vincentl/rust-photo-frame/crates/photoframe/src/config.rs

use std::collections::BTreeMap;
use std::fmt;
use std::path::{Path, PathBuf};
use std::sync::Arc;
use std::sync::atomic::{AtomicUsize, Ordering};
use std::time::{Duration, SystemTime};

use anyhow::{Context, Result, ensure};
use rand::Rng;
use rand::seq::IteratorRandom;
use serde::Deserialize;
use serde::de::{self, DeserializeOwned, Deserializer, MapAccess, SeqAccess, Unexpected, Visitor};
use serde_yaml::{Mapping, Value as YamlValue};

use crate::processing::fixed_image::FixedImageBackground;

pub use config_model::{
    AwakeScheduleConfig, GreetingScreenConfig, ScreenMessageConfig, ShowcaseConfig,
    SleepScreenConfig,
};

pub const DEFAULT_CONTROL_SOCKET_PATH: &str = "/run/photoframe/control.sock";

#[derive(Debug, Clone, Deserialize)]
#[serde(rename_all = "kebab-case", default, deny_unknown_fields)]
pub struct GlobalPhotoSettings {
    /// GPU render oversample factor relative to screen size (1.0 = native).
    pub oversample: f32,
    /// Time an image remains fully visible before starting a transition, in ms.
    pub dwell_ms: u64,
    /// Global maximum enlargement applied to the photo when fitting inside the mat.
    pub max_upscale_factor: f32,
}

impl Default for GlobalPhotoSettings {
    fn default() -> Self {
        Self {
            oversample: 1.0,
            dwell_ms: 2000,
            max_upscale_factor: 1.0,
        }
    }
}

#[derive(Debug, Clone, Deserialize)]
#[serde(rename_all = "kebab-case")]
pub struct MattingOptions {
    #[serde(default = "MattingOptions::default_minimum_percentage")]
    pub minimum_mat_percentage: f32,
    #[serde(default, flatten)]
    pub style: MattingMode,
    #[serde(default, skip_deserializing)]
    pub runtime: MattingRuntime,
}

/// Canonicalized matting configuration entries and their selection metadata.
///
/// Deserialization expands palette-based definitions (e.g. multiple
/// `fixed-color` entries) into the concrete `options` stored here. Each entry
/// in `selection` references these canonical slots by index so duplicates can
/// coexist without clobbering configuration fields.
#[derive(Debug, Clone)]
pub struct MattingConfig {
    selection: MattingSelection,
    options: Vec<MattingOptions>,
    fill_when_fits: Option<FillWhenFits>,
}

/// Opt-in behavior that renders photos whose aspect ratio is already close to
/// the display's edge-to-edge (full-bleed, cover-cropped) instead of matting
/// them. Evaluated per photo *before* mat selection.
#[derive(Debug, Clone, Copy, Deserialize)]
#[serde(rename_all = "kebab-case", deny_unknown_fields)]
pub struct FillWhenFits {
    /// A photo is eligible when filling the screen crops less than this
    /// percentage from the single overflowing axis.
    #[serde(default = "FillWhenFits::default_maximum_crop_percentage")]
    pub maximum_crop_percentage: f32,
    /// For an eligible photo, the biased-coin probability of actually skipping
    /// the mat. `1.0` always fills when eligible; `0.0` never does.
    #[serde(default = "FillWhenFits::default_skip_matting_probability")]
    pub skip_matting_probability: f32,
}

impl FillWhenFits {
    const fn default_maximum_crop_percentage() -> f32 {
        5.0
    }

    const fn default_skip_matting_probability() -> f32 {
        1.0
    }

    /// Returns true when the photo should be rendered full-bleed (no mat).
    ///
    /// Eligibility requires both that the cover-crop trims less than
    /// `maximum_crop_percentage` from the overflowing axis, and that the image
    /// is large enough to fill the screen within `max_upscale` (so a tiny but
    /// correctly-proportioned image is not blown up past the budget). When
    /// eligible, a biased coin decides the outcome.
    pub fn should_fill<R: Rng + ?Sized>(
        &self,
        img_w: u32,
        img_h: u32,
        screen_w: u32,
        screen_h: u32,
        max_upscale: f32,
        rng: &mut R,
    ) -> bool {
        let iw = img_w.max(1) as f32;
        let ih = img_h.max(1) as f32;
        let sw = screen_w.max(1) as f32;
        let sh = screen_h.max(1) as f32;

        let aspect_img = iw / ih;
        let aspect_screen = sw / sh;
        let (lo, hi) = if aspect_img <= aspect_screen {
            (aspect_img, aspect_screen)
        } else {
            (aspect_screen, aspect_img)
        };
        if hi <= 0.0 {
            return false;
        }
        let crop_fraction = 1.0 - lo / hi;
        let max_crop = (self.maximum_crop_percentage / 100.0).max(0.0);
        if crop_fraction > max_crop {
            return false;
        }

        let cover_scale = (sw / iw).max(sh / ih);
        if cover_scale > max_upscale.max(1.0) {
            return false;
        }

        let prob = self.skip_matting_probability;
        if prob >= 1.0 {
            return true;
        }
        if prob <= 0.0 {
            return false;
        }
        rng.random_bool(prob as f64)
    }

    /// Reject NaN / out-of-range values that serde cannot express as defaults.
    /// `should_fill` feeds `skip_matting_probability` straight into
    /// `rng.random_bool`, which panics for any value outside `[0.0, 1.0]`
    /// (NaN included), so this must run before any photo is rendered.
    pub fn validate(&self) -> Result<()> {
        ensure!(
            self.maximum_crop_percentage.is_finite()
                && (0.0..=100.0).contains(&self.maximum_crop_percentage),
            "matting.fill-when-fits.maximum-crop-percentage must be between 0 and 100"
        );
        ensure!(
            self.skip_matting_probability.is_finite()
                && (0.0..=1.0).contains(&self.skip_matting_probability),
            "matting.fill-when-fits.skip-matting-probability must be between 0.0 and 1.0 \
             (a 0-1 fraction, not a 0-100 percentage)"
        );
        Ok(())
    }
}

#[derive(Debug, Clone, Copy, PartialEq, Eq, Deserialize)]
#[serde(rename_all = "kebab-case")]
enum PipelineSelection {
    Fixed,
    Random,
    Sequential,
}

#[derive(Debug)]
struct PipelineEntry<K> {
    kind: K,
    fields: Vec<(String, YamlValue)>,
}

impl<'de, K> Deserialize<'de> for PipelineEntry<K>
where
    K: Deserialize<'de>,
{
    fn deserialize<D>(deserializer: D) -> Result<Self, D::Error>
    where
        D: Deserializer<'de>,
    {
        deserializer.deserialize_map(PipelineEntryVisitor::<K> {
            marker: std::marker::PhantomData,
        })
    }
}

struct PipelineEntryVisitor<K> {
    marker: std::marker::PhantomData<K>,
}

impl<'de, K> Visitor<'de> for PipelineEntryVisitor<K>
where
    K: Deserialize<'de>,
{
    type Value = PipelineEntry<K>;

    fn expecting(&self, formatter: &mut fmt::Formatter) -> fmt::Result {
        formatter.write_str("a pipeline entry map with a kind tag")
    }

    fn visit_map<A>(self, mut map: A) -> Result<Self::Value, A::Error>
    where
        A: MapAccess<'de>,
    {
        let mut kind: Option<K> = None;
        let mut fields = Vec::new();
        while let Some(key) = map.next_key::<String>()? {
            if key == "kind" {
                if kind.is_some() {
                    return Err(de::Error::duplicate_field("kind"));
                }
                kind = Some(map.next_value()?);
            } else {
                let value = map.next_value::<YamlValue>()?;
                fields.push((key, value));
            }
        }

        let kind = kind.ok_or_else(|| de::Error::missing_field("kind"))?;
        Ok(PipelineEntry { kind, fields })
    }
}

fn resolve_pipeline_selection<E>(
    requested: Option<PipelineSelection>,
    len: usize,
    context: &str,
) -> Result<PipelineSelection, E>
where
    E: de::Error,
{
    if len == 0 {
        return Err(de::Error::custom(format!(
            "{} configuration must include at least one active entry",
            context
        )));
    }

    match requested {
        Some(PipelineSelection::Fixed) => {
            if len != 1 {
                return Err(de::Error::custom(format!(
                    "{} selection 'fixed' requires exactly one active entry",
                    context
                )));
            }
            Ok(PipelineSelection::Fixed)
        }
        Some(selection) => Ok(selection),
        None => {
            if len == 1 {
                Ok(PipelineSelection::Fixed)
            } else {
                Ok(PipelineSelection::Random)
            }
        }
    }
}

#[derive(Debug, Clone)]
pub struct SequentialState {
    next_index: Arc<AtomicUsize>,
}

impl Default for SequentialState {
    fn default() -> Self {
        Self {
            next_index: Arc::new(AtomicUsize::new(0)),
        }
    }
}

impl SequentialState {
    fn next(&self, len: usize) -> usize {
        self.next_index.fetch_add(1, Ordering::Relaxed) % len
    }
}

#[derive(Debug, Clone, Copy, PartialEq, Eq)]
pub struct SelectionEntry<K: Copy> {
    pub index: usize,
    pub kind: K,
}

#[derive(Clone, Copy, Debug)]
pub struct SelectedOption<'a, K: Copy, O> {
    pub entry: SelectionEntry<K>,
    pub option: &'a O,
}

enum SelectionEntries<'a, K: Copy> {
    Single(Option<SelectionEntry<K>>),
    Slice(std::iter::Copied<std::slice::Iter<'a, SelectionEntry<K>>>),
}

impl<'a, K: Copy> SelectionEntries<'a, K> {
    fn single(entry: SelectionEntry<K>) -> Self {
        Self::Single(Some(entry))
    }

    fn from_slice(entries: &'a [SelectionEntry<K>]) -> Self {
        Self::Slice(entries.iter().copied())
    }
}

impl<'a, K: Copy> Iterator for SelectionEntries<'a, K> {
    type Item = SelectionEntry<K>;

    fn next(&mut self) -> Option<Self::Item> {
        match self {
            Self::Single(entry) => entry.take(),
            Self::Slice(iter) => iter.next(),
        }
    }
}

trait SelectedLookup<K: Copy, O> {
    fn lookup(&self, entry: SelectionEntry<K>) -> Option<&O>;
}

impl<K: Copy, O> SelectedLookup<K, O> for [O] {
    fn lookup(&self, entry: SelectionEntry<K>) -> Option<&O> {
        self.get(entry.index)
    }
}

impl<K: Copy + Ord, O> SelectedLookup<K, O> for BTreeMap<K, O> {
    fn lookup(&self, entry: SelectionEntry<K>) -> Option<&O> {
        self.get(&entry.kind)
    }
}

struct SelectedIter<'a, K: Copy, O, S>
where
    S: SelectedLookup<K, O> + ?Sized,
{
    entries: SelectionEntries<'a, K>,
    options: &'a S,
    marker: std::marker::PhantomData<&'a O>,
}

impl<'a, K: Copy, O, S> SelectedIter<'a, K, O, S>
where
    S: SelectedLookup<K, O> + ?Sized,
{
    fn new(entries: SelectionEntries<'a, K>, options: &'a S) -> Self {
        Self {
            entries,
            options,
            marker: std::marker::PhantomData,
        }
    }
}

impl<'a, K: Copy, O, S> Iterator for SelectedIter<'a, K, O, S>
where
    O: 'a,
    S: SelectedLookup<K, O> + ?Sized,
{
    type Item = SelectedOption<'a, K, O>;

    fn next(&mut self) -> Option<Self::Item> {
        for entry in self.entries.by_ref() {
            if let Some(option) = self.options.lookup(entry) {
                return Some(SelectedOption { entry, option });
            }
        }
        None
    }
}

#[derive(Debug, Clone)]
pub enum MattingSelection {
    Fixed(SelectionEntry<MattingKind>),
    Random(Arc<[SelectionEntry<MattingKind>]>),
    Sequential {
        entries: Arc<[SelectionEntry<MattingKind>]>,
        runtime: SequentialState,
    },
}

pub type SelectedMatting<'a> = SelectedOption<'a, MattingKind, MattingOptions>;

impl PartialEq for MattingSelection {
    fn eq(&self, other: &Self) -> bool {
        match (self, other) {
            (MattingSelection::Fixed(a), MattingSelection::Fixed(b)) => a == b,
            (MattingSelection::Random(a), MattingSelection::Random(b)) => a.as_ref() == b.as_ref(),
            (
                MattingSelection::Sequential { entries: a, .. },
                MattingSelection::Sequential { entries: b, .. },
            ) => a.as_ref() == b.as_ref(),
            _ => false,
        }
    }
}

impl Eq for MattingSelection {}

#[derive(Debug, Clone, Copy, PartialEq, Eq)]
pub enum StudioMatColor {
    Rgb([u8; 3]),
    PhotoAverage,
}

impl StudioMatColor {
    fn resolve(self, fallback: [f32; 3]) -> [f32; 3] {
        match self {
            StudioMatColor::Rgb(rgb) => [
                (rgb[0] as f32) / 255.0,
                (rgb[1] as f32) / 255.0,
                (rgb[2] as f32) / 255.0,
            ],
            StudioMatColor::PhotoAverage => fallback,
        }
    }
}

impl<'de> Deserialize<'de> for StudioMatColor {
    fn deserialize<D>(deserializer: D) -> Result<Self, D::Error>
    where
        D: Deserializer<'de>,
    {
        struct MatColorVisitor;

        impl<'de> Visitor<'de> for MatColorVisitor {
            type Value = StudioMatColor;

            fn expecting(&self, formatter: &mut fmt::Formatter) -> fmt::Result {
                formatter.write_str("an RGB triple or the string 'photo-average'")
            }

            fn visit_str<E>(self, value: &str) -> Result<Self::Value, E>
            where
                E: de::Error,
            {
                match value {
                    "photo-average" => Ok(StudioMatColor::PhotoAverage),
                    other => Err(de::Error::invalid_value(Unexpected::Str(other), &self)),
                }
            }

            fn visit_string<E>(self, value: String) -> Result<Self::Value, E>
            where
                E: de::Error,
            {
                self.visit_str(&value)
            }

            fn visit_seq<A>(self, mut seq: A) -> Result<Self::Value, A::Error>
            where
                A: SeqAccess<'de>,
            {
                let mut rgb = [0u8; 3];
                for (index, channel) in rgb.iter_mut().enumerate() {
                    *channel = seq
                        .next_element()?
                        .ok_or_else(|| de::Error::invalid_length(index, &self))?;
                }
                if seq.next_element::<de::IgnoredAny>()?.is_some() {
                    return Err(de::Error::invalid_length(4, &self));
                }
                Ok(StudioMatColor::Rgb(rgb))
            }
        }

        deserializer.deserialize_any(MatColorVisitor)
    }
}

#[derive(Debug, Clone, Default)]
pub struct MattingRuntime {
    fixed_color: Option<[u8; 3]>,
    studio_color: Option<StudioMatColor>,
    passe_partout_color: Option<StudioMatColor>,
    vignette_color: Option<StudioMatColor>,
    drop_shadow_color: Option<StudioMatColor>,
    fixed_image: Option<Arc<FixedImageBackground>>,
}

impl MattingRuntime {
    pub fn fixed_color(&self) -> Option<[u8; 3]> {
        self.fixed_color
    }

    pub fn studio_color(&self, fallback: [f32; 3]) -> Option<[f32; 3]> {
        self.studio_color.map(|color| color.resolve(fallback))
    }

    pub fn passe_partout_color(&self, fallback: [f32; 3]) -> Option<[f32; 3]> {
        self.passe_partout_color
            .map(|color| color.resolve(fallback))
    }

    pub fn vignette_color(&self, fallback: [f32; 3]) -> Option<[f32; 3]> {
        self.vignette_color.map(|color| color.resolve(fallback))
    }

    pub fn drop_shadow_color(&self, fallback: [f32; 3]) -> Option<[f32; 3]> {
        self.drop_shadow_color.map(|color| color.resolve(fallback))
    }

    pub fn fixed_image(&self) -> Option<Arc<FixedImageBackground>> {
        self.fixed_image.clone()
    }
}

impl MattingKind {
    const ALL: &'static [Self] = &[
        Self::FixedColor,
        Self::Blur,
        Self::Studio,
        Self::FixedImage,
        Self::Gradient,
        Self::Vignette,
        Self::CinematicBlur,
        Self::PassePartout,
        Self::DropShadow,
    ];
    const NAMES: &'static [&'static str] = &[
        "fixed-color",
        "blur",
        "studio",
        "fixed-image",
        "gradient",
        "vignette",
        "cinematic-blur",
        "passe-partout",
        "drop-shadow",
    ];

    fn as_str(&self) -> &'static str {
        match self {
            Self::FixedColor => "fixed-color",
            Self::Blur => "blur",
            Self::Studio => "studio",
            Self::FixedImage => "fixed-image",
            Self::Gradient => "gradient",
            Self::Vignette => "vignette",
            Self::CinematicBlur => "cinematic-blur",
            Self::PassePartout => "passe-partout",
            Self::DropShadow => "drop-shadow",
        }
    }
}

impl fmt::Display for MattingKind {
    fn fmt(&self, f: &mut fmt::Formatter<'_>) -> fmt::Result {
        f.write_str(self.as_str())
    }
}

impl<'de> Deserialize<'de> for MattingKind {
    fn deserialize<D>(deserializer: D) -> Result<Self, D::Error>
    where
        D: Deserializer<'de>,
    {
        let raw = String::deserialize(deserializer)?;
        for kind in Self::ALL {
            if raw == kind.as_str() {
                return Ok(*kind);
            }
        }
        Err(de::Error::unknown_variant(&raw, Self::NAMES))
    }
}

#[derive(Debug, Clone, Copy, PartialEq, Eq, PartialOrd, Ord)]
pub enum MattingKind {
    FixedColor,
    Blur,
    Studio,
    FixedImage,
    Gradient,
    Vignette,
    CinematicBlur,
    PassePartout,
    DropShadow,
}

#[derive(Debug, Clone, Deserialize)]
#[serde(tag = "type", rename_all = "kebab-case")]
pub enum MattingMode {
    FixedColor {
        #[serde(default = "MattingMode::default_fixed_color_palette")]
        colors: Vec<[u8; 3]>,
    },
    Blur {
        #[serde(default = "MattingMode::default_blur_sigma")]
        sigma: f32,
        #[serde(
            default = "MattingMode::default_blur_sample_scale",
            rename = "sample-scale"
        )]
        sample_scale: f32,
        #[serde(default)]
        backend: BlurBackend,
    },
    Studio {
        #[serde(default = "MattingMode::default_studio_colors")]
        colors: Vec<StudioMatColor>,
        #[serde(
            default = "MattingMode::default_studio_bevel_width_px",
            rename = "bevel-width-px"
        )]
        bevel_width_px: f32,
        #[serde(
            default = "MattingMode::default_studio_bevel_color",
            rename = "bevel-color"
        )]
        bevel_color: [u8; 3],
        #[serde(
            default = "MattingMode::default_studio_texture_strength",
            rename = "texture-strength"
        )]
        texture_strength: f32,
        #[serde(
            default = "MattingMode::default_studio_warp_period_px",
            rename = "warp-period-px"
        )]
        warp_period_px: f32,
        #[serde(
            default = "MattingMode::default_studio_weft_period_px",
            rename = "weft-period-px"
        )]
        weft_period_px: f32,
    },
    FixedImage {
        #[serde(
            default,
            rename = "path",
            deserialize_with = "deserialize_fixed_image_paths"
        )]
        paths: Vec<PathBuf>,
        #[serde(default)]
        fit: FixedImageFit,
    },
    Gradient {
        #[serde(
            default = "MattingMode::default_gradient_start",
            rename = "start-color"
        )]
        start_color: [u8; 3],
        #[serde(default = "MattingMode::default_gradient_end", rename = "end-color")]
        end_color: [u8; 3],
        #[serde(default)]
        direction: GradientDirection,
        #[serde(
            default = "MattingMode::default_gradient_angle",
            rename = "angle-degrees"
        )]
        angle_degrees: f32,
    },
    Vignette {
        #[serde(default = "MattingMode::default_vignette_colors")]
        colors: Vec<StudioMatColor>,
        #[serde(default = "MattingMode::default_vignette_strength")]
        strength: f32,
        #[serde(default = "MattingMode::default_vignette_radius")]
        radius: f32,
        #[serde(default = "MattingMode::default_vignette_softness")]
        softness: f32,
    },
    CinematicBlur {
        #[serde(default = "MattingMode::default_blur_sigma")]
        sigma: f32,
        #[serde(
            default = "MattingMode::default_blur_sample_scale",
            rename = "sample-scale"
        )]
        sample_scale: f32,
        #[serde(default)]
        backend: BlurBackend,
        #[serde(default = "MattingMode::default_cinematic_darken")]
        darken: f32,
        #[serde(
            default = "MattingMode::default_cinematic_vignette_strength",
            rename = "vignette-strength"
        )]
        vignette_strength: f32,
    },
    PassePartout {
        #[serde(default = "MattingMode::default_studio_colors")]
        colors: Vec<StudioMatColor>,
        #[serde(
            default = "MattingMode::default_studio_bevel_width_px",
            rename = "bevel-width-px"
        )]
        bevel_width_px: f32,
        #[serde(
            default = "MattingMode::default_studio_bevel_color",
            rename = "bevel-color"
        )]
        bevel_color: [u8; 3],
    },
    DropShadow {
        #[serde(default = "MattingMode::default_drop_shadow_colors")]
        colors: Vec<StudioMatColor>,
        #[serde(
            default = "MattingMode::default_drop_shadow_shadow_color",
            rename = "shadow-color"
        )]
        shadow_color: [u8; 3],
        #[serde(
            default = "MattingMode::default_drop_shadow_opacity",
            rename = "shadow-opacity"
        )]
        shadow_opacity: f32,
        #[serde(
            default = "MattingMode::default_drop_shadow_blur_px",
            rename = "shadow-blur-px"
        )]
        shadow_blur_px: f32,
        #[serde(
            default = "MattingMode::default_drop_shadow_offset_px",
            rename = "shadow-offset-px"
        )]
        shadow_offset_px: [i32; 2],
    },
}

#[derive(Debug, Clone, Copy, Deserialize)]
#[serde(rename_all = "kebab-case")]
pub enum BlurBackend {
    Cpu,
    Neon,
}

#[derive(Debug, Clone, Copy, PartialEq, Eq, Deserialize)]
#[serde(rename_all = "kebab-case")]
pub enum FixedImageFit {
    Cover,
    Contain,
    Stretch,
}

impl Default for BlurBackend {
    fn default() -> Self {
        Self::Neon
    }
}

impl Default for FixedImageFit {
    fn default() -> Self {
        Self::Cover
    }
}

#[derive(Debug, Clone, Copy, PartialEq, Eq, Deserialize)]
#[serde(rename_all = "kebab-case")]
pub enum GradientDirection {
    Vertical,
    Horizontal,
    Radial,
}

impl Default for GradientDirection {
    fn default() -> Self {
        Self::Vertical
    }
}

fn deserialize_fixed_image_paths<'de, D>(deserializer: D) -> Result<Vec<PathBuf>, D::Error>
where
    D: Deserializer<'de>,
{
    struct PathsVisitor;

    impl<'de> Visitor<'de> for PathsVisitor {
        type Value = Vec<PathBuf>;

        fn expecting(&self, formatter: &mut fmt::Formatter<'_>) -> fmt::Result {
            formatter.write_str("a path string or a list of paths")
        }

        fn visit_str<E>(self, value: &str) -> Result<Self::Value, E>
        where
            E: de::Error,
        {
            Ok(vec![PathBuf::from(value)])
        }

        fn visit_string<E>(self, value: String) -> Result<Self::Value, E>
        where
            E: de::Error,
        {
            self.visit_str(&value)
        }

        fn visit_seq<A>(self, mut seq: A) -> Result<Self::Value, A::Error>
        where
            A: de::SeqAccess<'de>,
        {
            let mut paths = Vec::new();
            while let Some(path) = seq.next_element::<PathBuf>()? {
                paths.push(path);
            }
            Ok(paths)
        }
    }

    deserializer.deserialize_any(PathsVisitor)
}

impl Default for MattingOptions {
    fn default() -> Self {
        Self {
            minimum_mat_percentage: Self::default_minimum_percentage(),
            style: MattingMode::default(),
            runtime: MattingRuntime::default(),
        }
    }
}

impl MattingOptions {
    const fn default_minimum_percentage() -> f32 {
        0.0
    }

    pub fn prepare_runtime(&mut self) -> Result<()> {
        ensure!(
            self.minimum_mat_percentage.is_finite()
                && (0.0..=100.0).contains(&self.minimum_mat_percentage),
            "matting.minimum-mat-percentage must be between 0 and 100 (got {})",
            self.minimum_mat_percentage
        );
        self.runtime = MattingRuntime::default();
        if let MattingMode::FixedColor { colors, .. } = &self.style {
            ensure!(
                !colors.is_empty(),
                "matting.fixed-color.colors must include at least one entry",
            );
            self.runtime.fixed_color = colors.first().copied();
        }
        if let MattingMode::Studio { colors, .. } = &self.style {
            ensure!(
                !colors.is_empty(),
                "matting.studio.colors must include at least one entry",
            );
            self.runtime.studio_color = colors.first().copied();
        }
        if let MattingMode::PassePartout { colors, .. } = &self.style {
            ensure!(
                !colors.is_empty(),
                "matting.passe-partout.colors must include at least one entry",
            );
            self.runtime.passe_partout_color = colors.first().copied();
        }
        if let MattingMode::Vignette { colors, .. } = &self.style {
            ensure!(
                !colors.is_empty(),
                "matting.vignette.colors must include at least one entry",
            );
            self.runtime.vignette_color = colors.first().copied();
        }
        if let MattingMode::DropShadow { colors, .. } = &self.style {
            ensure!(
                !colors.is_empty(),
                "matting.drop-shadow.colors must include at least one entry",
            );
            self.runtime.drop_shadow_color = colors.first().copied();
        }
        if let MattingMode::FixedImage { paths, .. } = &self.style {
            if paths.is_empty() {
                return Ok(());
            }

            for path in paths {
                match FixedImageBackground::new(path.clone()) {
                    Ok(background) => {
                        self.runtime.fixed_image = Some(Arc::new(background));
                        break;
                    }
                    Err(err) => {
                        tracing::warn!(
                            path = %path.display(),
                            error = %err,
                            "skipping fixed background image that failed to prepare"
                        );
                    }
                }
            }

            if self.runtime.fixed_image.is_none() {
                tracing::warn!(
                    "all configured fixed-image backgrounds failed to load; disabling fixed-image matting"
                );
            }
        }
        Ok(())
    }

    pub fn fixed_color(&self) -> Option<[u8; 3]> {
        match &self.style {
            MattingMode::FixedColor { colors, .. } => colors.first().copied(),
            _ => None,
        }
    }
}

impl MattingOptions {
    fn with_kind(kind: MattingKind, base: MattingOptionBuilder) -> Self {
        let style = match kind {
            MattingKind::FixedColor => MattingMode::FixedColor {
                colors: base
                    .fixed_colors
                    .unwrap_or_else(MattingMode::default_fixed_color_palette),
            },
            MattingKind::Blur => MattingMode::Blur {
                sigma: base.sigma.unwrap_or_else(MattingMode::default_blur_sigma),
                sample_scale: base
                    .sample_scale
                    .unwrap_or_else(MattingMode::default_blur_sample_scale),
                backend: base.blur_backend.unwrap_or_default(),
            },
            MattingKind::Studio => MattingMode::Studio {
                colors: base
                    .studio_colors
                    .unwrap_or_else(MattingMode::default_studio_colors),
                bevel_width_px: base
                    .bevel_width_px
                    .unwrap_or_else(MattingMode::default_studio_bevel_width_px),
                bevel_color: base
                    .bevel_color
                    .unwrap_or_else(MattingMode::default_studio_bevel_color),
                texture_strength: base
                    .texture_strength
                    .unwrap_or_else(MattingMode::default_studio_texture_strength),
                warp_period_px: base
                    .warp_period_px
                    .unwrap_or_else(MattingMode::default_studio_warp_period_px),
                weft_period_px: base
                    .weft_period_px
                    .unwrap_or_else(MattingMode::default_studio_weft_period_px),
            },
            MattingKind::FixedImage => MattingMode::FixedImage {
                paths: base
                    .fixed_image_paths
                    .expect("fixed-image matting must supply a path"),
                fit: base.fixed_image_fit.unwrap_or_default(),
            },
            MattingKind::Gradient => MattingMode::Gradient {
                start_color: base
                    .gradient_start
                    .unwrap_or_else(MattingMode::default_gradient_start),
                end_color: base
                    .gradient_end
                    .unwrap_or_else(MattingMode::default_gradient_end),
                direction: base.gradient_direction.unwrap_or_default(),
                angle_degrees: base
                    .gradient_angle
                    .unwrap_or_else(MattingMode::default_gradient_angle),
            },
            MattingKind::Vignette => MattingMode::Vignette {
                colors: base
                    .vignette_colors
                    .unwrap_or_else(MattingMode::default_vignette_colors),
                strength: base
                    .vignette_strength
                    .unwrap_or_else(MattingMode::default_vignette_strength),
                radius: base
                    .vignette_radius
                    .unwrap_or_else(MattingMode::default_vignette_radius),
                softness: base
                    .vignette_softness
                    .unwrap_or_else(MattingMode::default_vignette_softness),
            },
            MattingKind::CinematicBlur => MattingMode::CinematicBlur {
                sigma: base.sigma.unwrap_or_else(MattingMode::default_blur_sigma),
                sample_scale: base
                    .sample_scale
                    .unwrap_or_else(MattingMode::default_blur_sample_scale),
                backend: base.blur_backend.unwrap_or_default(),
                darken: base
                    .cinematic_darken
                    .unwrap_or_else(MattingMode::default_cinematic_darken),
                vignette_strength: base
                    .cinematic_vignette_strength
                    .unwrap_or_else(MattingMode::default_cinematic_vignette_strength),
            },
            MattingKind::PassePartout => MattingMode::PassePartout {
                colors: base
                    .passe_partout_colors
                    .unwrap_or_else(MattingMode::default_studio_colors),
                bevel_width_px: base
                    .bevel_width_px
                    .unwrap_or_else(MattingMode::default_studio_bevel_width_px),
                bevel_color: base
                    .bevel_color
                    .unwrap_or_else(MattingMode::default_studio_bevel_color),
            },
            MattingKind::DropShadow => MattingMode::DropShadow {
                colors: base
                    .drop_shadow_colors
                    .unwrap_or_else(MattingMode::default_drop_shadow_colors),
                shadow_color: base
                    .drop_shadow_shadow_color
                    .unwrap_or_else(MattingMode::default_drop_shadow_shadow_color),
                shadow_opacity: base
                    .drop_shadow_opacity
                    .unwrap_or_else(MattingMode::default_drop_shadow_opacity),
                shadow_blur_px: base
                    .drop_shadow_blur_px
                    .unwrap_or_else(MattingMode::default_drop_shadow_blur_px),
                shadow_offset_px: base
                    .drop_shadow_offset_px
                    .unwrap_or_else(MattingMode::default_drop_shadow_offset_px),
            },
        };
        Self {
            minimum_mat_percentage: base
                .minimum_mat_percentage
                .unwrap_or_else(Self::default_minimum_percentage),
            style,
            runtime: MattingRuntime::default(),
        }
    }

    /// Build a `MattingOptions` with showcase-appropriate defaults for `kind`.
    /// For `FixedImage`, `fixed_image_path` must be `Some` (callers skip it when None).
    pub(crate) fn default_for_showcase(
        kind: MattingKind,
        minimum_mat_percentage: f32,
        fixed_image_path: Option<PathBuf>,
    ) -> Option<Self> {
        let mut builder = MattingOptionBuilder {
            minimum_mat_percentage: Some(minimum_mat_percentage),
            ..Default::default()
        };
        if kind == MattingKind::FixedImage {
            builder.fixed_image_paths = Some(vec![fixed_image_path?]);
        }
        let mut opt = MattingOptions::with_kind(kind, builder);
        opt.minimum_mat_percentage = minimum_mat_percentage;
        Some(opt)
    }

    pub(crate) fn kind(&self) -> MattingKind {
        match &self.style {
            MattingMode::FixedColor { .. } => MattingKind::FixedColor,
            MattingMode::Blur { .. } => MattingKind::Blur,
            MattingMode::Studio { .. } => MattingKind::Studio,
            MattingMode::FixedImage { .. } => MattingKind::FixedImage,
            MattingMode::Gradient { .. } => MattingKind::Gradient,
            MattingMode::Vignette { .. } => MattingKind::Vignette,
            MattingMode::CinematicBlur { .. } => MattingKind::CinematicBlur,
            MattingMode::PassePartout { .. } => MattingKind::PassePartout,
            MattingMode::DropShadow { .. } => MattingKind::DropShadow,
        }
    }
}

#[derive(Default, Clone)]
struct MattingOptionBuilder {
    minimum_mat_percentage: Option<f32>,
    fixed_colors: Option<Vec<[u8; 3]>>,
    sigma: Option<f32>,
    sample_scale: Option<f32>,
    blur_backend: Option<BlurBackend>,
    bevel_width_px: Option<f32>,
    bevel_color: Option<[u8; 3]>,
    texture_strength: Option<f32>,
    warp_period_px: Option<f32>,
    weft_period_px: Option<f32>,
    studio_colors: Option<Vec<StudioMatColor>>,
    fixed_image_paths: Option<Vec<PathBuf>>,
    fixed_image_fit: Option<FixedImageFit>,
    gradient_start: Option<[u8; 3]>,
    gradient_end: Option<[u8; 3]>,
    gradient_direction: Option<GradientDirection>,
    gradient_angle: Option<f32>,
    vignette_colors: Option<Vec<StudioMatColor>>,
    vignette_strength: Option<f32>,
    vignette_radius: Option<f32>,
    vignette_softness: Option<f32>,
    cinematic_darken: Option<f32>,
    cinematic_vignette_strength: Option<f32>,
    passe_partout_colors: Option<Vec<StudioMatColor>>,
    drop_shadow_colors: Option<Vec<StudioMatColor>>,
    drop_shadow_shadow_color: Option<[u8; 3]>,
    drop_shadow_opacity: Option<f32>,
    drop_shadow_blur_px: Option<f32>,
    drop_shadow_offset_px: Option<[i32; 2]>,
}

fn inline_value_to<T, E>(value: YamlValue) -> Result<T, E>
where
    T: DeserializeOwned,
    E: de::Error,
{
    serde_yaml::from_value(value).map_err(|err| de::Error::custom(err.to_string()))
}

fn inline_value_to_fixed_image_paths<E>(value: YamlValue) -> Result<Vec<PathBuf>, E>
where
    E: de::Error,
{
    match value {
        YamlValue::String(path) => Ok(vec![PathBuf::from(path)]),
        YamlValue::Sequence(entries) => {
            let mut paths = Vec::with_capacity(entries.len());
            for entry in entries {
                paths.push(inline_value_to::<PathBuf, E>(entry)?);
            }
            Ok(paths)
        }
        other => Err(de::Error::custom(format!(
            "fixed-image.path must be a string or list of paths, got {:?}",
            other
        ))),
    }
}

fn apply_inline_field<E>(
    builder: &mut MattingOptionBuilder,
    kind: MattingKind,
    key: &str,
    value: YamlValue,
) -> Result<(), E>
where
    E: de::Error,
{
    match key {
        "minimum-mat-percentage" => {
            if builder.minimum_mat_percentage.is_some() {
                return Err(de::Error::duplicate_field("minimum-mat-percentage"));
            }
            builder.minimum_mat_percentage = Some(inline_value_to::<f32, E>(value)?);
        }
        other => match kind {
            MattingKind::FixedColor => match other {
                "colors" => {
                    if builder.fixed_colors.is_some() {
                        return Err(de::Error::duplicate_field("colors"));
                    }
                    builder.fixed_colors = Some(inline_value_to::<Vec<[u8; 3]>, E>(value)?);
                }
                "color" => {
                    if builder.fixed_colors.is_some() {
                        return Err(de::Error::duplicate_field("color"));
                    }
                    let color = inline_value_to::<[u8; 3], E>(value)?;
                    builder.fixed_colors = Some(vec![color]);
                }
                _ => {
                    return Err(de::Error::unknown_field(
                        other,
                        &["colors", "color", "minimum-mat-percentage"],
                    ));
                }
            },
            MattingKind::Blur => match other {
                "sigma" => {
                    if builder.sigma.is_some() {
                        return Err(de::Error::duplicate_field("sigma"));
                    }
                    builder.sigma = Some(inline_value_to::<f32, E>(value)?);
                }
                "sample-scale" => {
                    if builder.sample_scale.is_some() {
                        return Err(de::Error::duplicate_field("sample-scale"));
                    }
                    builder.sample_scale = Some(inline_value_to::<f32, E>(value)?);
                }
                "backend" => {
                    if builder.blur_backend.is_some() {
                        return Err(de::Error::duplicate_field("backend"));
                    }
                    builder.blur_backend = Some(inline_value_to::<BlurBackend, E>(value)?);
                }
                _ => {
                    return Err(de::Error::unknown_field(
                        other,
                        &["sigma", "sample-scale", "backend", "minimum-mat-percentage"],
                    ));
                }
            },
            MattingKind::Studio => match other {
                "colors" => {
                    if builder.studio_colors.is_some() {
                        return Err(de::Error::duplicate_field("colors"));
                    }
                    builder.studio_colors = Some(inline_value_to::<Vec<StudioMatColor>, E>(value)?);
                }
                "color" => {
                    if builder.studio_colors.is_some() {
                        return Err(de::Error::duplicate_field("color"));
                    }
                    builder.studio_colors =
                        Some(vec![inline_value_to::<StudioMatColor, E>(value)?]);
                }
                "bevel-width-px" => {
                    if builder.bevel_width_px.is_some() {
                        return Err(de::Error::duplicate_field("bevel-width-px"));
                    }
                    builder.bevel_width_px = Some(inline_value_to::<f32, E>(value)?);
                }
                "bevel-color" => {
                    if builder.bevel_color.is_some() {
                        return Err(de::Error::duplicate_field("bevel-color"));
                    }
                    builder.bevel_color = Some(inline_value_to::<[u8; 3], E>(value)?);
                }
                "texture-strength" => {
                    if builder.texture_strength.is_some() {
                        return Err(de::Error::duplicate_field("texture-strength"));
                    }
                    builder.texture_strength = Some(inline_value_to::<f32, E>(value)?);
                }
                "warp-period-px" => {
                    if builder.warp_period_px.is_some() {
                        return Err(de::Error::duplicate_field("warp-period-px"));
                    }
                    builder.warp_period_px = Some(inline_value_to::<f32, E>(value)?);
                }
                "weft-period-px" => {
                    if builder.weft_period_px.is_some() {
                        return Err(de::Error::duplicate_field("weft-period-px"));
                    }
                    builder.weft_period_px = Some(inline_value_to::<f32, E>(value)?);
                }
                _ => {
                    return Err(de::Error::unknown_field(
                        other,
                        &[
                            "colors",
                            "color",
                            "bevel-width-px",
                            "bevel-color",
                            "texture-strength",
                            "warp-period-px",
                            "weft-period-px",
                            "minimum-mat-percentage",
                        ],
                    ));
                }
            },
            MattingKind::FixedImage => match other {
                "path" => {
                    if builder.fixed_image_paths.is_some() {
                        return Err(de::Error::duplicate_field("path"));
                    }
                    builder.fixed_image_paths =
                        Some(inline_value_to_fixed_image_paths::<E>(value)?);
                }
                "fit" => {
                    if builder.fixed_image_fit.is_some() {
                        return Err(de::Error::duplicate_field("fit"));
                    }
                    builder.fixed_image_fit = Some(inline_value_to::<FixedImageFit, E>(value)?);
                }
                _ => {
                    return Err(de::Error::unknown_field(
                        other,
                        &["path", "fit", "minimum-mat-percentage"],
                    ));
                }
            },
            MattingKind::Gradient => match other {
                "start-color" => {
                    if builder.gradient_start.is_some() {
                        return Err(de::Error::duplicate_field("start-color"));
                    }
                    builder.gradient_start = Some(inline_value_to::<[u8; 3], E>(value)?);
                }
                "end-color" => {
                    if builder.gradient_end.is_some() {
                        return Err(de::Error::duplicate_field("end-color"));
                    }
                    builder.gradient_end = Some(inline_value_to::<[u8; 3], E>(value)?);
                }
                "direction" => {
                    if builder.gradient_direction.is_some() {
                        return Err(de::Error::duplicate_field("direction"));
                    }
                    builder.gradient_direction =
                        Some(inline_value_to::<GradientDirection, E>(value)?);
                }
                "angle-degrees" => {
                    if builder.gradient_angle.is_some() {
                        return Err(de::Error::duplicate_field("angle-degrees"));
                    }
                    builder.gradient_angle = Some(inline_value_to::<f32, E>(value)?);
                }
                _ => {
                    return Err(de::Error::unknown_field(
                        other,
                        &[
                            "start-color",
                            "end-color",
                            "direction",
                            "angle-degrees",
                            "minimum-mat-percentage",
                        ],
                    ));
                }
            },
            MattingKind::Vignette => match other {
                "color" => {
                    if builder.vignette_colors.is_some() {
                        return Err(de::Error::duplicate_field("color"));
                    }
                    builder.vignette_colors =
                        Some(vec![inline_value_to::<StudioMatColor, E>(value)?]);
                }
                "colors" => {
                    if builder.vignette_colors.is_some() {
                        return Err(de::Error::duplicate_field("colors"));
                    }
                    builder.vignette_colors =
                        Some(inline_value_to::<Vec<StudioMatColor>, E>(value)?);
                }
                "strength" => {
                    if builder.vignette_strength.is_some() {
                        return Err(de::Error::duplicate_field("strength"));
                    }
                    builder.vignette_strength = Some(inline_value_to::<f32, E>(value)?);
                }
                "radius" => {
                    if builder.vignette_radius.is_some() {
                        return Err(de::Error::duplicate_field("radius"));
                    }
                    builder.vignette_radius = Some(inline_value_to::<f32, E>(value)?);
                }
                "softness" => {
                    if builder.vignette_softness.is_some() {
                        return Err(de::Error::duplicate_field("softness"));
                    }
                    builder.vignette_softness = Some(inline_value_to::<f32, E>(value)?);
                }
                _ => {
                    return Err(de::Error::unknown_field(
                        other,
                        &[
                            "color",
                            "colors",
                            "strength",
                            "radius",
                            "softness",
                            "minimum-mat-percentage",
                        ],
                    ));
                }
            },
            MattingKind::CinematicBlur => match other {
                "sigma" => {
                    if builder.sigma.is_some() {
                        return Err(de::Error::duplicate_field("sigma"));
                    }
                    builder.sigma = Some(inline_value_to::<f32, E>(value)?);
                }
                "sample-scale" => {
                    if builder.sample_scale.is_some() {
                        return Err(de::Error::duplicate_field("sample-scale"));
                    }
                    builder.sample_scale = Some(inline_value_to::<f32, E>(value)?);
                }
                "backend" => {
                    if builder.blur_backend.is_some() {
                        return Err(de::Error::duplicate_field("backend"));
                    }
                    builder.blur_backend = Some(inline_value_to::<BlurBackend, E>(value)?);
                }
                "darken" => {
                    if builder.cinematic_darken.is_some() {
                        return Err(de::Error::duplicate_field("darken"));
                    }
                    builder.cinematic_darken = Some(inline_value_to::<f32, E>(value)?);
                }
                "vignette-strength" => {
                    if builder.cinematic_vignette_strength.is_some() {
                        return Err(de::Error::duplicate_field("vignette-strength"));
                    }
                    builder.cinematic_vignette_strength = Some(inline_value_to::<f32, E>(value)?);
                }
                _ => {
                    return Err(de::Error::unknown_field(
                        other,
                        &[
                            "sigma",
                            "sample-scale",
                            "backend",
                            "darken",
                            "vignette-strength",
                            "minimum-mat-percentage",
                        ],
                    ));
                }
            },
            MattingKind::PassePartout => match other {
                "colors" => {
                    if builder.passe_partout_colors.is_some() {
                        return Err(de::Error::duplicate_field("colors"));
                    }
                    builder.passe_partout_colors =
                        Some(inline_value_to::<Vec<StudioMatColor>, E>(value)?);
                }
                "color" => {
                    if builder.passe_partout_colors.is_some() {
                        return Err(de::Error::duplicate_field("color"));
                    }
                    builder.passe_partout_colors =
                        Some(vec![inline_value_to::<StudioMatColor, E>(value)?]);
                }
                "bevel-width-px" => {
                    if builder.bevel_width_px.is_some() {
                        return Err(de::Error::duplicate_field("bevel-width-px"));
                    }
                    builder.bevel_width_px = Some(inline_value_to::<f32, E>(value)?);
                }
                "bevel-color" => {
                    if builder.bevel_color.is_some() {
                        return Err(de::Error::duplicate_field("bevel-color"));
                    }
                    builder.bevel_color = Some(inline_value_to::<[u8; 3], E>(value)?);
                }
                _ => {
                    return Err(de::Error::unknown_field(
                        other,
                        &[
                            "colors",
                            "color",
                            "bevel-width-px",
                            "bevel-color",
                            "minimum-mat-percentage",
                        ],
                    ));
                }
            },
            MattingKind::DropShadow => match other {
                "color" => {
                    if builder.drop_shadow_colors.is_some() {
                        return Err(de::Error::duplicate_field("color"));
                    }
                    builder.drop_shadow_colors =
                        Some(vec![inline_value_to::<StudioMatColor, E>(value)?]);
                }
                "colors" => {
                    if builder.drop_shadow_colors.is_some() {
                        return Err(de::Error::duplicate_field("colors"));
                    }
                    builder.drop_shadow_colors =
                        Some(inline_value_to::<Vec<StudioMatColor>, E>(value)?);
                }
                "shadow-color" => {
                    if builder.drop_shadow_shadow_color.is_some() {
                        return Err(de::Error::duplicate_field("shadow-color"));
                    }
                    builder.drop_shadow_shadow_color = Some(inline_value_to::<[u8; 3], E>(value)?);
                }
                "shadow-opacity" => {
                    if builder.drop_shadow_opacity.is_some() {
                        return Err(de::Error::duplicate_field("shadow-opacity"));
                    }
                    builder.drop_shadow_opacity = Some(inline_value_to::<f32, E>(value)?);
                }
                "shadow-blur-px" => {
                    if builder.drop_shadow_blur_px.is_some() {
                        return Err(de::Error::duplicate_field("shadow-blur-px"));
                    }
                    builder.drop_shadow_blur_px = Some(inline_value_to::<f32, E>(value)?);
                }
                "shadow-offset-px" => {
                    if builder.drop_shadow_offset_px.is_some() {
                        return Err(de::Error::duplicate_field("shadow-offset-px"));
                    }
                    builder.drop_shadow_offset_px = Some(inline_value_to::<[i32; 2], E>(value)?);
                }
                _ => {
                    return Err(de::Error::unknown_field(
                        other,
                        &[
                            "color",
                            "colors",
                            "shadow-color",
                            "shadow-opacity",
                            "shadow-blur-px",
                            "shadow-offset-px",
                            "minimum-mat-percentage",
                        ],
                    ));
                }
            },
        },
    }
    Ok(())
}

impl MattingOptionBuilder {
    fn into_canonical_options(self, kind: MattingKind) -> Vec<MattingOptions> {
        match kind {
            MattingKind::FixedColor => {
                if let Some(colors) = &self.fixed_colors
                    && colors.len() > 1
                {
                    let mut options = Vec::with_capacity(colors.len());
                    for color in colors.iter().copied() {
                        let mut builder = self.clone();
                        builder.fixed_colors = Some(vec![color]);
                        options.push(MattingOptions::with_kind(kind, builder));
                    }
                    return options;
                }
            }
            MattingKind::Studio => {
                if let Some(colors) = &self.studio_colors
                    && colors.len() > 1
                {
                    let mut options = Vec::with_capacity(colors.len());
                    for color in colors.iter().copied() {
                        let mut builder = self.clone();
                        builder.studio_colors = Some(vec![color]);
                        options.push(MattingOptions::with_kind(kind, builder));
                    }
                    return options;
                }
            }
            MattingKind::FixedImage => {
                if let Some(paths) = &self.fixed_image_paths
                    && paths.len() > 1
                {
                    let mut options = Vec::with_capacity(paths.len());
                    for path in paths.iter().cloned() {
                        let mut builder = self.clone();
                        builder.fixed_image_paths = Some(vec![path]);
                        options.push(MattingOptions::with_kind(kind, builder));
                    }
                    return options;
                }
            }
            MattingKind::Blur => {}
            MattingKind::PassePartout => {
                if let Some(colors) = &self.passe_partout_colors
                    && colors.len() > 1
                {
                    let mut options = Vec::with_capacity(colors.len());
                    for color in colors.iter().copied() {
                        let mut builder = self.clone();
                        builder.passe_partout_colors = Some(vec![color]);
                        options.push(MattingOptions::with_kind(kind, builder));
                    }
                    return options;
                }
            }
            MattingKind::Vignette => {
                if let Some(colors) = &self.vignette_colors
                    && colors.len() > 1
                {
                    let mut options = Vec::with_capacity(colors.len());
                    for color in colors.iter().copied() {
                        let mut builder = self.clone();
                        builder.vignette_colors = Some(vec![color]);
                        options.push(MattingOptions::with_kind(kind, builder));
                    }
                    return options;
                }
            }
            MattingKind::DropShadow => {
                if let Some(colors) = &self.drop_shadow_colors
                    && colors.len() > 1
                {
                    let mut options = Vec::with_capacity(colors.len());
                    for color in colors.iter().copied() {
                        let mut builder = self.clone();
                        builder.drop_shadow_colors = Some(vec![color]);
                        options.push(MattingOptions::with_kind(kind, builder));
                    }
                    return options;
                }
            }
            MattingKind::Gradient | MattingKind::CinematicBlur => {}
        }

        vec![MattingOptions::with_kind(kind, self)]
    }
}

impl Default for MattingConfig {
    fn default() -> Self {
        let options = vec![MattingOptions::default()];
        Self {
            selection: MattingSelection::Fixed(SelectionEntry {
                index: 0,
                kind: MattingKind::FixedColor,
            }),
            options,
            fill_when_fits: None,
        }
    }
}

impl<'de> Deserialize<'de> for MattingConfig {
    fn deserialize<D>(deserializer: D) -> Result<Self, D::Error>
    where
        D: Deserializer<'de>,
    {
        deserializer.deserialize_map(MattingConfigVisitor)
    }
}

struct MattingConfigVisitor;

impl<'de> Visitor<'de> for MattingConfigVisitor {
    type Value = MattingConfig;

    fn expecting(&self, formatter: &mut fmt::Formatter) -> fmt::Result {
        formatter.write_str("a matting configuration map")
    }

    fn visit_map<A>(self, mut map: A) -> Result<Self::Value, A::Error>
    where
        A: MapAccess<'de>,
    {
        let mut selection: Option<PipelineSelection> = None;
        let mut active: Option<Vec<PipelineEntry<MattingKind>>> = None;
        let mut fill_when_fits: Option<FillWhenFits> = None;
        while let Some(key) = map.next_key::<String>()? {
            match key.as_str() {
                "selection" => {
                    if selection.is_some() {
                        return Err(de::Error::duplicate_field("selection"));
                    }
                    selection = Some(map.next_value()?);
                }
                "active" => {
                    if active.is_some() {
                        return Err(de::Error::duplicate_field("active"));
                    }
                    active = Some(map.next_value()?);
                }
                "fill-when-fits" => {
                    if fill_when_fits.is_some() {
                        return Err(de::Error::duplicate_field("fill-when-fits"));
                    }
                    fill_when_fits = Some(map.next_value()?);
                }
                _ => {
                    return Err(de::Error::unknown_field(
                        key.as_str(),
                        &["selection", "active", "fill-when-fits"],
                    ));
                }
            }
        }

        let active_entries = active.ok_or_else(|| de::Error::missing_field("active"))?;
        let mut options = Vec::new();
        let mut entries = Vec::new();
        for entry in active_entries.into_iter() {
            let kind = entry.kind;
            let mut builder = MattingOptionBuilder::default();
            for (field, value) in entry.fields {
                apply_inline_field::<A::Error>(&mut builder, kind, &field, value)?;
            }
            if matches!(kind, MattingKind::FixedImage) && builder.fixed_image_paths.is_none() {
                return Err(de::Error::custom(
                    "matting.active entry for fixed-image must include a path",
                ));
            }
            let canonical = builder.into_canonical_options(kind);
            for option in canonical {
                let index = options.len();
                let kind = option.kind();
                options.push(option);
                entries.push(SelectionEntry { index, kind });
            }
        }

        let resolved_selection =
            resolve_pipeline_selection::<A::Error>(selection, options.len(), "matting")?;

        let entries: Arc<[SelectionEntry<MattingKind>]> = entries.into();

        let selection = match resolved_selection {
            PipelineSelection::Fixed => MattingSelection::Fixed(entries[0]),
            PipelineSelection::Random => MattingSelection::Random(entries.clone()),
            PipelineSelection::Sequential => MattingSelection::Sequential {
                entries: entries.clone(),
                runtime: SequentialState::default(),
            },
        };

        Ok(MattingConfig {
            selection,
            options,
            fill_when_fits,
        })
    }
}

impl MattingConfig {
    /// Exposed for integration tests to introspect the parsed selection strategy.
    pub fn selection(&self) -> &MattingSelection {
        &self.selection
    }

    /// Exposed for integration tests to inspect the configured matting options.
    pub fn options(&self) -> &[MattingOptions] {
        &self.options
    }

    /// Opt-in full-bleed behavior for photos already close to the screen aspect.
    pub fn fill_when_fits(&self) -> Option<&FillWhenFits> {
        self.fill_when_fits.as_ref()
    }

    fn selection_entries(&self) -> SelectionEntries<'_, MattingKind> {
        match self.selection() {
            MattingSelection::Fixed(entry) => SelectionEntries::single(*entry),
            MattingSelection::Random(entries) => SelectionEntries::from_slice(entries.as_ref()),
            MattingSelection::Sequential { entries, .. } => {
                SelectionEntries::from_slice(entries.as_ref())
            }
        }
    }

    pub fn iter_selected(&self) -> impl Iterator<Item = SelectedMatting<'_>> {
        SelectedIter::new(self.selection_entries(), self.options.as_slice())
    }

    pub fn primary_selected(&self) -> Option<SelectedMatting<'_>> {
        self.iter_selected().next()
    }

    #[allow(dead_code)]
    pub fn selected_by_index(&self, index: usize) -> Option<SelectedMatting<'_>> {
        self.iter_selected()
            .find(|selected| selected.entry.index == index)
    }

    pub fn select_active<R: Rng + ?Sized>(&self, rng: &mut R) -> SelectedMatting<'_> {
        let entry = match self.selection() {
            MattingSelection::Fixed(entry) => *entry,
            MattingSelection::Random(entries) => *entries
                .iter()
                .choose(rng)
                .expect("validated random matting should have options"),
            MattingSelection::Sequential { entries, runtime } => {
                let index = runtime.next(entries.len());
                entries[index]
            }
        };

        let option = self
            .options
            .get(entry.index)
            .expect("validated matting selection should resolve to an option");
        SelectedOption { entry, option }
    }

    pub fn primary_option(&self) -> Option<&MattingOptions> {
        self.primary_selected().map(|selected| selected.option)
    }

    pub fn prepare_runtime(&mut self) -> Result<()> {
        ensure!(
            !self.options().is_empty(),
            "matting configuration must include at least one active entry"
        );
        for option in self.options.iter_mut() {
            option
                .prepare_runtime()
                .context("failed to prepare matting resources")?;
        }
        Ok(())
    }

    #[allow(dead_code)]
    pub fn choose_option<R: Rng + ?Sized>(&self, rng: &mut R) -> MattingOptions {
        self.select_active(rng).option.clone()
    }

    /// Build a sequential `MattingConfig` from a list of options.
    /// Used by showcase mode to replace the author-supplied matting list.
    pub(crate) fn sequential_from(options: Vec<MattingOptions>) -> Self {
        let entries: Arc<[SelectionEntry<MattingKind>]> = options
            .iter()
            .enumerate()
            .map(|(index, opt)| SelectionEntry {
                index,
                kind: opt.kind(),
            })
            .collect::<Vec<_>>()
            .into();
        Self {
            selection: MattingSelection::Sequential {
                entries,
                runtime: SequentialState::default(),
            },
            options,
            fill_when_fits: None,
        }
    }
}

impl Default for MattingMode {
    fn default() -> Self {
        Self::FixedColor {
            colors: Self::default_fixed_color_palette(),
        }
    }
}

impl MattingMode {
    const fn default_color() -> [u8; 3] {
        [0, 0, 0]
    }

    fn default_fixed_color_palette() -> Vec<[u8; 3]> {
        vec![Self::default_color()]
    }

    fn default_studio_colors() -> Vec<StudioMatColor> {
        vec![StudioMatColor::PhotoAverage]
    }

    const fn default_blur_sigma() -> f32 {
        32.0
    }

    pub const fn default_blur_sample_scale() -> f32 {
        0.125
    }

    const fn default_studio_bevel_width_px() -> f32 {
        3.0
    }

    const fn default_studio_bevel_color() -> [u8; 3] {
        [255, 255, 255]
    }

    const fn default_studio_texture_strength() -> f32 {
        1.0
    }

    const fn default_studio_warp_period_px() -> f32 {
        5.6
    }

    const fn default_studio_weft_period_px() -> f32 {
        5.2
    }

    const fn default_gradient_start() -> [u8; 3] {
        [20, 20, 28]
    }

    const fn default_gradient_end() -> [u8; 3] {
        [70, 70, 90]
    }

    const fn default_gradient_angle() -> f32 {
        0.0
    }

    fn default_vignette_colors() -> Vec<StudioMatColor> {
        vec![StudioMatColor::Rgb([241, 233, 210])]
    }

    const fn default_vignette_strength() -> f32 {
        0.6
    }

    const fn default_vignette_radius() -> f32 {
        0.75
    }

    const fn default_vignette_softness() -> f32 {
        0.5
    }

    const fn default_cinematic_darken() -> f32 {
        0.35
    }

    const fn default_cinematic_vignette_strength() -> f32 {
        0.5
    }

    fn default_drop_shadow_colors() -> Vec<StudioMatColor> {
        vec![StudioMatColor::Rgb([235, 235, 235])]
    }

    const fn default_drop_shadow_shadow_color() -> [u8; 3] {
        [0, 0, 0]
    }

    const fn default_drop_shadow_opacity() -> f32 {
        0.4
    }

    const fn default_drop_shadow_blur_px() -> f32 {
        24.0
    }

    const fn default_drop_shadow_offset_px() -> [i32; 2] {
        [0, 12]
    }
}

#[derive(Debug, Clone, Copy, PartialEq, Eq, PartialOrd, Ord)]
pub enum PhotoEffectKind {
    PrintSimulation,
}

impl PhotoEffectKind {
    const ALL: &'static [Self] = &[Self::PrintSimulation];
    const NAMES: &'static [&'static str] = &["print-simulation"];

    fn as_str(&self) -> &'static str {
        match self {
            Self::PrintSimulation => "print-simulation",
        }
    }
}

impl fmt::Display for PhotoEffectKind {
    fn fmt(&self, f: &mut fmt::Formatter<'_>) -> fmt::Result {
        f.write_str(self.as_str())
    }
}

impl<'de> Deserialize<'de> for PhotoEffectKind {
    fn deserialize<D>(deserializer: D) -> Result<Self, D::Error>
    where
        D: Deserializer<'de>,
    {
        let raw = String::deserialize(deserializer)?;
        for kind in Self::ALL {
            if raw == kind.as_str() {
                return Ok(*kind);
            }
        }
        Err(de::Error::unknown_variant(&raw, Self::NAMES))
    }
}

#[derive(Debug, Clone, Deserialize)]
#[serde(rename_all = "kebab-case")]
pub struct PrintSimulationOptions {
    #[serde(
        default = "PrintSimulationOptions::default_light_angle_degrees",
        rename = "light-angle-degrees"
    )]
    pub light_angle_degrees: f32,
    #[serde(
        default = "PrintSimulationOptions::default_relief_strength",
        rename = "relief-strength"
    )]
    pub relief_strength: f32,
    #[serde(
        default = "PrintSimulationOptions::default_ink_spread",
        rename = "ink-spread"
    )]
    pub ink_spread: f32,
    #[serde(
        default = "PrintSimulationOptions::default_sheen_strength",
        rename = "sheen-strength"
    )]
    pub sheen_strength: f32,
    #[serde(
        default = "PrintSimulationOptions::default_paper_color",
        rename = "paper-color"
    )]
    pub paper_color: [u8; 3],
    #[serde(default)]
    pub debug: bool,
}

impl PrintSimulationOptions {
    const fn default_light_angle_degrees() -> f32 {
        135.0
    }

    const fn default_relief_strength() -> f32 {
        0.35
    }

    const fn default_ink_spread() -> f32 {
        0.18
    }

    const fn default_sheen_strength() -> f32 {
        0.22
    }

    const fn default_paper_color() -> [u8; 3] {
        [245, 244, 240]
    }

    pub fn validate(&self) -> Result<()> {
        ensure!(
            self.relief_strength.is_finite() && self.relief_strength >= 0.0,
            "photo-effect.print-simulation.relief-strength must be non-negative"
        );
        ensure!(
            self.ink_spread.is_finite() && self.ink_spread >= 0.0,
            "photo-effect.print-simulation.ink-spread must be non-negative"
        );
        ensure!(
            self.sheen_strength.is_finite() && self.sheen_strength >= 0.0,
            "photo-effect.print-simulation.sheen-strength must be non-negative"
        );
        ensure!(
            self.light_angle_degrees.is_finite(),
            "photo-effect.print-simulation.light-angle-degrees must be a finite value"
        );
        Ok(())
    }
}

impl Default for PrintSimulationOptions {
    fn default() -> Self {
        Self {
            light_angle_degrees: Self::default_light_angle_degrees(),
            relief_strength: Self::default_relief_strength(),
            ink_spread: Self::default_ink_spread(),
            sheen_strength: Self::default_sheen_strength(),
            paper_color: Self::default_paper_color(),
            debug: false,
        }
    }
}

#[derive(Debug, Clone)]
pub enum PhotoEffectOptions {
    PrintSimulation(PrintSimulationOptions),
}

impl PhotoEffectOptions {
    pub fn kind(&self) -> PhotoEffectKind {
        match self {
            Self::PrintSimulation(_) => PhotoEffectKind::PrintSimulation,
        }
    }

    pub fn validate(&self) -> Result<()> {
        match self {
            PhotoEffectOptions::PrintSimulation(options) => options
                .validate()
                .context("invalid print-simulation options"),
        }
    }
}

#[derive(Debug, Clone)]
pub enum PhotoEffectSelection {
    Disabled,
    Fixed(SelectionEntry<PhotoEffectKind>),
    Random(Arc<[SelectionEntry<PhotoEffectKind>]>),
    Sequential {
        entries: Arc<[SelectionEntry<PhotoEffectKind>]>,
        runtime: SequentialState,
    },
}

impl PartialEq for PhotoEffectSelection {
    fn eq(&self, other: &Self) -> bool {
        match (self, other) {
            (PhotoEffectSelection::Disabled, PhotoEffectSelection::Disabled) => true,
            (PhotoEffectSelection::Fixed(a), PhotoEffectSelection::Fixed(b)) => a == b,
            (PhotoEffectSelection::Random(a), PhotoEffectSelection::Random(b)) => {
                a.as_ref() == b.as_ref()
            }
            (
                PhotoEffectSelection::Sequential { entries: a, .. },
                PhotoEffectSelection::Sequential { entries: b, .. },
            ) => a.as_ref() == b.as_ref(),
            _ => false,
        }
    }
}

impl Eq for PhotoEffectSelection {}

#[derive(Debug, Clone)]
pub struct PhotoEffectConfig {
    selection: PhotoEffectSelection,
    options: Vec<PhotoEffectOptions>,
}

impl Default for PhotoEffectConfig {
    fn default() -> Self {
        Self {
            selection: PhotoEffectSelection::Disabled,
            options: Vec::new(),
        }
    }
}

impl PhotoEffectConfig {
    pub fn is_enabled(&self) -> bool {
        !matches!(self.selection, PhotoEffectSelection::Disabled)
    }

    pub fn choose_option<R: Rng + ?Sized>(&self, rng: &mut R) -> Option<PhotoEffectOptions> {
        match &self.selection {
            PhotoEffectSelection::Disabled => None,
            PhotoEffectSelection::Fixed(entry) => self.option_for_entry(*entry).cloned(),
            PhotoEffectSelection::Random(entries) => entries
                .iter()
                .copied()
                .choose(rng)
                .and_then(|entry| self.option_for_entry(entry).cloned()),
            PhotoEffectSelection::Sequential { entries, runtime } => {
                if entries.is_empty() {
                    None
                } else {
                    let index = runtime.next(entries.len());
                    let entry = entries[index];
                    self.option_for_entry(entry).cloned()
                }
            }
        }
    }

    pub fn prepare_runtime(&mut self) -> Result<()> {
        match &self.selection {
            PhotoEffectSelection::Disabled => return Ok(()),
            PhotoEffectSelection::Fixed(entry) => {
                ensure!(
                    self.option_for_entry(*entry).is_some(),
                    "photo-effect.active entry {} must define options for {}",
                    entry.index,
                    entry.kind,
                );
            }
            PhotoEffectSelection::Random(entries)
            | PhotoEffectSelection::Sequential { entries, .. } => {
                ensure!(
                    !entries.is_empty(),
                    "photo-effect configuration must include at least one active entry",
                );
                for entry in entries.iter() {
                    ensure!(
                        self.option_for_entry(*entry).is_some(),
                        "photo-effect.active entry {} must define options for {}",
                        entry.index,
                        entry.kind,
                    );
                }
            }
        }

        for option in &self.options {
            option.validate()?;
        }

        Ok(())
    }

    fn option_for_entry(
        &self,
        entry: SelectionEntry<PhotoEffectKind>,
    ) -> Option<&PhotoEffectOptions> {
        self.options
            .get(entry.index)
            .filter(|option| option.kind() == entry.kind)
    }
}

impl<'de> Deserialize<'de> for PhotoEffectConfig {
    fn deserialize<D>(deserializer: D) -> Result<Self, D::Error>
    where
        D: Deserializer<'de>,
    {
        deserializer.deserialize_map(PhotoEffectConfigVisitor)
    }
}

struct PhotoEffectConfigVisitor;

impl<'de> Visitor<'de> for PhotoEffectConfigVisitor {
    type Value = PhotoEffectConfig;

    fn expecting(&self, formatter: &mut fmt::Formatter) -> fmt::Result {
        formatter.write_str("a photo effect configuration map")
    }

    fn visit_map<A>(self, mut map: A) -> Result<Self::Value, A::Error>
    where
        A: MapAccess<'de>,
    {
        let mut selection: Option<PipelineSelection> = None;
        let mut active: Option<Vec<PipelineEntry<PhotoEffectKind>>> = None;

        while let Some(key) = map.next_key::<String>()? {
            match key.as_str() {
                "selection" => {
                    if selection.is_some() {
                        return Err(de::Error::duplicate_field("selection"));
                    }
                    selection = Some(map.next_value()?);
                }
                "active" => {
                    if active.is_some() {
                        return Err(de::Error::duplicate_field("active"));
                    }
                    active = Some(map.next_value()?);
                }
                other => {
                    return Err(de::Error::unknown_field(other, &["selection", "active"]));
                }
            }
        }

        let active_entries = active.unwrap_or_default();
        if active_entries.is_empty() {
            return Ok(PhotoEffectConfig {
                selection: PhotoEffectSelection::Disabled,
                options: Vec::new(),
            });
        }

        let mut options = Vec::new();
        let mut entries = Vec::with_capacity(active_entries.len());
        for entry in active_entries.into_iter() {
            let kind = entry.kind;
            let option = build_photo_effect_option::<A::Error>(kind, entry.fields)?;
            let canonical_index = options.len();
            options.push(option);
            entries.push(SelectionEntry {
                index: canonical_index,
                kind,
            });
        }

        let resolved_selection =
            resolve_pipeline_selection::<A::Error>(selection, options.len(), "photo-effect")?;

        let entries: Arc<[SelectionEntry<PhotoEffectKind>]> = entries.into();

        let selection = match resolved_selection {
            PipelineSelection::Fixed => PhotoEffectSelection::Fixed(entries[0]),
            PipelineSelection::Random => PhotoEffectSelection::Random(entries.clone()),
            PipelineSelection::Sequential => PhotoEffectSelection::Sequential {
                entries: entries.clone(),
                runtime: SequentialState::default(),
            },
        };

        Ok(PhotoEffectConfig { selection, options })
    }
}

fn build_photo_effect_option<E>(
    kind: PhotoEffectKind,
    fields: Vec<(String, YamlValue)>,
) -> Result<PhotoEffectOptions, E>
where
    E: de::Error,
{
    let mut mapping = Mapping::new();
    for (field, value) in fields {
        let key = YamlValue::String(field.clone());
        if mapping.insert(key, value).is_some() {
            return Err(de::Error::custom(format!(
                "duplicate photo-effect field {}",
                field
            )));
        }
    }

    let value = YamlValue::Mapping(mapping);
    match kind {
        PhotoEffectKind::PrintSimulation => {
            let options = inline_value_to::<PrintSimulationOptions, E>(value)?;
            Ok(PhotoEffectOptions::PrintSimulation(options))
        }
    }
}

#[derive(Debug, Clone)]
pub enum TransitionSelection {
    Fixed(SelectionEntry<TransitionKind>),
    Random(Arc<[SelectionEntry<TransitionKind>]>),
    Sequential {
        entries: Arc<[SelectionEntry<TransitionKind>]>,
        runtime: SequentialState,
    },
}

pub type SelectedTransition<'a> = SelectedOption<'a, TransitionKind, TransitionOptions>;

impl PartialEq for TransitionSelection {
    fn eq(&self, other: &Self) -> bool {
        match (self, other) {
            (TransitionSelection::Fixed(a), TransitionSelection::Fixed(b)) => a == b,
            (TransitionSelection::Random(a), TransitionSelection::Random(b)) => {
                a.as_ref() == b.as_ref()
            }
            (
                TransitionSelection::Sequential { entries: a, .. },
                TransitionSelection::Sequential { entries: b, .. },
            ) => a.as_ref() == b.as_ref(),
            _ => false,
        }
    }
}

impl Eq for TransitionSelection {}

#[derive(Debug, Clone, Copy, PartialEq, Eq, PartialOrd, Ord)]
pub enum TransitionKind {
    Fade,
    Wipe,
    Push,
    EInk,
    Dissolve,
    RadialWipe,
    VenetianBlinds,
    CrossfadeZoom,
    Iris,
}

impl TransitionKind {
    const ALL: &'static [Self] = &[
        Self::Fade,
        Self::Wipe,
        Self::Push,
        Self::EInk,
        Self::Dissolve,
        Self::RadialWipe,
        Self::VenetianBlinds,
        Self::CrossfadeZoom,
        Self::Iris,
    ];
    const NAMES: &'static [&'static str] = &[
        "fade",
        "wipe",
        "push",
        "e-ink",
        "dissolve",
        "radial-wipe",
        "venetian-blinds",
        "crossfade-zoom",
        "iris",
    ];

    fn as_str(&self) -> &'static str {
        match self {
            Self::Fade => "fade",
            Self::Wipe => "wipe",
            Self::Push => "push",
            Self::EInk => "e-ink",
            Self::Dissolve => "dissolve",
            Self::RadialWipe => "radial-wipe",
            Self::VenetianBlinds => "venetian-blinds",
            Self::CrossfadeZoom => "crossfade-zoom",
            Self::Iris => "iris",
        }
    }

    pub const fn as_index(&self) -> u32 {
        match self {
            Self::Fade => 1,
            Self::Wipe => 2,
            Self::Push => 3,
            Self::EInk => 4,
            Self::Dissolve => 5,
            // 7 was the old SVG-path iris (removed); leaving the gap is fine —
            // indices only need to match the shader `case` integers, which need
            // not be contiguous.
            Self::RadialWipe => 8,
            Self::VenetianBlinds => 9,
            Self::CrossfadeZoom => 10,
            Self::Iris => 11,
        }
    }
}

impl fmt::Display for TransitionKind {
    fn fmt(&self, f: &mut fmt::Formatter<'_>) -> fmt::Result {
        f.write_str(self.as_str())
    }
}

impl<'de> Deserialize<'de> for TransitionKind {
    fn deserialize<D>(deserializer: D) -> Result<Self, D::Error>
    where
        D: Deserializer<'de>,
    {
        let raw = String::deserialize(deserializer)?;
        for kind in Self::ALL {
            if raw == kind.as_str() {
                return Ok(*kind);
            }
        }
        Err(de::Error::unknown_variant(&raw, Self::NAMES))
    }
}

#[derive(Debug, Clone)]
pub struct TransitionConfig {
    selection: TransitionSelection,
    options: Vec<TransitionOptions>,
}

impl Default for TransitionConfig {
    fn default() -> Self {
        let options = vec![TransitionOptions::default_for(TransitionKind::Fade)];
        Self {
            selection: TransitionSelection::Fixed(SelectionEntry {
                index: 0,
                kind: TransitionKind::Fade,
            }),
            options,
        }
    }
}

impl TransitionConfig {
    pub fn selection(&self) -> &TransitionSelection {
        &self.selection
    }

    #[allow(dead_code)]
    pub fn options(&self) -> &[TransitionOptions] {
        &self.options
    }

    fn selection_entries(&self) -> SelectionEntries<'_, TransitionKind> {
        match self.selection() {
            TransitionSelection::Fixed(entry) => SelectionEntries::single(*entry),
            TransitionSelection::Random(entries) => SelectionEntries::from_slice(entries.as_ref()),
            TransitionSelection::Sequential { entries, .. } => {
                SelectionEntries::from_slice(entries.as_ref())
            }
        }
    }

    pub fn iter_selected(&self) -> impl Iterator<Item = SelectedTransition<'_>> {
        SelectedIter::new(self.selection_entries(), self.options.as_slice())
    }

    pub fn primary_selected(&self) -> Option<SelectedTransition<'_>> {
        self.iter_selected().next()
    }

    #[allow(dead_code)]
    pub fn selected_by_index(&self, index: usize) -> Option<SelectedTransition<'_>> {
        self.iter_selected()
            .find(|selected| selected.entry.index == index)
    }

    pub fn select_active<R: Rng + ?Sized>(&self, rng: &mut R) -> SelectedTransition<'_> {
        let entry = match self.selection() {
            TransitionSelection::Fixed(entry) => *entry,
            TransitionSelection::Random(entries) => *entries
                .iter()
                .choose(rng)
                .expect("validated random transition should have options"),
            TransitionSelection::Sequential { entries, runtime } => {
                let index = runtime.next(entries.len());
                entries[index]
            }
        };

        let option = self
            .options
            .get(entry.index)
            .expect("validated transition selection should resolve to an option");
        SelectedOption { entry, option }
    }

    #[allow(dead_code)]
    pub fn primary_option(&self) -> Option<&TransitionOptions> {
        self.primary_selected().map(|selected| selected.option)
    }

    #[allow(dead_code)]
    pub fn choose_option<R: Rng + ?Sized>(&self, rng: &mut R) -> TransitionOptions {
        self.select_active(rng).option.clone()
    }

    /// Build a sequential `TransitionConfig` from a list of options.
    /// Used by showcase mode to replace the author-supplied transition list.
    pub(crate) fn sequential_from(options: Vec<TransitionOptions>) -> Self {
        let entries: Arc<[SelectionEntry<TransitionKind>]> = options
            .iter()
            .enumerate()
            .map(|(index, opt)| SelectionEntry {
                index,
                kind: opt.kind(),
            })
            .collect::<Vec<_>>()
            .into();
        Self {
            selection: TransitionSelection::Sequential {
                entries,
                runtime: SequentialState::default(),
            },
            options,
        }
    }

    pub fn validate(&mut self) -> Result<()> {
        ensure!(
            !self.options.is_empty(),
            "transition configuration must include at least one active entry"
        );
        for option in self.options.iter_mut() {
            option.normalize()?;
        }
        let validate_entry = |entry: SelectionEntry<TransitionKind>| -> Result<()> {
            let option = self.options.get(entry.index).with_context(|| {
                format!(
                    "transition.active entry {} references index {} which is out of bounds",
                    entry.kind, entry.index
                )
            })?;
            ensure!(
                option.kind == entry.kind,
                "transition.active entry {} at index {} must resolve to a matching option",
                entry.kind,
                entry.index
            );
            Ok(())
        };
        match &self.selection {
            TransitionSelection::Fixed(entry) => validate_entry(*entry)?,
            TransitionSelection::Random(entries)
            | TransitionSelection::Sequential { entries, .. } => {
                for entry in entries.iter() {
                    validate_entry(*entry)?;
                }
            }
        }
        Ok(())
    }
}

#[derive(Debug, Clone)]
pub struct TransitionOptions {
    kind: TransitionKind,
    duration_ms: u64,
    mode: TransitionMode,
}

impl TransitionOptions {
    fn default_for(kind: TransitionKind) -> Self {
        let (duration_ms, mode) = match kind {
            TransitionKind::Fade => (400, TransitionMode::Fade(FadeTransition::default())),
            TransitionKind::Wipe => (400, TransitionMode::Wipe(WipeTransition::default())),
            TransitionKind::Push => (400, TransitionMode::Push(PushTransition::default())),
            TransitionKind::EInk => (1600, TransitionMode::EInk(EInkTransition::default())),
            TransitionKind::Dissolve => {
                (600, TransitionMode::Dissolve(DissolveTransition::default()))
            }
            TransitionKind::RadialWipe => (
                500,
                TransitionMode::RadialWipe(RadialWipeTransition::default()),
            ),
            TransitionKind::VenetianBlinds => (
                600,
                TransitionMode::VenetianBlinds(VenetianBlindsTransition::default()),
            ),
            TransitionKind::CrossfadeZoom => (
                700,
                TransitionMode::CrossfadeZoom(CrossfadeZoomTransition::default()),
            ),
            TransitionKind::Iris => (2600, TransitionMode::Iris(IrisTransition::default())),
        };
        Self {
            kind,
            duration_ms,
            mode,
        }
    }

    pub fn kind(&self) -> TransitionKind {
        self.kind
    }

    pub fn duration(&self) -> Duration {
        Duration::from_millis(self.duration_ms.max(1))
    }

    pub fn mode(&self) -> &TransitionMode {
        &self.mode
    }

    fn normalize(&mut self) -> Result<()> {
        ensure!(
            self.duration_ms > 0,
            format!("transition option {} must set duration-ms > 0", self.kind)
        );
        match &mut self.mode {
            TransitionMode::Fade(_) => {}
            TransitionMode::Wipe(wipe) => {
                if !wipe.softness.is_finite() {
                    return Err(anyhow::anyhow!(
                        "transition option {} has non-finite wipe.softness",
                        self.kind
                    ));
                }
                wipe.softness = wipe.softness.clamp(0.0, 0.5);
                wipe.angles.normalize(self.kind)?;
            }
            TransitionMode::Push(push) => {
                push.angles.normalize(self.kind)?;
            }
            TransitionMode::EInk(eink) => {
                if !eink.reveal_portion.is_finite() {
                    return Err(anyhow::anyhow!(
                        "transition option {} has non-finite e-ink.reveal-portion",
                        self.kind
                    ));
                }
                eink.reveal_portion = eink.reveal_portion.clamp(0.05, 0.95);
                if eink.stripe_count == 0 {
                    eink.stripe_count = 1;
                }
                eink.flash_count = eink.flash_count.min(6);
            }
            TransitionMode::Dissolve(d) => {
                d.softness = d.softness.clamp(0.0, 0.5);
                if !d.scale.is_finite() || d.scale <= 0.0 {
                    d.scale = 64.0;
                }
            }
            TransitionMode::RadialWipe(rw) => {
                rw.softness = rw.softness.clamp(0.0, 0.5);
                if !rw.center[0].is_finite() || !rw.center[1].is_finite() {
                    rw.center = [0.5, 0.5];
                }
            }
            TransitionMode::VenetianBlinds(vb) => {
                if vb.stripe_count == 0 {
                    vb.stripe_count = 1;
                }
                vb.softness = vb.softness.clamp(0.0, 0.5);
            }
            TransitionMode::CrossfadeZoom(cz) => {
                if !cz.zoom.is_finite() {
                    cz.zoom = 0.06;
                }
                cz.zoom = cz.zoom.clamp(0.0, 0.5);
            }
            TransitionMode::Iris(iris) => {
                iris.sanitize();
            }
        }
        Ok(())
    }

    fn with_kind(kind: TransitionKind, builder: TransitionOptionBuilder) -> Result<Self> {
        let duration_ms = builder
            .duration_ms
            .unwrap_or_else(|| TransitionOptions::default_for(kind).duration_ms);
        let mode = match kind {
            TransitionKind::Fade => TransitionMode::Fade(FadeTransition {
                through_black: builder.fade_through_black.unwrap_or(false),
            }),
            TransitionKind::Wipe => {
                if let Some(angles) = builder
                    .wipe_angle_list_deg
                    .as_ref()
                    .filter(|angles| angles.len() > 1)
                {
                    return Err(anyhow::anyhow!(
                        "transition option {} expected canonicalized angle entries, got {} entries",
                        kind,
                        angles.len()
                    ));
                }
                let base = builder
                    .wipe_angle_list_deg
                    .as_ref()
                    .and_then(|angles| angles.first().copied())
                    .unwrap_or(0.0);
                let jitter = builder.wipe_angle_jitter_deg.unwrap_or(0.0);
                TransitionMode::Wipe(WipeTransition {
                    angles: AnglePicker::new(base, jitter),
                    softness: builder.wipe_softness.unwrap_or(0.05),
                })
            }
            TransitionKind::Push => {
                if let Some(angles) = builder
                    .push_angle_list_deg
                    .as_ref()
                    .filter(|angles| angles.len() > 1)
                {
                    return Err(anyhow::anyhow!(
                        "transition option {} expected canonicalized angle entries, got {} entries",
                        kind,
                        angles.len()
                    ));
                }
                let base = builder
                    .push_angle_list_deg
                    .as_ref()
                    .and_then(|angles| angles.first().copied())
                    .unwrap_or(0.0);
                let jitter = builder.push_angle_jitter_deg.unwrap_or(0.0);
                TransitionMode::Push(PushTransition {
                    angles: AnglePicker::new(base, jitter),
                })
            }
            TransitionKind::EInk => {
                let defaults = EInkTransition::default();
                TransitionMode::EInk(EInkTransition {
                    flash_count: builder.eink_flash_count.unwrap_or(defaults.flash_count),
                    reveal_portion: builder
                        .eink_reveal_portion
                        .unwrap_or(defaults.reveal_portion),
                    stripe_count: builder.eink_stripe_count.unwrap_or(defaults.stripe_count),
                    flash_color: builder.eink_flash_color.unwrap_or(defaults.flash_color),
                })
            }
            TransitionKind::Dissolve => {
                let defaults = DissolveTransition::default();
                let mut d = DissolveTransition {
                    softness: builder.dissolve_softness.unwrap_or(defaults.softness),
                    scale: builder.dissolve_scale.unwrap_or(defaults.scale),
                };
                d.softness = d.softness.clamp(0.0, 0.5);
                if !d.scale.is_finite() || d.scale <= 0.0 {
                    d.scale = 64.0;
                }
                TransitionMode::Dissolve(d)
            }
            TransitionKind::RadialWipe => {
                let defaults = RadialWipeTransition::default();
                let mut rw = RadialWipeTransition {
                    softness: builder.radial_wipe_softness.unwrap_or(defaults.softness),
                    shape: builder
                        .radial_wipe_shapes
                        .as_ref()
                        .and_then(|s| s.first().copied())
                        .unwrap_or(defaults.shape),
                    center: builder.radial_wipe_center.unwrap_or(defaults.center),
                };
                rw.softness = rw.softness.clamp(0.0, 0.5);
                if !rw.center[0].is_finite() || !rw.center[1].is_finite() {
                    rw.center = [0.5, 0.5];
                }
                TransitionMode::RadialWipe(rw)
            }
            TransitionKind::VenetianBlinds => {
                let defaults = VenetianBlindsTransition::default();
                let mut vb = VenetianBlindsTransition {
                    stripe_count: builder
                        .venetian_stripe_count
                        .unwrap_or(defaults.stripe_count)
                        .max(1),
                    softness: builder.venetian_softness.unwrap_or(defaults.softness),
                    vertical: builder
                        .venetian_orientations
                        .as_ref()
                        .and_then(|o| o.first().copied())
                        .unwrap_or(defaults.vertical),
                };
                vb.softness = vb.softness.clamp(0.0, 0.5);
                TransitionMode::VenetianBlinds(vb)
            }
            TransitionKind::CrossfadeZoom => {
                let defaults = CrossfadeZoomTransition::default();
                let mut cz = CrossfadeZoomTransition {
                    zoom: builder.crossfade_zoom.unwrap_or(defaults.zoom),
                    current_zooms_in: builder
                        .crossfade_current_zooms_in
                        .unwrap_or(defaults.current_zooms_in),
                    next_zooms_in: builder
                        .crossfade_next_zooms_in
                        .unwrap_or(defaults.next_zooms_in),
                };
                if !cz.zoom.is_finite() {
                    cz.zoom = 0.06;
                }
                cz.zoom = cz.zoom.clamp(0.0, 0.5);
                TransitionMode::CrossfadeZoom(cz)
            }
            TransitionKind::Iris => {
                let defaults = IrisTransition::default();
                let mut iris = IrisTransition {
                    blades: builder.iris_blades.unwrap_or(defaults.blades),
                    color: builder.iris_color.unwrap_or(defaults.color),
                    petal_sheen: builder.iris_petal_sheen.unwrap_or(defaults.petal_sheen),
                    overlap_shadow: builder
                        .iris_overlap_shadow
                        .unwrap_or(defaults.overlap_shadow),
                    min_aperture: builder.iris_min_aperture.unwrap_or(defaults.min_aperture),
                    swirl: builder.iris_swirl.unwrap_or(defaults.swirl),
                };
                iris.sanitize();
                TransitionMode::Iris(iris)
            }
        };
        let mut option = Self {
            kind,
            duration_ms,
            mode,
        };

        match &mut option.mode {
            TransitionMode::Fade(_) => {}
            TransitionMode::Wipe(cfg) => {
                cfg.angles.normalize(kind)?;
            }
            TransitionMode::Push(cfg) => {
                cfg.angles.normalize(kind)?;
            }
            TransitionMode::EInk(eink) => {
                if !eink.reveal_portion.is_finite() {
                    return Err(anyhow::anyhow!(
                        "transition option {} has non-finite e-ink.reveal-portion",
                        kind
                    ));
                }
                eink.reveal_portion = eink.reveal_portion.clamp(0.05, 0.95);
                if eink.stripe_count == 0 {
                    eink.stripe_count = 1;
                }
                eink.flash_count = eink.flash_count.min(6);
            }
            TransitionMode::Dissolve(_)
            | TransitionMode::RadialWipe(_)
            | TransitionMode::VenetianBlinds(_)
            | TransitionMode::CrossfadeZoom(_)
            | TransitionMode::Iris(_) => {}
        }

        Ok(option)
    }
}

#[derive(Debug, Clone)]
pub enum TransitionMode {
    Fade(FadeTransition),
    Wipe(WipeTransition),
    Push(PushTransition),
    EInk(EInkTransition),
    Dissolve(DissolveTransition),
    RadialWipe(RadialWipeTransition),
    VenetianBlinds(VenetianBlindsTransition),
    CrossfadeZoom(CrossfadeZoomTransition),
    Iris(IrisTransition),
}

#[derive(Debug, Clone, Copy)]
pub struct AnglePicker {
    pub base_deg: f32,
    pub jitter_deg: f32,
}

impl Default for AnglePicker {
    fn default() -> Self {
        Self {
            base_deg: 0.0_f32,
            jitter_deg: 0.0,
        }
    }
}

impl AnglePicker {
    fn new(base_deg: f32, jitter_deg: f32) -> Self {
        Self {
            base_deg,
            jitter_deg,
        }
    }

    fn normalize(&mut self, kind: TransitionKind) -> Result<()> {
        ensure!(
            self.base_deg.is_finite(),
            format!("transition option {} has non-finite values in angles", kind)
        );
        ensure!(
            self.jitter_deg.is_finite(),
            format!("transition option {} has non-finite angle-jitter", kind)
        );
        ensure!(
            self.jitter_deg >= 0.0,
            format!("transition option {} requires angle-jitter >= 0", kind)
        );
        Ok(())
    }
}

#[derive(Debug, Clone, Copy, Default)]
pub struct FadeTransition {
    pub through_black: bool,
}

#[derive(Debug, Clone)]
pub struct WipeTransition {
    pub angles: AnglePicker,
    pub softness: f32,
}

impl Default for WipeTransition {
    fn default() -> Self {
        Self {
            angles: AnglePicker::default(),
            softness: 0.05,
        }
    }
}

#[derive(Debug, Clone, Default)]
pub struct PushTransition {
    pub angles: AnglePicker,
}

#[derive(Debug, Clone, Copy)]
pub struct EInkTransition {
    pub flash_count: u32,
    pub reveal_portion: f32,
    pub stripe_count: u32,
    pub flash_color: [u8; 3],
}

impl Default for EInkTransition {
    fn default() -> Self {
        Self {
            flash_count: 0,
            reveal_portion: 0.55,
            stripe_count: 24,
            flash_color: [255, 255, 255],
        }
    }
}

#[derive(Debug, Clone, Copy)]
pub struct DissolveTransition {
    pub softness: f32,
    pub scale: f32,
}

impl Default for DissolveTransition {
    fn default() -> Self {
        Self {
            softness: 0.1,
            scale: 64.0,
        }
    }
}

#[derive(Debug, Clone, Copy, PartialEq, Eq, Deserialize)]
#[serde(rename_all = "kebab-case")]
pub enum RadialShape {
    Circle,
    Diamond,
}

impl Default for RadialShape {
    fn default() -> Self {
        Self::Circle
    }
}

#[derive(Debug, Clone, Copy)]
pub struct RadialWipeTransition {
    pub softness: f32,
    pub shape: RadialShape,
    pub center: [f32; 2],
}

impl Default for RadialWipeTransition {
    fn default() -> Self {
        Self {
            softness: 0.1,
            shape: RadialShape::Circle,
            center: [0.5, 0.5],
        }
    }
}

#[derive(Debug, Clone, Copy)]
pub struct VenetianBlindsTransition {
    pub stripe_count: u32,
    pub softness: f32,
    pub vertical: bool,
}

impl Default for VenetianBlindsTransition {
    fn default() -> Self {
        Self {
            stripe_count: 16,
            softness: 0.1,
            vertical: false,
        }
    }
}

#[derive(Debug, Clone, Copy)]
pub struct CrossfadeZoomTransition {
    pub zoom: f32,
    pub current_zooms_in: bool,
    pub next_zooms_in: bool,
}

impl Default for CrossfadeZoomTransition {
    fn default() -> Self {
        Self {
            zoom: 0.06,
            current_zooms_in: true,
            next_zooms_in: true,
        }
    }
}

/// Mechanical camera-iris transition: N annular petals (rounded ends, pivoting
/// at one end cap like a paper iris diaphragm) close over the current photo and
/// reopen on the next. Petal geometry (radii, width, swing) is derived from the
/// screen size and blade count; only look-related knobs are exposed.
#[derive(Debug, Clone, Copy)]
pub struct IrisTransition {
    pub blades: u32,
    pub color: [u8; 3],
    pub petal_sheen: f32,
    pub overlap_shadow: f32,
    pub min_aperture: f32,
    pub swirl: f32,
}

impl Default for IrisTransition {
    fn default() -> Self {
        Self {
            blades: 9,
            color: [42, 42, 49],
            petal_sheen: 0.45,
            overlap_shadow: 0.6,
            min_aperture: 0.05,
            swirl: -0.45,
        }
    }
}

impl IrisTransition {
    fn sanitize(&mut self) {
        let defaults = Self::default();
        // The auto-derived blade width (spacing + 75°) is validated for 5..=14
        // petals; outside that range full closure is not guaranteed.
        self.blades = self.blades.clamp(5, 14);
        if !self.petal_sheen.is_finite() {
            self.petal_sheen = defaults.petal_sheen;
        }
        self.petal_sheen = self.petal_sheen.clamp(0.0, 1.0);
        if !self.overlap_shadow.is_finite() {
            self.overlap_shadow = defaults.overlap_shadow;
        }
        self.overlap_shadow = self.overlap_shadow.clamp(0.0, 1.0);
        if !self.min_aperture.is_finite() {
            self.min_aperture = defaults.min_aperture;
        }
        self.min_aperture = self.min_aperture.clamp(0.0, 0.4);
        if !self.swirl.is_finite() {
            self.swirl = defaults.swirl;
        }
        self.swirl = self.swirl.clamp(-1.0, 1.0);
    }
}

impl<'de> Deserialize<'de> for TransitionConfig {
    fn deserialize<D>(deserializer: D) -> Result<Self, D::Error>
    where
        D: Deserializer<'de>,
    {
        deserializer.deserialize_map(TransitionConfigVisitor)
    }
}

struct TransitionConfigVisitor;

impl<'de> Visitor<'de> for TransitionConfigVisitor {
    type Value = TransitionConfig;

    fn expecting(&self, formatter: &mut fmt::Formatter) -> fmt::Result {
        formatter.write_str("a transition configuration map")
    }

    fn visit_map<A>(self, mut map: A) -> Result<Self::Value, A::Error>
    where
        A: MapAccess<'de>,
    {
        let mut selection: Option<PipelineSelection> = None;
        let mut active: Option<Vec<PipelineEntry<TransitionKind>>> = None;
        while let Some(key) = map.next_key::<String>()? {
            match key.as_str() {
                "selection" => {
                    if selection.is_some() {
                        return Err(de::Error::duplicate_field("selection"));
                    }
                    selection = Some(map.next_value()?);
                }
                "active" => {
                    if active.is_some() {
                        return Err(de::Error::duplicate_field("active"));
                    }
                    active = Some(map.next_value()?);
                }
                _ => {
                    return Err(de::Error::unknown_field(
                        key.as_str(),
                        &["selection", "active"],
                    ));
                }
            }
        }

        let active_entries = active.ok_or_else(|| de::Error::missing_field("active"))?;

        let mut options = Vec::new();
        let mut entries = Vec::new();
        for entry in active_entries.into_iter() {
            let kind = entry.kind;
            let mut builder = TransitionOptionBuilder::default();
            for (field, value) in entry.fields {
                apply_transition_inline_field::<A::Error>(&mut builder, kind, &field, value)?;
            }
            let canonical = builder
                .into_canonical_options(kind)
                .map_err(|err| de::Error::custom(err.to_string()))?;
            for option in canonical {
                let index = options.len();
                options.push(option);
                entries.push(SelectionEntry { index, kind });
            }
        }

        let resolved_selection =
            resolve_pipeline_selection::<A::Error>(selection, options.len(), "transition")?;

        let entries: Arc<[SelectionEntry<TransitionKind>]> = entries.into();

        let selection = match resolved_selection {
            PipelineSelection::Fixed => TransitionSelection::Fixed(entries[0]),
            PipelineSelection::Random => TransitionSelection::Random(entries.clone()),
            PipelineSelection::Sequential => TransitionSelection::Sequential {
                entries: entries.clone(),
                runtime: SequentialState::default(),
            },
        };

        Ok(TransitionConfig { selection, options })
    }
}

#[derive(Clone, Default)]
struct TransitionOptionBuilder {
    duration_ms: Option<u64>,
    fade_through_black: Option<bool>,
    wipe_angle_list_deg: Option<Vec<f32>>,
    wipe_angle_jitter_deg: Option<f32>,
    wipe_softness: Option<f32>,
    push_angle_list_deg: Option<Vec<f32>>,
    push_angle_jitter_deg: Option<f32>,
    eink_flash_count: Option<u32>,
    eink_reveal_portion: Option<f32>,
    eink_stripe_count: Option<u32>,
    eink_flash_color: Option<[u8; 3]>,
    dissolve_softness: Option<f32>,
    dissolve_scale: Option<f32>,
    radial_wipe_softness: Option<f32>,
    // One canonical slot per shape; `shape` (singular) or `shapes` (list).
    radial_wipe_shapes: Option<Vec<RadialShape>>,
    radial_wipe_center: Option<[f32; 2]>,
    venetian_stripe_count: Option<u32>,
    venetian_softness: Option<f32>,
    // One canonical slot per orientation (true = vertical); `orientation` or `orientations`.
    venetian_orientations: Option<Vec<bool>>,
    crossfade_zoom: Option<f32>,
    crossfade_current_zooms_in: Option<bool>,
    crossfade_next_zooms_in: Option<bool>,
    iris_blades: Option<u32>,
    iris_color: Option<[u8; 3]>,
    iris_petal_sheen: Option<f32>,
    iris_overlap_shadow: Option<f32>,
    iris_min_aperture: Option<f32>,
    iris_swirl: Option<f32>,
}

impl TransitionOptionBuilder {
    fn into_canonical_options(self, kind: TransitionKind) -> Result<Vec<TransitionOptions>> {
        match kind {
            TransitionKind::Wipe => {
                let angles = self.wipe_angle_list_deg.clone();
                let jitter = self.wipe_angle_jitter_deg;
                self.into_canonical_with_angles(kind, angles, jitter, |builder, base| {
                    builder.wipe_angle_list_deg = Some(vec![base])
                })
            }
            TransitionKind::Push => {
                let angles = self.push_angle_list_deg.clone();
                let jitter = self.push_angle_jitter_deg;
                self.into_canonical_with_angles(kind, angles, jitter, |builder, base| {
                    builder.push_angle_list_deg = Some(vec![base])
                })
            }
            TransitionKind::RadialWipe => {
                if let Some(shapes) = self.radial_wipe_shapes.clone()
                    && shapes.len() > 1
                {
                    let mut options = Vec::with_capacity(shapes.len());
                    for shape in shapes {
                        let mut builder = self.clone();
                        builder.radial_wipe_shapes = Some(vec![shape]);
                        options.push(TransitionOptions::with_kind(kind, builder)?);
                    }
                    return Ok(options);
                }
                Ok(vec![TransitionOptions::with_kind(kind, self)?])
            }
            TransitionKind::VenetianBlinds => {
                if let Some(orientations) = self.venetian_orientations.clone()
                    && orientations.len() > 1
                {
                    let mut options = Vec::with_capacity(orientations.len());
                    for vertical in orientations {
                        let mut builder = self.clone();
                        builder.venetian_orientations = Some(vec![vertical]);
                        options.push(TransitionOptions::with_kind(kind, builder)?);
                    }
                    return Ok(options);
                }
                Ok(vec![TransitionOptions::with_kind(kind, self)?])
            }
            _ => {
                let option = TransitionOptions::with_kind(kind, self)?;
                Ok(vec![option])
            }
        }
    }

    fn into_canonical_with_angles(
        self,
        kind: TransitionKind,
        angles: Option<Vec<f32>>,
        jitter: Option<f32>,
        mut apply_base: impl FnMut(&mut TransitionOptionBuilder, f32),
    ) -> Result<Vec<TransitionOptions>> {
        let jitter_value = jitter.unwrap_or(0.0);
        ensure!(
            jitter_value.is_finite(),
            format!("transition option {} has non-finite angle-jitter", kind)
        );
        ensure!(
            jitter_value >= 0.0,
            format!("transition option {} requires angle-jitter >= 0", kind)
        );
        let base_angles = angles.unwrap_or_else(|| vec![0.0]);
        ensure!(
            !base_angles.is_empty(),
            format!(
                "transition option {} requires angles to include at least one entry",
                kind
            )
        );
        let mut options = Vec::with_capacity(base_angles.len());
        let builder_template = self;
        for base in base_angles {
            ensure!(
                base.is_finite(),
                format!("transition option {} has non-finite values in angles", kind)
            );
            let mut builder = builder_template.clone();
            apply_base(&mut builder, base);
            let option = TransitionOptions::with_kind(kind, builder)?;
            options.push(option);
        }
        Ok(options)
    }
}

fn parse_orientation<E: de::Error>(value: String) -> Result<bool, E> {
    match value.as_str() {
        "vertical" => Ok(true),
        "horizontal" => Ok(false),
        other => Err(de::Error::unknown_variant(
            other,
            &["horizontal", "vertical"],
        )),
    }
}

fn apply_transition_inline_field<E: de::Error>(
    builder: &mut TransitionOptionBuilder,
    kind: TransitionKind,
    field: &str,
    value: YamlValue,
) -> Result<(), E> {
    match field {
        "duration-ms" => {
            builder.duration_ms = Some(inline_value_to::<u64, E>(value)?);
        }
        "through-black" if matches!(kind, TransitionKind::Fade) => {
            builder.fade_through_black = Some(inline_value_to::<bool, E>(value)?);
        }
        "angles" if matches!(kind, TransitionKind::Wipe | TransitionKind::Push) => {
            let angles = inline_value_to::<Vec<f32>, E>(value)?;
            match kind {
                TransitionKind::Wipe => builder.wipe_angle_list_deg = Some(angles),
                TransitionKind::Push => builder.push_angle_list_deg = Some(angles),
                _ => {}
            }
        }
        "angle-jitter" if matches!(kind, TransitionKind::Wipe | TransitionKind::Push) => {
            let jitter = inline_value_to::<f32, E>(value)?;
            match kind {
                TransitionKind::Wipe => builder.wipe_angle_jitter_deg = Some(jitter),
                TransitionKind::Push => builder.push_angle_jitter_deg = Some(jitter),
                _ => {}
            }
        }
        "softness"
            if matches!(
                kind,
                TransitionKind::Wipe
                    | TransitionKind::Dissolve
                    | TransitionKind::RadialWipe
                    | TransitionKind::VenetianBlinds
            ) =>
        {
            match kind {
                TransitionKind::Wipe => {
                    builder.wipe_softness = Some(inline_value_to::<f32, E>(value)?)
                }
                TransitionKind::Dissolve => {
                    builder.dissolve_softness = Some(inline_value_to::<f32, E>(value)?)
                }
                TransitionKind::RadialWipe => {
                    builder.radial_wipe_softness = Some(inline_value_to::<f32, E>(value)?)
                }
                TransitionKind::VenetianBlinds => {
                    builder.venetian_softness = Some(inline_value_to::<f32, E>(value)?)
                }
                _ => {}
            }
        }
        "flash-count" if matches!(kind, TransitionKind::EInk) => {
            builder.eink_flash_count = Some(inline_value_to::<u32, E>(value)?);
        }
        "reveal-portion" if matches!(kind, TransitionKind::EInk) => {
            builder.eink_reveal_portion = Some(inline_value_to::<f32, E>(value)?);
        }
        "stripe-count" if matches!(kind, TransitionKind::EInk | TransitionKind::VenetianBlinds) => {
            match kind {
                TransitionKind::EInk => {
                    builder.eink_stripe_count = Some(inline_value_to::<u32, E>(value)?)
                }
                TransitionKind::VenetianBlinds => {
                    builder.venetian_stripe_count = Some(inline_value_to::<u32, E>(value)?)
                }
                _ => {}
            }
        }
        "flash-color" if matches!(kind, TransitionKind::EInk) => {
            builder.eink_flash_color = Some(inline_value_to::<[u8; 3], E>(value)?);
        }
        "scale" if matches!(kind, TransitionKind::Dissolve) => {
            builder.dissolve_scale = Some(inline_value_to::<f32, E>(value)?);
        }
        "center" if matches!(kind, TransitionKind::RadialWipe) => {
            builder.radial_wipe_center = Some(inline_value_to::<[f32; 2], E>(value)?);
        }
        "shapes" if matches!(kind, TransitionKind::RadialWipe) => {
            builder.radial_wipe_shapes = Some(inline_value_to::<Vec<RadialShape>, E>(value)?);
        }
        "orientations" if matches!(kind, TransitionKind::VenetianBlinds) => {
            let raw = inline_value_to::<Vec<String>, E>(value)?;
            let mut out = Vec::with_capacity(raw.len());
            for s in raw {
                out.push(parse_orientation::<E>(s)?);
            }
            builder.venetian_orientations = Some(out);
        }
        "zoom" if matches!(kind, TransitionKind::CrossfadeZoom) => {
            builder.crossfade_zoom = Some(inline_value_to::<f32, E>(value)?);
        }
        "current-zooms-in" if matches!(kind, TransitionKind::CrossfadeZoom) => {
            builder.crossfade_current_zooms_in = Some(inline_value_to::<bool, E>(value)?);
        }
        "next-zooms-in" if matches!(kind, TransitionKind::CrossfadeZoom) => {
            builder.crossfade_next_zooms_in = Some(inline_value_to::<bool, E>(value)?);
        }
        "blades" if matches!(kind, TransitionKind::Iris) => {
            builder.iris_blades = Some(inline_value_to::<u32, E>(value)?);
        }
        "color" if matches!(kind, TransitionKind::Iris) => {
            builder.iris_color = Some(inline_value_to::<[u8; 3], E>(value)?);
        }
        "petal-sheen" if matches!(kind, TransitionKind::Iris) => {
            builder.iris_petal_sheen = Some(inline_value_to::<f32, E>(value)?);
        }
        "overlap-shadow" if matches!(kind, TransitionKind::Iris) => {
            builder.iris_overlap_shadow = Some(inline_value_to::<f32, E>(value)?);
        }
        "min-aperture" if matches!(kind, TransitionKind::Iris) => {
            builder.iris_min_aperture = Some(inline_value_to::<f32, E>(value)?);
        }
        "swirl" if matches!(kind, TransitionKind::Iris) => {
            builder.iris_swirl = Some(inline_value_to::<f32, E>(value)?);
        }
        _ => {
            return Err(de::Error::unknown_field(
                field,
                &[
                    "duration-ms",
                    "through-black",
                    "angles",
                    "angle-selection",
                    "angle-jitter",
                    "softness",
                    "flash-count",
                    "reveal-portion",
                    "stripe-count",
                    "flash-color",
                    "scale",
                    "center",
                    "shapes",
                    "orientations",
                    "zoom",
                    "current-zooms-in",
                    "next-zooms-in",
                    "blades",
                    "color",
                    "petal-sheen",
                    "overlap-shadow",
                    "min-aperture",
                    "swirl",
                ],
            ));
        }
    }
    Ok(())
}
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
