vincentl/rust-photo-frame/crates/photoframe/src/tasks/viewer.rs

mod image_ops;
pub mod scenes;

use self::image_ops::*;
use self::scenes::{GreetingScene, Scene, SceneContext, SleepScene};

use crate::config::{
    MattingConfig, MattingMode, MattingOptions, SelectedTransition, TransitionConfig,
    TransitionKind, TransitionMode,
};
use crate::events::{
    Displayed, PhotoLoaded, PreparedImageCpu, ViewerCommand, ViewerState as ControlViewerState,
};
use crate::processing::blur::apply_blur;
use crate::processing::color::average_color;
use crate::processing::layout::center_offset;
use crate::tasks::greeting_screen::GreetingScreen;
use crossbeam_channel::{Receiver as CbReceiver, Sender as CbSender, TrySendError, bounded};
use futures::executor::block_on;
use image::{Rgba, RgbaImage, imageops};
use rand::Rng;
use std::borrow::Cow;
use std::collections::VecDeque;
use std::sync::Arc;
use std::time::{Duration, Instant};
use tokio::sync::mpsc::{Receiver, Sender};
use tokio::time::{MissedTickBehavior, interval};
use tokio_util::sync::CancellationToken;
use tracing::{Level, debug, info, warn};

/// Iris petal angular width beyond the petal spacing (75°). Validated
/// numerically to keep the aperture boundary on the petals' inner arcs (no
/// end-cap "teeth") for 5..=14 blades at any minimum aperture.
const IRIS_EXTRA_WIDTH_RAD: f32 = 1.308_997;

/// Linear downscale factor of the iris petal layer relative to the surface.
/// 4 → 1/16 of the petal-shading cost; at 4K the layer is 960x540, and the
/// petal edge feather widens to ~4 native pixels, which reads as natural
/// blade softness. Override with PHOTOFRAME_IRIS_LAYER_SCALE for tuning.
const IRIS_LAYER_SCALE: u32 = 4;

/// Linear downscale factor for the intermediate that transition frames
/// render into (resting photos always render at native resolution). 2 →
/// roughly a quarter of the per-pixel transition cost; motion hides the
/// brief softness, and the first dwell frame restores full sharpness.
/// Override with PHOTOFRAME_TRANSITION_SCALE for tuning; 1 bypasses the
/// intermediate entirely and renders transitions at native resolution.
const TRANSITION_HALF_SCALE: u32 = 2;

fn scale_from_env(var: &str, default: u32, max: u32) -> u32 {
    match std::env::var(var) {
        Ok(raw) => match raw.parse::<u32>() {
            Ok(value) if (1..=max).contains(&value) => {
                info!(var, value, "viewer_scale_override");
                value
            }
            _ => {
                warn!(var, raw, "invalid scale override; using default");
                default
            }
        },
        Err(_) => default,
    }
}

/// Effective transition-intermediate scale (env-overridable, read once).
fn transition_scale() -> u32 {
    static SCALE: std::sync::OnceLock<u32> = std::sync::OnceLock::new();
    *SCALE.get_or_init(|| scale_from_env("PHOTOFRAME_TRANSITION_SCALE", TRANSITION_HALF_SCALE, 4))
}

/// Effective iris petal-layer scale (env-overridable, read once).
fn iris_layer_scale() -> u32 {
    static SCALE: std::sync::OnceLock<u32> = std::sync::OnceLock::new();
    *SCALE.get_or_init(|| scale_from_env("PHOTOFRAME_IRIS_LAYER_SCALE", IRIS_LAYER_SCALE, 8))
}

/// Past this (eased) progress the transition renders at native resolution
/// again, so the incoming photo settles into full sharpness instead of
/// popping when the first dwell frame lands.
const TRANSITION_FULL_RES_TAIL: f32 = 0.99;

pub(super) enum ActiveTransition {
    Fade {
        through_black: bool,
    },
    Wipe {
        normal: [f32; 2],
        softness: f32,
    },
    Push {
        direction: [f32; 2],
    },
    EInk {
        flash_count: u32,
        reveal_portion: f32,
        stripe_count: u32,
        flash_color: [f32; 3],
        noise_seed: [f32; 2],
    },
    Dissolve {
        softness: f32,
        scale: f32,
    },
    RadialWipe {
        softness: f32,
        shape_is_diamond: bool,
        center: [f32; 2],
    },
    VenetianBlinds {
        stripe_count: u32,
        softness: f32,
        vertical: bool,
    },
    CrossfadeZoom {
        zoom: f32,
        current_zooms_in: bool,
        next_zooms_in: bool,
    },
    Iris {
        blades: u32,
        color: [f32; 3],
        petal_sheen: f32,
        overlap_shadow: f32,
        min_aperture: f32,
        swirl: f32,
    },
}

pub(super) struct TexturePlane {
    pub(super) bind: wgpu::BindGroup,
    pub(super) w: u32,
    pub(super) h: u32,
}

pub(super) struct ImgTex {
    pub(super) plane: TexturePlane,
    pub(super) path: std::path::PathBuf,
    /// Mat kind that was baked for this image; `None` means full-bleed (no mat).
    pub(super) mat_kind: Option<crate::config::MattingKind>,
}

pub(super) struct TransitionState {
    started_at: std::time::Instant,
    duration: std::time::Duration,
    kind: TransitionKind,
    variant: ActiveTransition,
}

impl TransitionState {
    pub(super) fn new(
        selected: SelectedTransition<'_>,
        started_at: std::time::Instant,
        rng: &mut impl Rng,
    ) -> Self {
        let option = selected.option;
        let duration = option.duration();
        let kind = option.kind();
        let mode = option.mode().clone();
        let variant = match mode {
            TransitionMode::Fade(cfg) => ActiveTransition::Fade {
                through_black: cfg.through_black,
            },
            TransitionMode::Wipe(cfg) => {
                let angle = jittered_angle(&cfg.angles, rng);
                let normal = angle_to_unit_vec(angle);
                ActiveTransition::Wipe {
                    normal,
                    softness: cfg.softness,
                }
            }
            TransitionMode::Push(cfg) => {
                let angle = jittered_angle(&cfg.angles, rng);
                let direction = angle_to_unit_vec(angle);
                ActiveTransition::Push { direction }
            }
            TransitionMode::EInk(cfg) => ActiveTransition::EInk {
                flash_count: cfg.flash_count,
                reveal_portion: cfg.reveal_portion.clamp(0.05, 0.95),
                stripe_count: cfg.stripe_count.max(1),
                flash_color: cfg
                    .flash_color
                    .map(|channel| srgb_to_linear((channel as f32 / 255.0).clamp(0.0, 1.0))),
                noise_seed: [rng.random_range(0.0..=1.0), rng.random_range(0.0..=1.0)],
            },
            TransitionMode::Dissolve(cfg) => ActiveTransition::Dissolve {
                softness: cfg.softness,
                scale: cfg.scale,
            },
            TransitionMode::RadialWipe(cfg) => ActiveTransition::RadialWipe {
                softness: cfg.softness,
                shape_is_diamond: cfg.shape == crate::config::RadialShape::Diamond,
                center: cfg.center,
            },
            TransitionMode::VenetianBlinds(cfg) => ActiveTransition::VenetianBlinds {
                stripe_count: cfg.stripe_count.max(1),
                softness: cfg.softness,
                vertical: cfg.vertical,
            },
            TransitionMode::CrossfadeZoom(cfg) => ActiveTransition::CrossfadeZoom {
                zoom: cfg.zoom,
                current_zooms_in: cfg.current_zooms_in,
                next_zooms_in: cfg.next_zooms_in,
            },
            TransitionMode::Iris(cfg) => ActiveTransition::Iris {
                blades: cfg.blades,
                // Config colors are sRGB; the shader works in linear light
                // (its output is re-encoded by the sRGB render target).
                // Without this conversion the petals display ~2.5x lighter
                // than the configured color.
                color: cfg
                    .color
                    .map(|channel| srgb_to_linear((channel as f32 / 255.0).clamp(0.0, 1.0))),
                petal_sheen: cfg.petal_sheen,
                overlap_shadow: cfg.overlap_shadow,
                min_aperture: cfg.min_aperture,
                swirl: cfg.swirl,
            },
        };

        Self {
            started_at,
            duration,
            kind,
            variant,
        }
    }

    pub(super) fn is_complete(&self) -> bool {
        self.progress() >= 1.0
    }

    pub(super) fn progress(&self) -> f32 {
        let elapsed = self.started_at.elapsed().as_secs_f32();
        let duration = self.duration.as_secs_f32().max(f32::EPSILON);
        (elapsed / duration).clamp(0.0, 1.0)
    }

    pub(super) fn kind(&self) -> TransitionKind {
        self.kind
    }

    pub(super) fn variant(&self) -> &ActiveTransition {
        &self.variant
    }
}

/// Frame cadence accumulator for one transition playback, logged when the
/// transition ends so on-device performance is visible in the journal. Only
/// emitted when `metrics` is enabled in the config.
pub(super) struct TransitionFrameMetric {
    kind: TransitionKind,
    started: Instant,
    last_frame: Instant,
    frames: u32,
    worst_frame_ms: f32,
    best_frame_ms: f32,
}

impl TransitionFrameMetric {
    fn begin(kind: TransitionKind, now: Instant) -> Self {
        Self {
            kind,
            started: now,
            last_frame: now,
            frames: 1,
            worst_frame_ms: 0.0,
            best_frame_ms: f32::INFINITY,
        }
    }

    fn log(&self, enabled: bool) {
        if !enabled || self.frames < 2 {
            return;
        }
        let span = self
            .last_frame
            .duration_since(self.started)
            .as_secs_f32()
            .max(f32::EPSILON);
        let intervals = (self.frames - 1) as f32;
        info!(
            transition = %self.kind,
            frames = self.frames,
            avg_fps = format_args!("{:.1}", intervals / span),
            avg_frame_ms = format_args!("{:.1}", 1000.0 * span / intervals),
            best_frame_ms = format_args!("{:.1}", self.best_frame_ms),
            worst_frame_ms = format_args!("{:.1}", self.worst_frame_ms),
            "transition_frame_metric"
        );
    }
}

/// Convert one sRGB channel (0..1) to linear light, the space the transition
/// shader computes in. Constant colors fed to the shader must be linear or
/// the sRGB render target's encode pass displays them too bright.
fn srgb_to_linear(c: f32) -> f32 {
    if c <= 0.04045 {
        c / 12.92
    } else {
        ((c + 0.055) / 1.055).powf(2.4)
    }
}

fn jittered_angle(picker: &crate::config::AnglePicker, rng: &mut impl Rng) -> f32 {
    let base = picker.base_deg;
    let jitter = picker.jitter_deg;
    if jitter.abs() > f32::EPSILON {
        base + rng.random_range(-jitter..=jitter)
    } else {
        base
    }
}

#[derive(Clone)]
struct MatParams {
    screen_w: u32,
    screen_h: u32,
    oversample: f32,
    max_dim: u32,
    max_upscale_factor: f32,
    matting: MattingOptions,
    /// When true, render the photo full-bleed (cover-crop, no mat); `matting`
    /// is ignored. Chosen by the `fill-when-fits` pre-check at selection time.
    fill_screen: bool,
}

struct MatTask {
    image: PreparedImageCpu,
    params: MatParams,
    priority: bool,
    mat_kind: Option<crate::config::MattingKind>,
}

struct ImagePlane {
    width: u32,
    height: u32,
    pixels: Vec<u8>,
}

struct MatResult {
    path: std::path::PathBuf,
    canvas: ImagePlane,
    priority: bool,
    mat_kind: Option<crate::config::MattingKind>,
}

struct QueuedImage {
    image: PreparedImageCpu,
    priority: bool,
}

struct MattingPipeline {
    task_tx: CbSender<MatTask>,
    result_rx: CbReceiver<MatResult>,
}

impl MattingPipeline {
    fn new(worker_count: usize, capacity: usize) -> Self {
        let worker_count = worker_count.max(1);
        let capacity = capacity.max(worker_count).max(2);
        let (task_tx, task_rx) = bounded::<MatTask>(capacity);
        let (result_tx, result_rx) = bounded::<MatResult>(capacity);
        let task_rx = Arc::new(task_rx);
        let result_tx = Arc::new(result_tx);
        for _ in 0..worker_count {
            let task_rx = Arc::clone(&task_rx);
            let result_tx = Arc::clone(&result_tx);
            std::thread::spawn(move || {
                while let Ok(task) = task_rx.recv() {
                    if let Some(result) = process_mat_task(task)
                        && result_tx.send(result).is_err()
                    {
                        break;
                    }
                }
            });
        }
        Self { task_tx, result_rx }
    }

    // MatTask is large by design (contains image buffers); returning it on error
    // lets the caller reclaim the task without re-allocation.
    #[allow(clippy::result_large_err)]
    fn try_submit(&self, task: MatTask) -> Result<(), MatTask> {
        match self.task_tx.try_send(task) {
            Ok(()) => Ok(()),
            Err(TrySendError::Full(task)) | Err(TrySendError::Disconnected(task)) => Err(task),
        }
    }

    fn try_recv(&self) -> Option<MatResult> {
        self.result_rx.try_recv().ok()
    }
}

#[derive(Clone, Copy)]
struct SurfaceState {
    width: u32,
    height: u32,
    max_texture_dimension: u32,
}

impl SurfaceState {
    fn from_config(config: &wgpu::SurfaceConfiguration, limits: &wgpu::Limits) -> Self {
        Self {
            width: config.width,
            height: config.height,
            max_texture_dimension: limits.max_texture_dimension_2d,
        }
    }

    #[cfg(test)]
    fn new(width: u32, height: u32, max_texture_dimension: u32) -> Self {
        Self {
            width,
            height,
            max_texture_dimension,
        }
    }
}

#[derive(Clone, Copy, Debug)]
enum SurfaceReport {
    InitialConfig,
    ConfigureEvent,
}

#[derive(Clone, Copy, Default)]
struct SurfaceReadyGate {
    ready: bool,
    awaiting: bool,
    last_size: Option<(u32, u32)>,
    same_count: u8,
    stable_since: Option<Instant>,
}

// Enforces minimum stability before declaring the surface ready.
const SURFACE_READY_DWELL: Duration = Duration::from_millis(120);

impl SurfaceReadyGate {
    fn reset(&mut self) {
        self.ready = false;
        self.awaiting = false;
        self.last_size = None;
        self.same_count = 0;
        self.stable_since = None;
    }

    fn arm_for_initial_report(&mut self) {
        self.awaiting = true;
        self.ready = false;
        self.last_size = None;
        self.same_count = 0;
        self.stable_since = None;
    }

    fn update(&mut self, width: u32, height: u32, report: SurfaceReport) -> Option<bool> {
        // Ignore bootstrap config; wait for compositor configure events
        if matches!(report, SurfaceReport::InitialConfig) {
            return self.set_ready(false);
        }

        if width == 0 || height == 0 {
            self.last_size = Some((0, 0));
            self.same_count = 0;
            self.stable_since = None;
            return self.set_ready(false);
        }

        match self.last_size {
            Some((w, h)) if w == width && h == height => {
                self.same_count = self.same_count.saturating_add(1);
            }
            _ => {
                self.last_size = Some((width, height));
                self.same_count = 1;
                self.stable_since = Some(Instant::now());
            }
        }

        // Require two consecutive identical, non-zero reports and a small dwell time
        let dwell_met = self
            .stable_since
            .map(|t| Instant::now().saturating_duration_since(t) >= SURFACE_READY_DWELL)
            .unwrap_or(false);
        let now_ready = self.awaiting && self.same_count >= 2 && dwell_met;
        if now_ready {
            self.awaiting = false;
        }
        self.set_ready(now_ready || self.ready)
    }

    fn is_ready(&self) -> bool {
        self.ready
    }

    fn set_ready(&mut self, ready: bool) -> Option<bool> {
        if self.ready != ready {
            self.ready = ready;
            Some(ready)
        } else {
            None
        }
    }
}

struct MattingBridge<'a> {
    preload_count: usize,
    mat_inflight: &'a mut usize,
    deferred_images: &'a mut VecDeque<QueuedImage>,
    ready_results: &'a mut VecDeque<MatResult>,
    from_loader: &'a mut Receiver<PhotoLoaded>,
    surface: Option<SurfaceState>,
    matting: &'a MattingConfig,
    oversample: f32,
    max_upscale_factor: f32,
    mat_pipeline: &'a MattingPipeline,
}

fn surface_state_for_queue(
    surface_configured: bool,
    surface: Option<SurfaceState>,
) -> Option<SurfaceState> {
    if surface_configured { surface } else { None }
}

impl<'a> MattingBridge<'a> {
    fn queue_for_wake(&mut self, wake: &mut scenes::WakeScene) {
        // Don't kick off new decode/matting work while a transition is
        // animating. The work itself runs on worker threads, but its JPEG
        // decode and NEON blur bursts compete for the same unified memory
        // bandwidth the GPU is using, which shows up as dropped frames.
        // A transition consumes the staged photo and immediately drops the
        // preload depth below target, so without this gate the refill always
        // lands exactly during the animation. Dwell time (seconds) dwarfs
        // prep time; deferring the kickoff costs nothing.
        if wake.transition_state().is_some() {
            return;
        }
        while wake.pending().len() + *self.mat_inflight < self.preload_count {
            let next_img = if let Some(img) = self.deferred_images.pop_front() {
                Some(img)
            } else {
                match self.from_loader.try_recv() {
                    Ok(PhotoLoaded { prepared, priority }) => Some(QueuedImage {
                        image: prepared,
                        priority,
                    }),
                    Err(_) => None,
                }
            };
            let Some(queued) = next_img else {
                break;
            };
            let path = queued.image.path.clone();
            if queued.priority {
                self.deferred_images
                    .retain(|pending| pending.image.path != path);
                self.ready_results.retain(|pending| pending.path != path);
                wake.pending_mut().retain(|pending| pending.path != path);
                if wake.next().is_some_and(|stage| stage.path == path) {
                    wake.set_next(None);
                }
            }
            let Some(surface) = self.surface else {
                self.deferred_images.push_front(queued);
                break;
            };
            if surface.width <= 1 || surface.height <= 1 {
                debug!(
                    screen_w = surface.width,
                    screen_h = surface.height,
                    path = %path.display(),
                    "deferring_matting_until_surface_configured"
                );
                self.deferred_images.push_front(queued);
                break;
            }
            let mut rng = rand::rng();
            let fill_screen = self
                .matting
                .fill_when_fits()
                .map(|fill| {
                    fill.should_fill(
                        queued.image.width,
                        queued.image.height,
                        surface.width.max(1),
                        surface.height.max(1),
                        self.max_upscale_factor,
                        &mut rng,
                    )
                })
                .unwrap_or(false);
            // When filling the screen, the selected mat is ignored. Use a
            // non-mutating placeholder so the sequential selector is not
            // advanced for a photo that renders without a mat.
            let matting = if fill_screen {
                self.matting
                    .primary_option()
                    .cloned()
                    .expect("validated matting configuration has at least one option")
            } else {
                self.matting.select_active(&mut rng).option.clone()
            };
            let params = MatParams {
                screen_w: surface.width.max(1),
                screen_h: surface.height.max(1),
                oversample: self.oversample,
                max_dim: surface.max_texture_dimension,
                max_upscale_factor: self.max_upscale_factor,
                matting,
                fill_screen,
            };
            let mat_kind = if fill_screen {
                None
            } else {
                Some(params.matting.kind())
            };
            let QueuedImage {
                image: img,
                priority,
            } = queued;
            let task = MatTask {
                image: img,
                params,
                priority,
                mat_kind,
            };
            match self.mat_pipeline.try_submit(task) {
                Ok(()) => {
                    *self.mat_inflight += 1;
                }
                Err(MatTask {
                    image, priority, ..
                }) => {
                    self.deferred_images
                        .push_front(QueuedImage { image, priority });
                    break;
                }
            }
        }
    }
}

//
// Viewer state machine overview
// -----------------------------
//  - `ViewerModeKind::Greeting` shows the greeting overlay once after resume and
//    stays idle until the first photo is ready.
//  - `ViewerModeKind::Wake` drives the continuous photo slideshow, requesting
//    redraws while transitions or new frames are pending.
//  - `ViewerModeKind::Sleep` renders a single "Going to Sleep" banner and then
//    idles until the power state changes again.
//
// Redraw policy
//  - Greeting/Sleep request exactly one redraw on entry and after resizes.
//  - Wake continuously requests redraws via `about_to_wait` while work is
//    pending. Each state transition recreates the greeting resources to keep
//    scale/format in sync.

const CONTROL_TICK_INTERVAL: Duration = Duration::from_millis(4);
fn process_mat_task(task: MatTask) -> Option<MatResult> {
    let MatTask {
        image,
        params,
        priority,
        mat_kind,
    } = task;
    let PreparedImageCpu {
        path,
        width,
        height,
        pixels,
    } = image;
    if width == 0 || height == 0 {
        return None;
    }
    let src = RgbaImage::from_raw(width, height, pixels)?;
    let MatParams {
        screen_w,
        screen_h,
        oversample,
        max_dim,
        max_upscale_factor,
        matting,
        fill_screen,
    } = params;
    if screen_w == 0 || screen_h == 0 {
        return None;
    }

    let (canvas_w, canvas_h) = compute_canvas_size(screen_w, screen_h, oversample, max_dim);

    // `fill-when-fits`: render the photo full-bleed (cover-crop, no mat).
    if fill_screen {
        let canvas = scale_image_to_cover_canvas(&src, canvas_w, canvas_h, max_dim);
        let canvas = ImagePlane {
            width: canvas_w,
            height: canvas_h,
            pixels: canvas.into_raw(),
        };
        return Some(MatResult {
            path,
            canvas,
            priority,
            mat_kind,
        });
    }

    let margin = (matting.minimum_mat_percentage / 100.0).clamp(0.0, 0.45);
    let max_upscale = max_upscale_factor.max(1.0);
    let avg_color = average_color(&src);

    if let MattingMode::Studio {
        bevel_width_px,
        bevel_color,
        texture_strength,
        warp_period_px,
        weft_period_px,
        ..
    } = &matting.style
    {
        let mat_color = matting.runtime.studio_color(avg_color).unwrap_or(avg_color);
        let mut bevel_px = bevel_width_px.max(0.0);
        let margin_x = (canvas_w as f32 * margin).round();
        let margin_y = (canvas_h as f32 * margin).round();
        let inner_w = (canvas_w as f32 - 2.0 * margin_x).max(1.0);
        let inner_h = (canvas_h as f32 - 2.0 * margin_y).max(1.0);
        let max_bevel = 0.5 * inner_w.min(inner_h).max(0.0);
        if max_bevel <= 0.0 {
            bevel_px = 0.0;
        } else {
            bevel_px = bevel_px.min(max_bevel);
        }
        let photo_space_w = (canvas_w as f32 - 2.0 * (margin_x + bevel_px)).max(1.0);
        let photo_space_h = (canvas_h as f32 - 2.0 * (margin_y + bevel_px)).max(1.0);

        let iw = width.max(1) as f32;
        let ih = height.max(1) as f32;
        let mut scale = (photo_space_w / iw)
            .min(photo_space_h / ih)
            .min(max_upscale);
        if !scale.is_finite() || scale <= 0.0 {
            scale = 1.0;
        }
        let max_photo_w = photo_space_w.floor().max(1.0);
        let max_photo_h = photo_space_h.floor().max(1.0);
        let mut photo_w = (iw * scale).round().clamp(1.0, max_photo_w);
        let mut photo_h = (ih * scale).round().clamp(1.0, max_photo_h);
        photo_w = photo_w.clamp(1.0, canvas_w as f32);
        photo_h = photo_h.clamp(1.0, canvas_h as f32);
        let photo_w = photo_w as u32;
        let photo_h = photo_h as u32;
        let (offset_x, offset_y) = center_offset(photo_w, photo_h, canvas_w, canvas_h);

        let main_img: Cow<'_, RgbaImage> = if photo_w == width && photo_h == height {
            Cow::Borrowed(&src)
        } else {
            Cow::Owned(imageops::resize(
                &src,
                photo_w,
                photo_h,
                imageops::FilterType::Triangle,
            ))
        };

        let canvas = render_studio_mat(
            canvas_w,
            canvas_h,
            offset_x,
            offset_y,
            photo_w,
            photo_h,
            main_img.as_ref(),
            mat_color,
            bevel_px,
            *bevel_color,
            *texture_strength,
            *warp_period_px,
            *weft_period_px,
        );

        let canvas = ImagePlane {
            width: canvas_w,
            height: canvas_h,
            pixels: canvas.into_raw(),
        };

        return Some(MatResult {
            path,
            canvas,
            priority,
            mat_kind,
        });
    }

    if let MattingMode::PassePartout {
        bevel_width_px,
        bevel_color,
        ..
    } = &matting.style
    {
        let mat_color = matting
            .runtime
            .passe_partout_color(avg_color)
            .unwrap_or(avg_color);
        let mut bevel_px = bevel_width_px.max(0.0);
        let margin_x = (canvas_w as f32 * margin).round();
        let margin_y = (canvas_h as f32 * margin).round();
        let inner_w = (canvas_w as f32 - 2.0 * margin_x).max(1.0);
        let inner_h = (canvas_h as f32 - 2.0 * margin_y).max(1.0);
        let max_bevel = 0.5 * inner_w.min(inner_h).max(0.0);
        if max_bevel <= 0.0 {
            bevel_px = 0.0;
        } else {
            bevel_px = bevel_px.min(max_bevel);
        }
        let photo_space_w = (canvas_w as f32 - 2.0 * (margin_x + bevel_px)).max(1.0);
        let photo_space_h = (canvas_h as f32 - 2.0 * (margin_y + bevel_px)).max(1.0);

        let iw = width.max(1) as f32;
        let ih = height.max(1) as f32;
        let mut scale = (photo_space_w / iw)
            .min(photo_space_h / ih)
            .min(max_upscale);
        if !scale.is_finite() || scale <= 0.0 {
            scale = 1.0;
        }
        let max_photo_w = photo_space_w.floor().max(1.0);
        let max_photo_h = photo_space_h.floor().max(1.0);
        let mut photo_w = (iw * scale).round().clamp(1.0, max_photo_w);
        let mut photo_h = (ih * scale).round().clamp(1.0, max_photo_h);
        photo_w = photo_w.clamp(1.0, canvas_w as f32);
        photo_h = photo_h.clamp(1.0, canvas_h as f32);
        let photo_w = photo_w as u32;
        let photo_h = photo_h as u32;
        let (offset_x, offset_y) = center_offset(photo_w, photo_h, canvas_w, canvas_h);

        let main_img: Cow<'_, RgbaImage> = if photo_w == width && photo_h == height {
            Cow::Borrowed(&src)
        } else {
            Cow::Owned(imageops::resize(
                &src,
                photo_w,
                photo_h,
                imageops::FilterType::Triangle,
            ))
        };

        let canvas = render_studio_mat(
            canvas_w,
            canvas_h,
            offset_x,
            offset_y,
            photo_w,
            photo_h,
            main_img.as_ref(),
            mat_color,
            bevel_px,
            *bevel_color,
            0.0,
            5.6,
            5.2,
        );

        let canvas = ImagePlane {
            width: canvas_w,
            height: canvas_h,
            pixels: canvas.into_raw(),
        };

        return Some(MatResult {
            path,
            canvas,
            priority,
            mat_kind,
        });
    }

    if let MattingMode::DropShadow {
        shadow_color,
        shadow_opacity,
        shadow_blur_px,
        shadow_offset_px,
        ..
    } = &matting.style
    {
        let color = f32_rgb_to_u8(
            matting
                .runtime
                .drop_shadow_color(avg_color)
                .unwrap_or(avg_color),
        );
        let (final_w, final_h) =
            resize_to_fit_with_margin(canvas_w, canvas_h, width, height, margin, max_upscale);
        let (offset_x, offset_y) = center_offset(final_w, final_h, canvas_w, canvas_h);

        let main_img: Cow<'_, RgbaImage> = if final_w == width && final_h == height {
            Cow::Borrowed(&src)
        } else {
            Cow::Owned(imageops::resize(
                &src,
                final_w,
                final_h,
                imageops::FilterType::Triangle,
            ))
        };

        let bg_px = Rgba([color[0], color[1], color[2], 255]);
        let mut background = RgbaImage::from_pixel(canvas_w, canvas_h, bg_px);

        render_drop_shadow(
            &mut background,
            offset_x,
            offset_y,
            final_w,
            final_h,
            DropShadowParams {
                color: *shadow_color,
                opacity: *shadow_opacity,
                blur_px: *shadow_blur_px,
                offset_px: *shadow_offset_px,
            },
        );

        imageops::overlay(
            &mut background,
            main_img.as_ref(),
            offset_x as i64,
            offset_y as i64,
        );

        let canvas = ImagePlane {
            width: canvas_w,
            height: canvas_h,
            pixels: background.into_raw(),
        };

        return Some(MatResult {
            path,
            canvas,
            priority,
            mat_kind,
        });
    }

    let (final_w, final_h) =
        resize_to_fit_with_margin(canvas_w, canvas_h, width, height, margin, max_upscale);
    let (offset_x, offset_y) = center_offset(final_w, final_h, canvas_w, canvas_h);

    let main_img: Cow<'_, RgbaImage> = if final_w == width && final_h == height {
        Cow::Borrowed(&src)
    } else {
        Cow::Owned(imageops::resize(
            &src,
            final_w,
            final_h,
            imageops::FilterType::Triangle,
        ))
    };

    let mut background = match &matting.style {
        MattingMode::FixedColor { colors, .. } => {
            let color = matting
                .runtime
                .fixed_color()
                .or_else(|| colors.first().copied())
                .unwrap_or([0, 0, 0]);
            let px = Rgba([color[0], color[1], color[2], 255]);
            RgbaImage::from_pixel(canvas_w, canvas_h, px)
        }
        MattingMode::Blur {
            sigma,
            sample_scale,
            backend,
        } => {
            let bg = scale_image_to_cover_canvas(&src, canvas_w, canvas_h, max_dim);
            if *sigma > 0.0 {
                let mut sample = bg;
                let mut sigma_px = *sigma;
                let scale = if sample_scale.is_finite() {
                    *sample_scale
                } else {
                    MattingMode::default_blur_sample_scale()
                }
                .clamp(0.01, 1.0);
                if scale < 1.0 {
                    let sample_w = ((canvas_w as f32) * scale)
                        .round()
                        .clamp(1.0, canvas_w as f32) as u32;
                    let sample_h = ((canvas_h as f32) * scale)
                        .round()
                        .clamp(1.0, canvas_h as f32) as u32;
                    sample = imageops::resize(
                        &sample,
                        sample_w,
                        sample_h,
                        imageops::FilterType::CatmullRom,
                    );
                    sigma_px *= scale.max(0.01);
                }

                let mut blurred: RgbaImage = apply_blur(&sample, sigma_px, *backend);
                if blurred.width() != canvas_w || blurred.height() != canvas_h {
                    blurred = imageops::resize(
                        &blurred,
                        canvas_w,
                        canvas_h,
                        imageops::FilterType::CatmullRom,
                    );
                }
                blurred
            } else {
                bg
            }
        }
        MattingMode::Studio { .. } => unreachable!(),
        MattingMode::PassePartout { .. } => unreachable!(),
        MattingMode::DropShadow { .. } => unreachable!(),
        MattingMode::Gradient {
            start_color,
            end_color,
            direction,
            angle_degrees,
        } => render_gradient_canvas(
            canvas_w,
            canvas_h,
            *start_color,
            *end_color,
            *direction,
            *angle_degrees,
        ),
        MattingMode::Vignette {
            strength,
            radius,
            softness,
            ..
        } => {
            let resolved = matting
                .runtime
                .vignette_color(avg_color)
                .unwrap_or(avg_color);
            let color = f32_rgb_to_u8(resolved);
            render_vignette_canvas(canvas_w, canvas_h, color, *strength, *radius, *softness)
        }
        MattingMode::CinematicBlur {
            sigma,
            sample_scale,
            backend,
            darken,
            vignette_strength,
        } => {
            let bg = scale_image_to_cover_canvas(&src, canvas_w, canvas_h, max_dim);
            let mut blurred = if *sigma > 0.0 {
                let mut sample = bg;
                let mut sigma_px = *sigma;
                let scale = if sample_scale.is_finite() {
                    *sample_scale
                } else {
                    MattingMode::default_blur_sample_scale()
                }
                .clamp(0.01, 1.0);
                if scale < 1.0 {
                    let sample_w = ((canvas_w as f32) * scale)
                        .round()
                        .clamp(1.0, canvas_w as f32) as u32;
                    let sample_h = ((canvas_h as f32) * scale)
                        .round()
                        .clamp(1.0, canvas_h as f32) as u32;
                    sample = imageops::resize(
                        &sample,
                        sample_w,
                        sample_h,
                        imageops::FilterType::CatmullRom,
                    );
                    sigma_px *= scale.max(0.01);
                }
                let mut b: RgbaImage = apply_blur(&sample, sigma_px, *backend);
                if b.width() != canvas_w || b.height() != canvas_h {
                    b = imageops::resize(&b, canvas_w, canvas_h, imageops::FilterType::CatmullRom);
                }
                b
            } else {
                bg
            };
            let darken = darken.clamp(0.0, 1.0);
            let brightness = 1.0 - darken;
            for px in blurred.pixels_mut() {
                px[0] = (px[0] as f32 * brightness).round() as u8;
                px[1] = (px[1] as f32 * brightness).round() as u8;
                px[2] = (px[2] as f32 * brightness).round() as u8;
            }
            apply_vignette_overlay(&mut blurred, *vignette_strength, 0.75, 0.5);
            blurred
        }
        MattingMode::FixedImage { fit, .. } => {
            if let Some(bg) = matting.runtime.fixed_image() {
                match bg.canvas_for(*fit, canvas_w, canvas_h, max_dim) {
                    Ok(prepared) => prepared.as_ref().clone(),
                    Err(err) => {
                        warn!(
                            "failed to prepare fixed background from {}: {err}",
                            bg.path().display()
                        );
                        RgbaImage::from_pixel(canvas_w, canvas_h, Rgba([0, 0, 0, 255]))
                    }
                }
            } else {
                RgbaImage::from_pixel(canvas_w, canvas_h, Rgba([0, 0, 0, 255]))
            }
        }
    };

    imageops::overlay(
        &mut background,
        main_img.as_ref(),
        offset_x as i64,
        offset_y as i64,
    );

    let canvas = ImagePlane {
        width: canvas_w,
        height: canvas_h,
        pixels: background.into_raw(),
    };

    Some(MatResult {
        path,
        canvas,
        priority,
        mat_kind,
    })
}

#[derive(Debug)]
enum ViewerEvent {
    Tick,
    Command(ViewerCommand),
    Cancelled,
}

async fn drive_viewer_events(
    mut control: Receiver<ViewerCommand>,
    cancel: CancellationToken,
    proxy: winit::event_loop::EventLoopProxy<ViewerEvent>,
) {
    let mut ticker = interval(CONTROL_TICK_INTERVAL);
    ticker.set_missed_tick_behavior(MissedTickBehavior::Skip);

    if proxy.send_event(ViewerEvent::Tick).is_err() {
        return;
    }

    loop {
        tokio::select! {
            _ = cancel.cancelled() => {
                let _ = proxy.send_event(ViewerEvent::Cancelled);
                break;
            }
            _ = ticker.tick() => {
                if proxy.send_event(ViewerEvent::Tick).is_err() {
                    warn!("viewer event proxy rejected tick event; stopping driver loop");
                    break;
                }
            }
            cmd = control.recv() => {
                match cmd {
                    Some(cmd) => {
                        debug!(command = ?cmd, "viewer_event_forward_command");
                        if proxy.send_event(ViewerEvent::Command(cmd)).is_err() {
                            warn!("viewer event proxy rejected command event; stopping driver loop");
                            break;
                        }
                    }
                    None => {
                        warn!("viewer control channel closed; stopping driver loop");
                        break;
                    }
                }
            }
        }
    }
}

pub fn run_windowed(
    from_loader: Receiver<PhotoLoaded>,
    to_manager_displayed: Sender<Displayed>,
    cancel: CancellationToken,
    cfg: Arc<crate::config::Configuration>,
    mut control: Receiver<ViewerCommand>,
) -> anyhow::Result<()> {
    use winit::application::ApplicationHandler;
    use winit::event::WindowEvent;
    use winit::event_loop::{ActiveEventLoop, EventLoop, EventLoopProxy};
    use winit::window::{Fullscreen, Window, WindowAttributes, WindowId};

    fn with_photo_app_id(attrs: WindowAttributes) -> WindowAttributes {
        #[cfg(any(
            target_os = "linux",
            target_os = "dragonfly",
            target_os = "freebsd",
            target_os = "netbsd",
            target_os = "openbsd"
        ))]
        {
            use winit::platform::wayland::WindowAttributesExtWayland;
            return attrs.with_name("photoframe", "photoframe");
        }

        #[cfg(not(any(
            target_os = "linux",
            target_os = "dragonfly",
            target_os = "freebsd",
            target_os = "netbsd",
            target_os = "openbsd"
        )))]
        {
            attrs
        }
    }

    #[repr(C)]
    #[derive(Clone, Copy, bytemuck::Pod, bytemuck::Zeroable)]
    struct TransitionUniforms {
        screen_size: [f32; 2],
        progress: f32,
        kind: u32,
        current_dest: [f32; 4],
        next_dest: [f32; 4],
        params0: [f32; 4],
        params1: [f32; 4],
        params3: [f32; 4],
        // Viewer background (linear RGB, alpha unused). The shader composites
        // letterbox regions over this itself so the pipeline can render
        // opaquely without a per-pixel destination read for blending.
        background: [f32; 4],
        // Per-petal constants for the iris transition, solved on the CPU each
        // frame so the fragment loop needs no transcendentals:
        // petals_a[i] = (annulus_center.xy, tip_dir.xy)
        // petals_b[i] = (trail_dir.xy, facing_cosine, unused)
        petals_a: [[f32; 4]; 16],
        petals_b: [[f32; 4]; 16],
    }

    struct GpuCtx {
        device: wgpu::Device,
        queue: wgpu::Queue,
        surface: wgpu::Surface<'static>,
        config: wgpu::SurfaceConfiguration,
        limits: wgpu::Limits,
        uniform_buf: wgpu::Buffer,
        uniform_bind: wgpu::BindGroup,
        img_bind_layout: wgpu::BindGroupLayout,
        sampler: wgpu::Sampler,
        pipeline: wgpu::RenderPipeline,
        blank_plane: TexturePlane,
        iris_layer_pipeline: wgpu::RenderPipeline,
        iris_layer: Option<OffscreenTarget>,
        blit_pipeline: wgpu::RenderPipeline,
        half_target: Option<OffscreenTarget>,
    }

    /// Reduced-resolution offscreen render target that can also be sampled.
    /// At 4K the Pi's frame cost is dominated by per-pixel fill, so heavy
    /// passes render at a fraction of the surface size and get upsampled:
    /// the iris petal layer at 1/IRIS_LAYER_SCALE, and every transition
    /// frame at 1/TRANSITION_HALF_SCALE.
    struct OffscreenTarget {
        view: wgpu::TextureView,
        bind: wgpu::BindGroup,
        w: u32,
        h: u32,
    }

    impl GpuCtx {
        fn make_offscreen(
            &self,
            label: &str,
            w: u32,
            h: u32,
            format: wgpu::TextureFormat,
        ) -> OffscreenTarget {
            let tex = self.device.create_texture(&wgpu::TextureDescriptor {
                label: Some(label),
                size: wgpu::Extent3d {
                    width: w,
                    height: h,
                    depth_or_array_layers: 1,
                },
                mip_level_count: 1,
                sample_count: 1,
                dimension: wgpu::TextureDimension::D2,
                format,
                usage: wgpu::TextureUsages::RENDER_ATTACHMENT
                    | wgpu::TextureUsages::TEXTURE_BINDING,
                view_formats: &[],
            });
            let view = tex.create_view(&wgpu::TextureViewDescriptor::default());
            let bind = self.device.create_bind_group(&wgpu::BindGroupDescriptor {
                label: Some(label),
                layout: &self.img_bind_layout,
                entries: &[
                    wgpu::BindGroupEntry {
                        binding: 0,
                        resource: wgpu::BindingResource::TextureView(&view),
                    },
                    wgpu::BindGroupEntry {
                        binding: 1,
                        resource: wgpu::BindingResource::Sampler(&self.sampler),
                    },
                ],
            });
            OffscreenTarget { view, bind, w, h }
        }

        /// Create (or re-create after a resize) the iris petal layer so it
        /// tracks the current surface size.
        fn ensure_iris_layer(&mut self) {
            let scale = iris_layer_scale();
            let w = (self.config.width / scale).max(1);
            let h = (self.config.height / scale).max(1);
            if let Some(layer) = self.iris_layer.as_ref()
                && layer.w == w
                && layer.h == h
            {
                return;
            }
            // Half-float, not 8-bit: the petals are very dark in linear light,
            // so a smooth shading gradient spans only a handful of 8-bit
            // levels and visibly bands. Rgba16Float has ample dark-range
            // precision; the layer is quarter-res so the extra bytes are
            // negligible.
            self.iris_layer = Some(self.make_offscreen(
                "iris-petal-layer",
                w,
                h,
                wgpu::TextureFormat::Rgba16Float,
            ));
        }

        /// Create (or re-create after a resize) the reduced-resolution
        /// intermediate that transition frames render into.
        fn ensure_half_target(&mut self) {
            let scale = transition_scale();
            let w = (self.config.width / scale).max(1);
            let h = (self.config.height / scale).max(1);
            if let Some(target) = self.half_target.as_ref()
                && target.w == w
                && target.h == h
            {
                return;
            }
            let format = self.config.format;
            self.half_target = Some(self.make_offscreen("transition-half-target", w, h, format));
        }
    }

    fn upload_plane(gpu: &GpuCtx, plane: ImagePlane) -> Option<TexturePlane> {
        let ImagePlane {
            width,
            height,
            pixels,
        } = plane;
        if width == 0 || height == 0 {
            return None;
        }
        let tex = gpu.device.create_texture(&wgpu::TextureDescriptor {
            label: Some("photo-texture"),
            size: wgpu::Extent3d {
                width,
                height,
                depth_or_array_layers: 1,
            },
            mip_level_count: 1,
            sample_count: 1,
            dimension: wgpu::TextureDimension::D2,
            format: wgpu::TextureFormat::Rgba8UnormSrgb,
            usage: wgpu::TextureUsages::TEXTURE_BINDING | wgpu::TextureUsages::COPY_DST,
            view_formats: &[],
        });
        let stride = 4 * width;
        let padded = compute_padded_stride(stride);
        let upload: Cow<'_, [u8]> = if padded != stride {
            let mut staging = vec![0u8; (padded as usize) * (height as usize)];
            let rs = stride as usize;
            let rd = padded as usize;
            for y in 0..(height as usize) {
                let so = y * rs;
                let doff = y * rd;
                staging[doff..doff + rs].copy_from_slice(&pixels[so..so + rs]);
            }
            Cow::Owned(staging)
        } else {
            Cow::Borrowed(&pixels)
        };
        gpu.queue.write_texture(
            wgpu::TexelCopyTextureInfo {
                texture: &tex,
                mip_level: 0,
                origin: wgpu::Origin3d::ZERO,
                aspect: wgpu::TextureAspect::All,
            },
            upload.as_ref(),
            wgpu::TexelCopyBufferLayout {
                offset: 0,
                bytes_per_row: Some(padded),
                rows_per_image: Some(height),
            },
            wgpu::Extent3d {
                width,
                height,
                depth_or_array_layers: 1,
            },
        );
        let view = tex.create_view(&wgpu::TextureViewDescriptor::default());
        let bind = gpu.device.create_bind_group(&wgpu::BindGroupDescriptor {
            label: Some("image-bind"),
            layout: &gpu.img_bind_layout,
            entries: &[
                wgpu::BindGroupEntry {
                    binding: 0,
                    resource: wgpu::BindingResource::TextureView(&view),
                },
                wgpu::BindGroupEntry {
                    binding: 1,
                    resource: wgpu::BindingResource::Sampler(&gpu.sampler),
                },
            ],
        });
        Some(TexturePlane {
            bind,
            w: width,
            h: height,
        })
    }

    fn upload_mat_result(gpu: &GpuCtx, result: MatResult) -> Option<ImgTex> {
        let MatResult {
            path,
            canvas,
            mat_kind,
            ..
        } = result;
        let plane = upload_plane(gpu, canvas)?;
        Some(ImgTex {
            plane,
            path,
            mat_kind,
        })
    }

    #[derive(Debug, Copy, Clone, Eq, PartialEq)]
    enum ViewerModeKind {
        Greeting,
        Wake,
        Sleep,
    }

    struct ViewerMode {
        kind: ViewerModeKind,
        greeting: Option<GreetingScene>,
        wake: scenes::WakeScene,
        sleep: Option<SleepScene>,
    }

    #[derive(Copy, Clone, Debug)]
    enum SceneHook {
        Enter,
        Exit,
    }

    impl ViewerMode {
        fn new(kind: ViewerModeKind, wake: scenes::WakeScene) -> Self {
            Self {
                kind,
                greeting: None,
                wake,
                sleep: None,
            }
        }

        fn kind(&self) -> ViewerModeKind {
            self.kind
        }

        fn wake(&self) -> &scenes::WakeScene {
            &self.wake
        }

        fn wake_mut(&mut self) -> &mut scenes::WakeScene {
            &mut self.wake
        }

        fn greeting(&self) -> Option<&GreetingScene> {
            self.greeting.as_ref()
        }

        fn greeting_mut(&mut self) -> Option<&mut GreetingScene> {
            self.greeting.as_mut()
        }

        fn sleep(&self) -> Option<&SleepScene> {
            self.sleep.as_ref()
        }

        fn sleep_mut(&mut self) -> Option<&mut SleepScene> {
            self.sleep.as_mut()
        }

        #[allow(clippy::too_many_arguments)]
        fn with_scene_mut<'a, R>(
            &'a mut self,
            window: Option<&'a Window>,
            config: Arc<crate::config::Configuration>,
            redraw: &'a mut dyn FnMut(),
            rng: &'a mut rand::rngs::ThreadRng,
            notify_displayed: &'a mut dyn FnMut(std::path::PathBuf),
            enqueue_matting: &'a mut dyn FnMut(&mut scenes::WakeScene),
            f: impl FnOnce(&mut dyn Scene, SceneContext<'a>) -> R,
        ) -> Option<R> {
            let ctx = SceneContext::new(
                window,
                redraw,
                config,
                rng,
                notify_displayed,
                enqueue_matting,
            );
            match self.kind {
                ViewerModeKind::Greeting => Some(f(self.greeting.as_mut()?, ctx)),
                ViewerModeKind::Wake => Some(f(&mut self.wake, ctx)),
                ViewerModeKind::Sleep => Some(f(self.sleep.as_mut()?, ctx)),
            }
        }

        fn set_overlays(&mut self, greeting: Option<GreetingScene>, sleep: Option<SleepScene>) {
            self.greeting = greeting;
            self.sleep = sleep;
        }

        fn into_kind(self, kind: ViewerModeKind) -> Self {
            Self { kind, ..self }
        }
    }

    struct App {
        from_loader: Receiver<PhotoLoaded>,
        to_manager_displayed: Sender<Displayed>,
        cancel: CancellationToken,
        window: Option<Arc<Window>>,
        gpu: Option<GpuCtx>,
        surface_configured: bool,
        surface_gate: SurfaceReadyGate,
        pending_scene_enter: bool,
        mode: Option<ViewerMode>,
        preload_count: usize,
        oversample: f32,
        max_upscale_factor: f32,
        matting: MattingConfig,
        mat_pipeline: MattingPipeline,
        mat_inflight: usize,
        ready_results: VecDeque<MatResult>,
        deferred_images: VecDeque<QueuedImage>,
        clear_color: wgpu::Color,
        rng: rand::rngs::ThreadRng,
        full_config: Arc<crate::config::Configuration>,
        surface_timeout_streak: u32,
        // Last surface size that we considered "configured" and stabilized
        configured_surface_size: Option<(u32, u32)>,
        /// Caption overlay for showcase mode; `None` when showcase is disabled.
        caption_overlay: Option<scenes::CaptionOverlay>,
        /// Frame cadence of the transition currently being presented.
        transition_frame_metric: Option<TransitionFrameMetric>,
    }

    impl App {
        fn mode(&self) -> &ViewerMode {
            self.mode.as_ref().expect("viewer mode not initialized")
        }

        fn mode_mut(&mut self) -> &mut ViewerMode {
            self.mode.as_mut().expect("viewer mode not initialized")
        }

        fn active_surface(&self) -> Option<SurfaceState> {
            if !self.surface_configured {
                return None;
            }
            self.gpu
                .as_ref()
                .map(|gpu| SurfaceState::from_config(&gpu.config, &gpu.limits))
        }

        fn update_surface_ready(&mut self, width: u32, height: u32, report: SurfaceReport) -> bool {
            if let Some(ready) = self.surface_gate.update(width, height, report) {
                let report_label = match report {
                    SurfaceReport::InitialConfig => "initial_config",
                    SurfaceReport::ConfigureEvent => "configure_event",
                };
                debug!(
                    surface_ready = ready,
                    width,
                    height,
                    report = report_label,
                    "viewer_surface_ready_state_changed"
                );
            }
            let ready = self.surface_gate.is_ready();
            // Detect stabilized size changes and purge stale queues/results
            if ready {
                let size_changed = match self.configured_surface_size {
                    Some((w, h)) => w != width || h != height,
                    None => true,
                };
                if size_changed {
                    self.configured_surface_size = Some((width, height));
                    self.on_surface_size_settled();
                }
            }
            self.surface_configured = ready;
            if !ready {
                self.pending_scene_enter = true;
            }
            ready
        }

        fn on_surface_size_settled(&mut self) {
            // Drop any precomputed canvases for the previous size and flush pending queue.
            self.ready_results.clear();
            if let Some(mode) = self.mode.as_mut() {
                let wake = mode.wake_mut();
                wake.set_next(None);
                wake.pending_mut().clear();
                wake.set_transition_state(None);
            }
            // We cannot cancel inflight matting; mismatched results will be dropped on upload.
        }

        fn with_active_scene<R>(
            &mut self,
            f: impl FnOnce(&mut dyn Scene, SceneContext<'_>) -> R,
        ) -> Option<R> {
            if !self.surface_configured {
                debug!("viewer_scene_waiting_for_surface_configuration");
                return None;
            }
            let window_handle = self.window.as_ref().map(Arc::clone);
            let window_ref = window_handle.as_deref();
            let mut request_redraw = {
                let window_handle = window_handle.clone();
                move || {
                    if let Some(window) = window_handle.as_ref() {
                        window.request_redraw();
                    }
                }
            };
            let config = Arc::clone(&self.full_config);
            let mut notify_displayed = {
                let sender = self.to_manager_displayed.clone();
                move |path: std::path::PathBuf| {
                    let _ = sender.try_send(Displayed(path));
                }
            };

            let mut mode = self.mode.take()?;
            let surface = self.active_surface();
            let mut bridge = MattingBridge {
                preload_count: self.preload_count,
                mat_inflight: &mut self.mat_inflight,
                deferred_images: &mut self.deferred_images,
                ready_results: &mut self.ready_results,
                from_loader: &mut self.from_loader,
                surface,
                matting: &self.matting,
                oversample: self.oversample,
                max_upscale_factor: self.max_upscale_factor,
                mat_pipeline: &self.mat_pipeline,
            };
            let mut enqueue_matting = move |wake: &mut scenes::WakeScene| {
                bridge.queue_for_wake(wake);
            };
            let rng = &mut self.rng;

            let result = mode.with_scene_mut(
                window_ref,
                config,
                &mut request_redraw,
                rng,
                &mut notify_displayed,
                &mut enqueue_matting,
                f,
            );
            self.mode = Some(mode);
            result
        }

        fn mode_kind(&self) -> ViewerModeKind {
            self.mode().kind()
        }

        fn set_mode(&mut self, target: ViewerModeKind) -> ViewerModeKind {
            let current = self.mode_kind();
            if current == target {
                return current;
            }

            let mut mode = self.mode.take().expect("viewer mode not initialized");

            self.dispatch_scene_hook(&mut mode, SceneHook::Exit);

            mode = mode.into_kind(target);

            self.dispatch_scene_hook(&mut mode, SceneHook::Enter);

            self.mode = Some(mode);
            current
        }

        fn dispatch_scene_hook(&mut self, mode: &mut ViewerMode, hook: SceneHook) {
            if !self.surface_configured {
                if matches!(hook, SceneHook::Enter) {
                    self.pending_scene_enter = true;
                }
                debug!(hook = ?hook, "viewer_scene_hook_deferred_until_surface_configured");
                return;
            }
            let window_handle = self.window.as_ref().map(Arc::clone);
            let window_ref = window_handle.as_deref();
            let mut request_redraw = {
                let window_handle = window_handle.clone();
                move || {
                    if let Some(window) = window_handle.as_ref() {
                        window.request_redraw();
                    }
                }
            };
            let config = Arc::clone(&self.full_config);
            let mut notify_displayed = {
                let sender = self.to_manager_displayed.clone();
                move |path: std::path::PathBuf| {
                    let _ = sender.try_send(Displayed(path));
                }
            };
            let surface = self.active_surface();
            let mut bridge = MattingBridge {
                preload_count: self.preload_count,
                mat_inflight: &mut self.mat_inflight,
                deferred_images: &mut self.deferred_images,
                ready_results: &mut self.ready_results,
                from_loader: &mut self.from_loader,
                surface,
                matting: &self.matting,
                oversample: self.oversample,
                max_upscale_factor: self.max_upscale_factor,
                mat_pipeline: &self.mat_pipeline,
            };
            let mut enqueue_matting = move |wake: &mut scenes::WakeScene| {
                bridge.queue_for_wake(wake);
            };
            let rng = &mut self.rng;
            let _ = mode.with_scene_mut(
                window_ref,
                config,
                &mut request_redraw,
                rng,
                &mut notify_displayed,
                &mut enqueue_matting,
                |scene, ctx| {
                    Self::run_scene_hook(scene, hook, ctx);
                },
            );
            if matches!(hook, SceneHook::Enter) {
                self.pending_scene_enter = false;
            }
        }

        fn run_scene_hook(scene: &mut dyn Scene, hook: SceneHook, ctx: SceneContext<'_>) {
            match hook {
                SceneHook::Enter => scene.enter(ctx),
                SceneHook::Exit => scene.exit(ctx),
            }
        }

        fn ensure_gpu_ready(&mut self, event_loop: &ActiveEventLoop, reason: &'static str) -> bool {
            let Some(window) = self.ensure_window(event_loop) else {
                debug!(context = reason, "viewer_gpu_ensure_no_window");
                return false;
            };
            let window_log = format!("{reason}_window_ready");
            self.log_event_loop_state(&window_log);

            if self.gpu.is_some() {
                debug!(context = reason, "viewer_gpu_ensure_already_initialized");
                return true;
            }

            // Honor wgpu's env overrides (notably WGPU_BACKEND=gl|vulkan) so
            // the rendering backend can be switched per deployment without a
            // rebuild. On the Pi the GL/EGL window-buffer path is the one the
            // desktop stack exercises daily and may be eligible for compositor
            // direct scanout where the v3dv Vulkan swapchain path is not.
            let instance = wgpu::Instance::new(&wgpu::InstanceDescriptor::from_env_or_default());
            debug!(context = reason, "viewer_gpu_instance_ready");
            let surface = match instance.create_surface(window.clone()) {
                Ok(surface) => {
                    debug!(context = reason, "viewer_gpu_surface_created");
                    surface
                }
                Err(err) => {
                    warn!(
                        context = reason,
                        error = %err,
                        "failed to create surface; exiting viewer"
                    );
                    event_loop.exit();
                    return false;
                }
            };
            let adapter =
                match pollster::block_on(instance.request_adapter(&wgpu::RequestAdapterOptions {
                    power_preference: wgpu::PowerPreference::HighPerformance,
                    compatible_surface: Some(&surface),
                    force_fallback_adapter: false,
                })) {
                    Ok(adapter) => {
                        let info = adapter.get_info();
                        debug!(context = reason, ?info, "viewer_gpu_adapter_acquired");
                        adapter
                    }
                    Err(err) => {
                        warn!(
                            context = reason,
                            error = %err,
                            "failed to acquire GPU adapter; exiting viewer"
                        );
                        event_loop.exit();
                        return false;
                    }
                };
            let limits = adapter.limits();
            debug!(
                context = reason,
                max_texture_dimension_2d = limits.max_texture_dimension_2d,
                max_buffer_size = limits.max_buffer_size,
                "viewer_gpu_limits"
            );
            let (device, queue) =
                match pollster::block_on(adapter.request_device(&wgpu::DeviceDescriptor {
                    label: Some("viewer-device"),
                    required_features: wgpu::Features::empty(),
                    required_limits: limits.clone(),
                    experimental_features: wgpu::ExperimentalFeatures::default(),
                    memory_hints: wgpu::MemoryHints::default(),
                    trace: wgpu::Trace::default(),
                })) {
                    Ok(pair) => {
                        debug!(context = reason, "viewer_gpu_device_ready");
                        pair
                    }
                    Err(err) => {
                        warn!(
                            context = reason,
                            error = %err,
                            "failed to acquire GPU device; exiting viewer"
                        );
                        event_loop.exit();
                        return false;
                    }
                };
            let caps = surface.get_capabilities(&adapter);
            let Some(format) = caps
                .formats
                .iter()
                .copied()
                .find(|f| f.is_srgb())
                .or_else(|| caps.formats.first().copied())
            else {
                warn!(
                    context = reason,
                    "surface reported no supported texture formats; exiting viewer"
                );
                event_loop.exit();
                return false;
            };
            // Prefer an opaque surface: the viewer always fills every pixel,
            // and an opaque fullscreen surface is what lets the compositor
            // skip blending — and, with matching formats, hand the buffer
            // straight to the display (direct scanout, no composite copy).
            let Some(alpha_mode) = caps
                .alpha_modes
                .iter()
                .copied()
                .find(|m| *m == wgpu::CompositeAlphaMode::Opaque)
                .or_else(|| caps.alpha_modes.first().copied())
            else {
                warn!(
                    context = reason,
                    "surface reported no alpha modes; exiting viewer"
                );
                event_loop.exit();
                return false;
            };
            let size = window.inner_size();
            debug!(
                context = reason,
                surface_width = size.width,
                surface_height = size.height,
                format = ?format,
                present_modes = ?caps.present_modes,
                "viewer_gpu_surface_caps"
            );
            // PHOTOFRAME_PRESENT_MODE=fifo|mailbox|immediate overrides the
            // presentation mode for frame-pacing experiments: fifo serializes
            // on the compositor's vsync cadence, mailbox lets the app render
            // ahead and the compositor latch the newest complete frame.
            let requested_present = std::env::var("PHOTOFRAME_PRESENT_MODE").ok();
            let present_mode = match requested_present.as_deref() {
                Some("fifo") => Some(wgpu::PresentMode::Fifo),
                Some("mailbox") => Some(wgpu::PresentMode::Mailbox),
                Some("immediate") => Some(wgpu::PresentMode::Immediate),
                Some(other) => {
                    warn!(
                        requested = other,
                        "unknown PHOTOFRAME_PRESENT_MODE; using auto-vsync"
                    );
                    None
                }
                None => None,
            };
            let present_mode = match present_mode {
                Some(mode) if caps.present_modes.contains(&mode) => {
                    info!(present_mode = ?mode, "viewer_present_mode_override");
                    mode
                }
                Some(mode) => {
                    warn!(
                        requested = ?mode,
                        supported = ?caps.present_modes,
                        "requested present mode unsupported; using auto-vsync"
                    );
                    wgpu::PresentMode::AutoVsync
                }
                None => {
                    // Default to mailbox when available: FIFO emulated over
                    // Wayland frame callbacks costs two vsyncs per frame on
                    // compositors without wp_fifo_v1 (measured: a bare clear
                    // locks at 30fps on a 60Hz output under sway 1.10),
                    // halving every transition. Mailbox latches the newest
                    // complete frame each vsync and paces normally.
                    if caps.present_modes.contains(&wgpu::PresentMode::Mailbox) {
                        info!("viewer_present_mode_default_mailbox");
                        wgpu::PresentMode::Mailbox
                    } else {
                        wgpu::PresentMode::AutoVsync
                    }
                }
            };
            let config = wgpu::SurfaceConfiguration {
                usage: wgpu::TextureUsages::RENDER_ATTACHMENT,
                format,
                width: size.width.max(1),
                height: size.height.max(1),
                present_mode,
                alpha_mode,
                view_formats: vec![],
                desired_maximum_frame_latency: 2,
            };
            // Resources for quad
            let uniform_buf = device.create_buffer(&wgpu::BufferDescriptor {
                label: Some("viewer-uniforms"),
                size: std::mem::size_of::<TransitionUniforms>() as u64,
                usage: wgpu::BufferUsages::UNIFORM | wgpu::BufferUsages::COPY_DST,
                mapped_at_creation: false,
            });
            let uniform_layout =
                device.create_bind_group_layout(&wgpu::BindGroupLayoutDescriptor {
                    label: Some("uniform-layout"),
                    entries: &[wgpu::BindGroupLayoutEntry {
                        binding: 0,
                        visibility: wgpu::ShaderStages::VERTEX_FRAGMENT,
                        ty: wgpu::BindingType::Buffer {
                            ty: wgpu::BufferBindingType::Uniform,
                            has_dynamic_offset: false,
                            min_binding_size: None,
                        },
                        count: None,
                    }],
                });
            let uniform_bind = device.create_bind_group(&wgpu::BindGroupDescriptor {
                label: Some("uniform-bind"),
                layout: &uniform_layout,
                entries: &[wgpu::BindGroupEntry {
                    binding: 0,
                    resource: uniform_buf.as_entire_binding(),
                }],
            });
            let img_bind_layout =
                device.create_bind_group_layout(&wgpu::BindGroupLayoutDescriptor {
                    label: Some("image-bind-layout"),
                    entries: &[
                        wgpu::BindGroupLayoutEntry {
                            binding: 0,
                            visibility: wgpu::ShaderStages::FRAGMENT,
                            ty: wgpu::BindingType::Texture {
                                sample_type: wgpu::TextureSampleType::Float { filterable: true },
                                view_dimension: wgpu::TextureViewDimension::D2,
                                multisampled: false,
                            },
                            count: None,
                        },
                        wgpu::BindGroupLayoutEntry {
                            binding: 1,
                            visibility: wgpu::ShaderStages::FRAGMENT,
                            ty: wgpu::BindingType::Sampler(wgpu::SamplerBindingType::Filtering),
                            count: None,
                        },
                    ],
                });
            let sampler = device.create_sampler(&wgpu::SamplerDescriptor {
                label: Some("linear-clamp"),
                address_mode_u: wgpu::AddressMode::ClampToEdge,
                address_mode_v: wgpu::AddressMode::ClampToEdge,
                address_mode_w: wgpu::AddressMode::ClampToEdge,
                mag_filter: wgpu::FilterMode::Linear,
                min_filter: wgpu::FilterMode::Linear,
                mipmap_filter: wgpu::FilterMode::Linear,
                ..Default::default()
            });
            let shader = device.create_shader_module(wgpu::ShaderModuleDescriptor {
                label: Some("viewer-quad"),
                source: wgpu::ShaderSource::Wgsl(std::borrow::Cow::Borrowed(include_str!(
                    "shaders/viewer_quad.wgsl"
                ))),
            });
            let pipeline_layout = device.create_pipeline_layout(&wgpu::PipelineLayoutDescriptor {
                label: Some("pipeline-layout"),
                bind_group_layouts: &[
                    &uniform_layout,
                    &img_bind_layout,
                    &img_bind_layout,
                    &img_bind_layout,
                ],
                push_constant_ranges: &[],
            });
            let iris_layer_pipeline_layout =
                device.create_pipeline_layout(&wgpu::PipelineLayoutDescriptor {
                    label: Some("iris-layer-pipeline-layout"),
                    bind_group_layouts: &[&uniform_layout],
                    push_constant_ranges: &[],
                });
            let iris_layer_pipeline =
                device.create_render_pipeline(&wgpu::RenderPipelineDescriptor {
                    label: Some("iris-layer-pipeline"),
                    layout: Some(&iris_layer_pipeline_layout),
                    vertex: wgpu::VertexState {
                        module: &shader,
                        entry_point: Some("vs_main"),
                        buffers: &[],
                        compilation_options: wgpu::PipelineCompilationOptions::default(),
                    },
                    primitive: wgpu::PrimitiveState::default(),
                    depth_stencil: None,
                    multisample: wgpu::MultisampleState::default(),
                    fragment: Some(wgpu::FragmentState {
                        module: &shader,
                        entry_point: Some("fs_iris_layer"),
                        targets: &[Some(wgpu::ColorTargetState {
                            // Must match the iris layer texture (Rgba16Float):
                            // dark petals band in 8-bit, see ensure_iris_layer.
                            format: wgpu::TextureFormat::Rgba16Float,
                            blend: None,
                            write_mask: wgpu::ColorWrites::ALL,
                        })],
                        compilation_options: wgpu::PipelineCompilationOptions::default(),
                    }),
                    multiview: None,
                    cache: None,
                });
            let blit_pipeline_layout =
                device.create_pipeline_layout(&wgpu::PipelineLayoutDescriptor {
                    label: Some("blit-pipeline-layout"),
                    bind_group_layouts: &[&uniform_layout, &img_bind_layout],
                    push_constant_ranges: &[],
                });
            let blit_pipeline = device.create_render_pipeline(&wgpu::RenderPipelineDescriptor {
                label: Some("blit-pipeline"),
                layout: Some(&blit_pipeline_layout),
                vertex: wgpu::VertexState {
                    module: &shader,
                    entry_point: Some("vs_main"),
                    buffers: &[],
                    compilation_options: wgpu::PipelineCompilationOptions::default(),
                },
                primitive: wgpu::PrimitiveState::default(),
                depth_stencil: None,
                multisample: wgpu::MultisampleState::default(),
                fragment: Some(wgpu::FragmentState {
                    module: &shader,
                    entry_point: Some("fs_blit"),
                    targets: &[Some(wgpu::ColorTargetState {
                        format,
                        blend: None,
                        write_mask: wgpu::ColorWrites::ALL,
                    })],
                    compilation_options: wgpu::PipelineCompilationOptions::default(),
                }),
                multiview: None,
                cache: None,
            });
            let pipeline = device.create_render_pipeline(&wgpu::RenderPipelineDescriptor {
                label: Some("quad-pipeline"),
                layout: Some(&pipeline_layout),
                vertex: wgpu::VertexState {
                    module: &shader,
                    entry_point: Some("vs_main"),
                    buffers: &[],
                    compilation_options: wgpu::PipelineCompilationOptions::default(),
                },
                primitive: wgpu::PrimitiveState::default(),
                depth_stencil: None,
                multisample: wgpu::MultisampleState::default(),
                fragment: Some(wgpu::FragmentState {
                    module: &shader,
                    entry_point: Some("fs_main"),
                    targets: &[Some(wgpu::ColorTargetState {
                        format,
                        // Opaque: the shader composites letterbox regions over
                        // U.background itself. Skipping blending avoids a
                        // destination read on every pixel (significant at 4K)
                        // and keeps the surface scanout-friendly.
                        blend: None,
                        write_mask: wgpu::ColorWrites::ALL,
                    })],
                    compilation_options: wgpu::PipelineCompilationOptions::default(),
                }),
                multiview: None,
                cache: None,
            });
            let make_plane = |label: &str, width: u32, height: u32, data: &[u8]| -> TexturePlane {
                let w = width.max(1);
                let h = height.max(1);
                let tex = device.create_texture(&wgpu::TextureDescriptor {
                    label: Some(label),
                    size: wgpu::Extent3d {
                        width: w,
                        height: h,
                        depth_or_array_layers: 1,
                    },
                    mip_level_count: 1,
                    sample_count: 1,
                    dimension: wgpu::TextureDimension::D2,
                    format: wgpu::TextureFormat::Rgba8UnormSrgb,
                    usage: wgpu::TextureUsages::TEXTURE_BINDING | wgpu::TextureUsages::COPY_DST,
                    view_formats: &[],
                });
                queue.write_texture(
                    wgpu::TexelCopyTextureInfo {
                        texture: &tex,
                        mip_level: 0,
                        origin: wgpu::Origin3d::ZERO,
                        aspect: wgpu::TextureAspect::All,
                    },
                    data,
                    wgpu::TexelCopyBufferLayout {
                        offset: 0,
                        bytes_per_row: Some(4 * w),
                        rows_per_image: Some(h),
                    },
                    wgpu::Extent3d {
                        width: w,
                        height: h,
                        depth_or_array_layers: 1,
                    },
                );
                let view = tex.create_view(&wgpu::TextureViewDescriptor::default());
                let bind = device.create_bind_group(&wgpu::BindGroupDescriptor {
                    label: Some(label),
                    layout: &img_bind_layout,
                    entries: &[
                        wgpu::BindGroupEntry {
                            binding: 0,
                            resource: wgpu::BindingResource::TextureView(&view),
                        },
                        wgpu::BindGroupEntry {
                            binding: 1,
                            resource: wgpu::BindingResource::Sampler(&sampler),
                        },
                    ],
                });
                TexturePlane { bind, w, h }
            };

            let blank_plane = make_plane("blank-texture", 1, 1, &[0, 0, 0, 255]);

            let greeting = GreetingScene::new(GreetingScreen::new(
                &device,
                &queue,
                format,
                self.full_config.greeting_screen.screen(),
            ));

            let sleep = SleepScene::new(GreetingScreen::new(
                &device,
                &queue,
                format,
                self.full_config.sleep_screen.screen(),
            ));

            if self.full_config.showcase.enabled && self.full_config.showcase.caption_enabled() {
                self.caption_overlay = Some(scenes::CaptionOverlay::new(&device, &queue, format));
            }
            self.window = Some(window);
            let gpu = GpuCtx {
                device,
                queue,
                surface,
                config,
                limits,
                uniform_buf,
                uniform_bind,
                img_bind_layout,
                sampler,
                pipeline,
                blank_plane,
                iris_layer_pipeline,
                iris_layer: None,
                blit_pipeline,
                half_target: None,
            };
            if let Some(mode) = self.mode.as_mut() {
                mode.set_overlays(Some(greeting), Some(sleep));
            }
            self.gpu = Some(gpu);
            self.surface_gate.reset();
            self.surface_gate.arm_for_initial_report();
            self.update_surface_ready(size.width, size.height, SurfaceReport::InitialConfig);
            self.pending_scene_enter = true;
            debug!(context = reason, "viewer_gpu_surface_configuration_pending");
            let wake = self.mode_mut().wake_mut();
            wake.set_current(None);
            wake.set_next(None);
            wake.set_transition_state(None);
            wake.set_displayed_at(None);
            let ready_log = format!("{reason}_gpu_ready");
            self.log_event_loop_state(&ready_log);
            true
        }

        fn reset_for_resume(&mut self) {
            self.mode_mut().wake_mut().reset();
            self.ready_results.clear();
            self.deferred_images.clear();
            if self.mode_kind() == ViewerModeKind::Sleep {
                self.mode_mut().wake_mut().take_redraw_needed();
                let _ = self.with_active_scene(|scene, ctx| {
                    scene.enter(ctx);
                });
            } else {
                self.enter_greeting();
            }
            self.mat_inflight = 0;
            self.surface_gate.reset();
            self.surface_configured = false;
            self.pending_scene_enter = true;
            self.surface_timeout_streak = 0;
            self.log_event_loop_state("reset_for_resume");
        }

        fn log_event_loop_state(&self, context: &str) {
            if !tracing::level_enabled!(Level::DEBUG) {
                return;
            }
            let now = Instant::now();
            let mode = self.mode();
            let wake = mode.wake();
            let current_path = wake.current().map(|img| img.path.display().to_string());
            let next_path = wake.next().map(|img| img.path.display().to_string());
            let displayed_elapsed_ms = wake
                .displayed_at()
                .map(|instant| now.saturating_duration_since(instant).as_millis() as u64);
            let transition_kind = wake.transition_state().map(TransitionState::kind);
            let transition_progress = wake.transition_state().map(TransitionState::progress);
            let greeting_pending = mode
                .greeting()
                .map(GreetingScene::needs_redraw)
                .unwrap_or(false);
            let sleep_pending = mode.sleep().map(SleepScene::needs_redraw).unwrap_or(false);

            debug!(
                context = context,
                viewer_mode = ?self.mode_kind(),
                has_window = self.window.is_some(),
                has_gpu = self.gpu.is_some(),
                surface_configured = self.surface_configured,
                pending_queue_len = wake.pending().len(),
                ready_results_len = self.ready_results.len(),
                deferred_queue_len = self.deferred_images.len(),
                mat_inflight = self.mat_inflight,
                preload_target = self.preload_count,
                pending_redraw = wake.needs_redraw(),
                greeting_overlay_pending = greeting_pending,
                sleep_overlay_pending = sleep_pending,
                displayed_elapsed_ms,
                current_path = current_path.as_deref(),
                next_path = next_path.as_deref(),
                transition_kind = ?transition_kind,
                transition_progress,
                has_next_stage = wake.next().is_some(),
                has_current_stage = wake.current().is_some(),
                "viewer_event_loop_state"
            );
        }

        fn ensure_window(&mut self, event_loop: &ActiveEventLoop) -> Option<Arc<Window>> {
            if let Some(window) = self.window.as_ref().cloned() {
                self.log_event_loop_state("ensure_window_cached");
                return Some(window);
            }

            let attrs = with_photo_app_id(Window::default_attributes().with_title("Photo Frame"));
            let window = match event_loop.create_window(attrs) {
                Ok(window) => Arc::new(window),
                Err(err) => {
                    warn!(error = %err, "failed to create viewer window; exiting");
                    event_loop.exit();
                    return None;
                }
            };
            window.set_decorations(false);
            let fullscreen_monitor = window
                .current_monitor()
                .or_else(|| event_loop.primary_monitor());
            window.set_fullscreen(Some(match fullscreen_monitor {
                Some(m) => Fullscreen::Borderless(Some(m)),
                None => Fullscreen::Borderless(None),
            }));
            window.set_cursor_visible(false);
            self.window = Some(window.clone());
            self.log_event_loop_state("ensure_window_created");
            Some(window)
        }

        fn teardown_gpu(&mut self) {
            let current_kind = self.mode_kind();
            {
                let mode = self.mode_mut();
                mode.wake_mut().reset();
                if current_kind == ViewerModeKind::Wake {
                    mode.wake_mut().mark_redraw_needed();
                }
                mode.set_overlays(None, None);
            }
            self.gpu = None;
            self.surface_gate.reset();
            self.surface_configured = false;
            self.pending_scene_enter = true;
            self.log_event_loop_state("teardown_gpu");
        }

        fn handle_control_command(&mut self, cmd: ViewerCommand) {
            debug!(command = ?cmd, "viewer_control_command");
            match cmd {
                ViewerCommand::SetState(ControlViewerState::Awake) => self.enter_wake(),
                ViewerCommand::SetState(ControlViewerState::Asleep) => self.enter_sleep(),
                ViewerCommand::ToggleState => match self.mode_kind() {
                    ViewerModeKind::Sleep => self.enter_wake(),
                    ViewerModeKind::Greeting | ViewerModeKind::Wake => self.enter_sleep(),
                },
            }
        }

        fn process_tick(&mut self, event_loop: &ActiveEventLoop) {
            self.log_event_loop_state("process_tick_start");
            if self.cancel.is_cancelled() {
                event_loop.exit();
                return;
            }

            // Keep surface configuration and readiness in sync even if winit
            // doesn't deliver an explicit resize event (Wayland/Sway can do this).
            self.refresh_surface_config_from_window();
            if self.surface_configured && self.pending_scene_enter {
                self.pending_scene_enter = false;
                let _ = self.with_active_scene(|scene, ctx| {
                    scene.enter(ctx);
                });
            }

            self.drain_mat_results();

            let mode_kind = self.mode_kind();
            if !matches!(mode_kind, ViewerModeKind::Sleep)
                && let Some(mut mode) = self.mode.take()
            {
                {
                    let wake = mode.wake_mut();
                    self.upload_ready_results_for_wake(wake);
                    self.queue_mat_tasks_for_wake(wake);
                }
                self.mode = Some(mode);
            }

            let _ = self.with_active_scene(|scene, ctx| {
                scene.process_tick(ctx);
            });
            self.log_event_loop_state("process_tick_end");
        }

        fn refresh_surface_config_from_window(&mut self) {
            let (Some(window), Some(gpu)) = (self.window.as_ref(), self.gpu.as_mut()) else {
                return;
            };
            let size = window.inner_size();
            if size.width == 0 || size.height == 0 {
                gpu.config.width = 0;
                gpu.config.height = 0;
                self.surface_gate.arm_for_initial_report();
                let _ = self.update_surface_ready(0, 0, SurfaceReport::ConfigureEvent);
                return;
            }
            if gpu.config.width != size.width || gpu.config.height != size.height {
                gpu.config.width = size.width;
                gpu.config.height = size.height;
                gpu.surface.configure(&gpu.device, &gpu.config);
            }
            let _ =
                self.update_surface_ready(size.width, size.height, SurfaceReport::ConfigureEvent);
        }

        fn drain_mat_results(&mut self) {
            while let Some(result) = self.mat_pipeline.try_recv() {
                self.mat_inflight = self.mat_inflight.saturating_sub(1);
                if result.priority {
                    self.ready_results
                        .retain(|existing| existing.path != result.path);
                }
                self.ready_results.push_back(result);
            }
        }

        fn upload_ready_results_for_wake(&mut self, wake: &mut scenes::WakeScene) {
            if self.gpu.is_none() {
                return;
            }
            // Defer non-priority uploads while a transition is animating:
            // pushing a multi-megapixel canvas through the queue contends
            // with transition rendering and shows up as multi-frame hitches.
            // Dwell time is long, so deferred uploads resume on the first
            // tick after the transition completes.
            if wake.transition_state().is_some() {
                let mut deferred = VecDeque::with_capacity(self.ready_results.len());
                let mut priority_now = VecDeque::new();
                for result in self.ready_results.drain(..) {
                    if result.priority {
                        priority_now.push_back(result);
                    } else {
                        deferred.push_back(result);
                    }
                }
                // Priority results (operator-requested) still upload
                // immediately; everything else waits out the animation.
                self.ready_results = priority_now;
                if !self.ready_results.is_empty() {
                    self.upload_results_now(wake);
                }
                self.ready_results = deferred;
                return;
            }
            self.upload_results_now(wake);
        }

        fn upload_results_now(&mut self, wake: &mut scenes::WakeScene) {
            let gpu = self.gpu.as_ref().unwrap();
            let expected = compute_canvas_size(
                gpu.config.width,
                gpu.config.height,
                self.oversample,
                gpu.limits.max_texture_dimension_2d,
            );

            while let Some(result) = self.ready_results.pop_front() {
                let path = result.path.clone();
                let priority = result.priority;
                // Discard canvases that were prepared for a different surface size.
                if result.canvas.width != expected.0 || result.canvas.height != expected.1 {
                    debug!(
                        path = %path.display(),
                        canvas_w = result.canvas.width,
                        canvas_h = result.canvas.height,
                        expected_w = expected.0,
                        expected_h = expected.1,
                        "dropping_mismatched_canvas_after_resize"
                    );
                    continue;
                }
                if let Some(new_tex) = upload_mat_result(gpu, result) {
                    if priority {
                        let replace_next = wake.next().is_some_and(|stage| stage.path == path);
                        wake.pending_mut().retain(|queued| queued.path != path);
                        if replace_next && let Some(stage) = wake.take_next() {
                            wake.pending_mut().push_front(stage);
                        }
                        wake.pending_mut().push_front(new_tex);
                    } else {
                        wake.pending_mut().push_back(new_tex);
                    }
                    debug!(
                        path = %path.display(),
                        priority,
                        depth = wake.pending().len(),
                        "queued_image"
                    );
                }
            }
        }

        fn queue_mat_tasks_for_wake(&mut self, wake: &mut scenes::WakeScene) {
            // `queue_for_wake` defers work until the surface reports a usable size.
            // Once `WindowEvent::Resized` updates `self.gpu.config`, the next tick will
            // call this helper again and retry automatically.
            let surface = self.active_surface();
            let mut bridge = MattingBridge {
                preload_count: self.preload_count,
                mat_inflight: &mut self.mat_inflight,
                deferred_images: &mut self.deferred_images,
                ready_results: &mut self.ready_results,
                from_loader: &mut self.from_loader,
                surface,
                matting: &self.matting,
                oversample: self.oversample,
                max_upscale_factor: self.max_upscale_factor,
                mat_pipeline: &self.mat_pipeline,
            };
            bridge.queue_for_wake(wake);
        }

        fn enter_sleep(&mut self) {
            if self.mode_kind() == ViewerModeKind::Sleep {
                return;
            }
            info!("viewer: entering sleep");
            self.mode_mut().wake_mut().take_redraw_needed();
            self.set_mode(ViewerModeKind::Sleep);
            self.log_event_loop_state("enter_sleep");
        }

        fn enter_wake(&mut self) {
            if self.mode_kind() == ViewerModeKind::Wake {
                return;
            }
            info!("viewer: entering wake");
            self.set_mode(ViewerModeKind::Wake);
            self.log_event_loop_state("enter_wake");
        }

        fn enter_greeting(&mut self) {
            if self.mode_kind() != ViewerModeKind::Greeting {
                info!("viewer: entering greeting");
            }
            self.mode_mut().wake_mut().take_redraw_needed();
            self.set_mode(ViewerModeKind::Greeting);
            self.log_event_loop_state("enter_greeting");
        }

        fn handle_surface_timeout(&mut self, event_loop: &ActiveEventLoop) {
            const MAX_CONSECUTIVE_TIMEOUTS: u32 = 6;

            self.surface_timeout_streak = self.surface_timeout_streak.saturating_add(1);
            if self.surface_timeout_streak < MAX_CONSECUTIVE_TIMEOUTS {
                return;
            }

            warn!(
                streak = self.surface_timeout_streak,
                "viewer_surface_timeout_recovering"
            );
            self.surface_timeout_streak = 0;

            self.teardown_gpu();
            self.reset_for_resume();
            if self.ensure_gpu_ready(event_loop, "surface_timeout_recover") {
                debug!("viewer_surface_timeout_recovered");
            }
        }

        fn record_frame_presented(&mut self) {
            self.surface_timeout_streak = 0;
        }

        /// Track per-frame cadence while a transition plays; log a summary
        /// once it ends (or hands over to a different transition kind).
        fn note_transition_frame(&mut self, active: Option<TransitionKind>) {
            let now = Instant::now();
            let metrics = self.full_config.metrics;
            match (self.transition_frame_metric.take(), active) {
                (None, Some(kind)) => {
                    self.transition_frame_metric = Some(TransitionFrameMetric::begin(kind, now));
                }
                (Some(mut stats), Some(kind)) if stats.kind == kind => {
                    let dt_ms = now.duration_since(stats.last_frame).as_secs_f32() * 1000.0;
                    stats.worst_frame_ms = stats.worst_frame_ms.max(dt_ms);
                    stats.best_frame_ms = stats.best_frame_ms.min(dt_ms);
                    stats.frames += 1;
                    stats.last_frame = now;
                    self.transition_frame_metric = Some(stats);
                }
                (Some(stats), Some(kind)) => {
                    stats.log(metrics);
                    self.transition_frame_metric = Some(TransitionFrameMetric::begin(kind, now));
                }
                (Some(stats), None) => stats.log(metrics),
                (None, None) => {}
            }
        }
    }

    impl ApplicationHandler<ViewerEvent> for App {
        fn resumed(&mut self, event_loop: &ActiveEventLoop) {
            debug!("viewer_app_resumed");
            self.reset_for_resume();
            self.log_event_loop_state("resumed_post_reset");

            let _ = self.ensure_gpu_ready(event_loop, "resumed");
        }

        fn suspended(&mut self, _event_loop: &ActiveEventLoop) {
            debug!("viewer_app_suspended");
            self.teardown_gpu();
        }

        fn window_event(
            &mut self,
            event_loop: &ActiveEventLoop,
            window_id: WindowId,
            event: WindowEvent,
        ) {
            let Some(window) = self.window.as_ref().cloned() else {
                return;
            };
            if window.id() != window_id {
                return;
            }
            self.log_event_loop_state("window_event_pre");
            match event {
                WindowEvent::CloseRequested => {
                    debug!("viewer_window_close_requested");
                    event_loop.exit();
                }
                WindowEvent::Resized(new_size) => {
                    if let Some(gpu) = self.gpu.as_mut() {
                        debug!(
                            width = new_size.width,
                            height = new_size.height,
                            "viewer_window_resized"
                        );
                        if new_size.width == 0 || new_size.height == 0 {
                            gpu.config.width = 0;
                            gpu.config.height = 0;
                            self.surface_gate.arm_for_initial_report();
                            self.update_surface_ready(
                                new_size.width,
                                new_size.height,
                                SurfaceReport::ConfigureEvent,
                            );
                            debug!("viewer_surface_configuration_waiting_for_non_zero_size");
                            return;
                        }
                        gpu.config.width = new_size.width;
                        gpu.config.height = new_size.height;
                        gpu.surface.configure(&gpu.device, &gpu.config);
                        let ready = self.update_surface_ready(
                            new_size.width,
                            new_size.height,
                            SurfaceReport::ConfigureEvent,
                        );
                        if ready && self.pending_scene_enter {
                            self.pending_scene_enter = false;
                            let _ = self.with_active_scene(|scene, ctx| {
                                scene.enter(ctx);
                            });
                        }
                        if ready {
                            if let Some(cap) = self.caption_overlay.as_mut() {
                                cap.resize(new_size);
                            }
                            let scale_factor = window.scale_factor();
                            let _ = self.with_active_scene(|scene, ctx| {
                                scene.handle_resize(ctx, new_size, scale_factor);
                            });
                        } else {
                            debug!(
                                width = new_size.width,
                                height = new_size.height,
                                "viewer_surface_configuration_waiting_for_expectation"
                            );
                        }
                    } else {
                        self.surface_gate.reset();
                        self.surface_configured = false;
                        self.pending_scene_enter = true;
                    }
                }
                WindowEvent::ScaleFactorChanged {
                    mut inner_size_writer,
                    ..
                } => {
                    if let Some(gpu) = self.gpu.as_mut() {
                        let scale_factor = window.scale_factor();
                        let size = window.inner_size();
                        debug!(
                            scale_factor = scale_factor,
                            width = size.width,
                            height = size.height,
                            "viewer_window_scale_factor_changed"
                        );
                        let _ = inner_size_writer.request_inner_size(size);
                        if size.width == 0 || size.height == 0 {
                            gpu.config.width = 0;
                            gpu.config.height = 0;
                            self.surface_gate.arm_for_initial_report();
                            self.update_surface_ready(
                                size.width,
                                size.height,
                                SurfaceReport::ConfigureEvent,
                            );
                            debug!("viewer_surface_configuration_waiting_for_non_zero_size");
                            return;
                        }
                        gpu.config.width = size.width;
                        gpu.config.height = size.height;
                        gpu.surface.configure(&gpu.device, &gpu.config);
                        let ready = self.update_surface_ready(
                            size.width,
                            size.height,
                            SurfaceReport::ConfigureEvent,
                        );
                        if ready && self.pending_scene_enter {
                            self.pending_scene_enter = false;
                            let _ = self.with_active_scene(|scene, ctx| {
                                scene.enter(ctx);
                            });
                        }
                        if ready {
                            let _ = self.with_active_scene(|scene, ctx| {
                                scene.handle_scale_factor_changed(ctx, size, scale_factor);
                            });
                        } else {
                            debug!(
                                width = size.width,
                                height = size.height,
                                "viewer_surface_configuration_waiting_for_expectation"
                            );
                        }
                    }
                }
                WindowEvent::Occluded(false) => {
                    debug!("viewer_window_occluded_false");
                    let _ = self.with_active_scene(|scene, ctx| {
                        scene.handle_visibility(ctx, true);
                    });
                }
                WindowEvent::Occluded(true) => {
                    debug!("viewer_window_occluded_true");
                }
                WindowEvent::RedrawRequested => {
                    let mode_kind = self.mode_kind();
                    let Some(_) = self.gpu.as_ref() else {
                        return;
                    };
                    if !self.surface_configured {
                        debug!("viewer_redraw_waiting_for_surface_configuration");
                        return;
                    }
                    let overlay_pending = match mode_kind {
                        ViewerModeKind::Greeting => self
                            .mode()
                            .greeting()
                            .map(GreetingScene::needs_redraw)
                            .unwrap_or(false),
                        ViewerModeKind::Sleep => self
                            .mode()
                            .sleep()
                            .map(SleepScene::needs_redraw)
                            .unwrap_or(false),
                        ViewerModeKind::Wake => false,
                    };
                    let (pending_redraw, queue_depth, has_transition) = {
                        let wake = self.mode().wake();
                        (
                            wake.needs_redraw(),
                            wake.pending().len(),
                            wake.transition_state().is_some(),
                        )
                    };
                    debug!(
                        viewer_mode = ?mode_kind,
                        overlay_pending,
                        pending_redraw,
                        queue_depth,
                        ready_results = self.ready_results.len(),
                        mat_inflight = self.mat_inflight,
                        has_transition,
                        "viewer_window_redraw_requested"
                    );
                    if matches!(mode_kind, ViewerModeKind::Greeting | ViewerModeKind::Sleep)
                        && !overlay_pending
                    {
                        return;
                    }
                    if matches!(mode_kind, ViewerModeKind::Greeting | ViewerModeKind::Sleep) {
                        let size = window.inner_size();
                        let scale_factor = window.scale_factor();
                        let layout_ready = {
                            let Some(mode) = self.mode.as_mut() else {
                                return;
                            };
                            match mode_kind {
                                ViewerModeKind::Greeting => {
                                    if let Some(screen) = mode.greeting_mut() {
                                        let message = self
                                            .full_config
                                            .greeting_screen
                                            .screen()
                                            .message_or_default()
                                            .into_owned();
                                        screen.resize(size, scale_factor);
                                        screen.set_message(message);
                                        screen.ensure_layout_ready()
                                    } else {
                                        false
                                    }
                                }
                                ViewerModeKind::Sleep => {
                                    if let Some(screen) = mode.sleep_mut() {
                                        let message = self
                                            .full_config
                                            .sleep_screen
                                            .screen()
                                            .message_or_default()
                                            .into_owned();
                                        screen.resize(size, scale_factor);
                                        screen.set_message(message);
                                        screen.ensure_layout_ready()
                                    } else {
                                        false
                                    }
                                }
                                ViewerModeKind::Wake => true,
                            }
                        };
                        if !layout_ready {
                            debug!(
                                viewer_mode = ?mode_kind,
                                width = size.width,
                                height = size.height,
                                "viewer_overlay_waiting_for_layout"
                            );
                            return;
                        }
                    }

                    let mut frame = None;
                    let mut encountered_timeout = false;
                    let mut need_scene_enter = false;
                    for attempt in 0..2 {
                        let surface_result = {
                            let Some(gpu) = self.gpu.as_mut() else {
                                return;
                            };
                            gpu.surface.get_current_texture()
                        };
                        match surface_result {
                            Ok(current) => {
                                frame = Some(current);
                                break;
                            }
                            Err(err) => match err {
                                wgpu::SurfaceError::Lost | wgpu::SurfaceError::Outdated => {
                                    let size = window.inner_size();
                                    warn!(
                                        attempt = attempt,
                                        error = ?err,
                                        width = size.width,
                                        height = size.height,
                                        "viewer_surface_reconfigure"
                                    );
                                    if size.width == 0 || size.height == 0 {
                                        if let Some(gpu) = self.gpu.as_mut() {
                                            gpu.config.width = 0;
                                            gpu.config.height = 0;
                                        }
                                        self.surface_gate.arm_for_initial_report();
                                        self.update_surface_ready(
                                            size.width,
                                            size.height,
                                            SurfaceReport::ConfigureEvent,
                                        );
                                        break;
                                    }
                                    if let Some(gpu) = self.gpu.as_mut() {
                                        gpu.config.width = size.width;
                                        gpu.config.height = size.height;
                                        gpu.surface.configure(&gpu.device, &gpu.config);
                                    } else {
                                        return;
                                    }
                                    let ready = self.update_surface_ready(
                                        size.width,
                                        size.height,
                                        SurfaceReport::ConfigureEvent,
                                    );
                                    if ready && self.pending_scene_enter {
                                        need_scene_enter = true;
                                    }
                                    if !ready {
                                        break;
                                    }
                                    if attempt == 0 {
                                        continue;
                                    } else {
                                        break;
                                    }
                                }
                                wgpu::SurfaceError::Timeout => {
                                    warn!("viewer_surface_timeout");
                                    encountered_timeout = true;
                                    if attempt == 0 {
                                        continue;
                                    } else {
                                        break;
                                    }
                                }
                                wgpu::SurfaceError::OutOfMemory => {
                                    warn!("viewer_surface_out_of_memory");
                                    event_loop.exit();
                                    return;
                                }
                                wgpu::SurfaceError::Other => {
                                    warn!(?err, "viewer_surface_error");
                                    return;
                                }
                            },
                        }
                    }
                    if need_scene_enter {
                        self.pending_scene_enter = false;
                        let _ = self.with_active_scene(|scene, ctx| {
                            scene.enter(ctx);
                        });
                        if !self.surface_configured {
                            return;
                        }
                    }
                    let Some(frame) = frame else {
                        if encountered_timeout {
                            self.handle_surface_timeout(event_loop);
                        }
                        return;
                    };
                    let (Some(gpu), Some(mode)) = (self.gpu.as_mut(), self.mode.as_mut()) else {
                        return;
                    };
                    let view = frame
                        .texture
                        .create_view(&wgpu::TextureViewDescriptor::default());
                    let mut encoder =
                        gpu.device
                            .create_command_encoder(&wgpu::CommandEncoderDescriptor {
                                label: Some("draw-encoder"),
                            });

                    match mode_kind {
                        ViewerModeKind::Sleep => {
                            let Some(screen) = mode.sleep_mut() else {
                                return;
                            };
                            encoder.push_debug_group("sleep-banner");
                            let rendered = screen.render(&mut encoder, &view);
                            encoder.pop_debug_group();

                            if !rendered {
                                debug!("sleep_banner_render_deferred");
                                return;
                            }

                            gpu.queue.submit(Some(encoder.finish()));
                            frame.present();
                            screen.after_submit();
                            self.record_frame_presented();
                        }
                        ViewerModeKind::Greeting => {
                            let Some(screen) = mode.greeting_mut() else {
                                return;
                            };
                            encoder.push_debug_group("greeting-banner");
                            let rendered = screen.render(&mut encoder, &view);
                            encoder.pop_debug_group();

                            if !rendered {
                                debug!("greeting_banner_render_deferred");
                                return;
                            }

                            gpu.queue.submit(Some(encoder.finish()));
                            frame.present();
                            screen.after_submit();
                            self.record_frame_presented();
                        }
                        ViewerModeKind::Wake => {
                            let wake = mode.wake_mut();
                            encoder.push_debug_group("wake-draw");
                            // Created up front: later code holds immutable
                            // borrows of gpu for the bind groups.
                            if let Some(kind) = wake.transition_state().map(|s| s.kind()) {
                                if transition_scale() > 1 {
                                    gpu.ensure_half_target();
                                }
                                if kind == TransitionKind::Iris {
                                    gpu.ensure_iris_layer();
                                }
                            }
                            let screen_w = gpu.config.width as f32;
                            let screen_h = gpu.config.height as f32;
                            let mut uniforms = TransitionUniforms {
                                screen_size: [screen_w, screen_h],
                                progress: 0.0,
                                kind: 0,
                                current_dest: [0.0; 4],
                                next_dest: [0.0; 4],
                                params0: [0.0; 4],
                                params1: [0.0; 4],
                                params3: [0.0; 4],
                                background: [
                                    self.clear_color.r as f32,
                                    self.clear_color.g as f32,
                                    self.clear_color.b as f32,
                                    1.0,
                                ],
                                petals_a: [[0.0; 4]; 16],
                                petals_b: [[0.0; 4]; 16],
                            };
                            let mut current_bind = &gpu.blank_plane.bind;
                            let mut next_bind = &gpu.blank_plane.bind;
                            let mut have_current = false;
                            let mut have_next = false;

                            if let Some(cur) = wake.current() {
                                let rect = compute_cover_rect(
                                    cur.plane.w,
                                    cur.plane.h,
                                    gpu.config.width,
                                    gpu.config.height,
                                );
                                uniforms.current_dest = rect_to_uniform(rect);
                                current_bind = &cur.plane.bind;
                                have_current = true;
                            }
                            if let Some(next) = wake.next() {
                                let rect = compute_cover_rect(
                                    next.plane.w,
                                    next.plane.h,
                                    gpu.config.width,
                                    gpu.config.height,
                                );
                                uniforms.next_dest = rect_to_uniform(rect);
                                next_bind = &next.plane.bind;
                                have_next = true;
                            }

                            let active_transition =
                                wake.transition_state().map(|state| state.kind());
                            let mut should_draw_quad = false;
                            let debug_bezier = std::env::var("PHOTOFRAME_DEBUG_BEZIER")
                                .map(|s| matches!(s.as_str(), "1" | "true" | "yes" | "on"))
                                .unwrap_or(false);
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
