vincentl/rust-photo-frame/crates/wifi-manager/src/config.rs

use anyhow::{Context, Result};
use serde::Deserialize;
use std::fs;
use std::net::Ipv4Addr;
use std::path::{Path, PathBuf};

#[derive(Debug, Clone, Deserialize)]
#[serde(rename_all = "kebab-case")]
pub struct Config {
    #[serde(default = "default_interface")]
    pub interface: String,
    #[serde(default = "default_check_interval")]
    pub check_interval_sec: u64,
    #[serde(default = "default_offline_grace")]
    pub offline_grace_sec: u64,
    #[serde(default = "default_recovery_mode")]
    pub recovery_mode: RecoveryMode,
    #[serde(default = "default_recovery_reconnect_probe")]
    pub recovery_reconnect_probe_sec: u64,
    #[serde(default = "default_recovery_connect_timeout")]
    pub recovery_connect_timeout_sec: u64,
    #[serde(default = "default_wordlist_path")]
    pub wordlist_path: PathBuf,
    #[serde(default = "default_var_dir")]
    pub var_dir: PathBuf,
    #[serde(default)]
    pub hotspot: HotspotConfig,
    #[serde(default)]
    pub ui: UiConfig,
    #[serde(default)]
    pub photo_app: PhotoAppConfig,
    #[serde(default)]
    pub overlay: OverlayConfig,
}

#[derive(Debug, Clone, Copy, Deserialize, PartialEq, Eq)]
#[serde(rename_all = "kebab-case")]
pub enum RecoveryMode {
    AppHandoff,
    Overlay,
}

#[derive(Debug, Clone, Deserialize)]
#[serde(rename_all = "kebab-case")]
pub struct HotspotConfig {
    #[serde(default = "default_hotspot_connection_id")]
    pub connection_id: String,
    #[serde(default = "default_hotspot_ssid")]
    pub ssid: String,
    #[serde(default = "default_hotspot_ip")]
    pub ipv4_addr: Ipv4Addr,
}

#[derive(Debug, Clone, Deserialize)]
#[serde(rename_all = "kebab-case")]
pub struct UiConfig {
    /// Address the portal listener binds to.  When unset, the UI binds to the
    /// hotspot's `ipv4_addr` so it is reachable only on the recovery AP and
    /// never on the home LAN (see `run_ui`).  Set explicitly (e.g. `0.0.0.0`)
    /// only for local testing.
    #[serde(default)]
    pub bind_address: Option<String>,
    #[serde(default = "default_ui_port")]
    pub port: u16,
}

#[derive(Debug, Clone, Deserialize)]
#[serde(rename_all = "kebab-case")]
pub struct PhotoAppConfig {
    #[serde(default = "default_photo_app_launch_command")]
    pub launch_command: Vec<String>,
    #[serde(default = "default_photo_app_id")]
    pub app_id: String,
}

#[derive(Debug, Clone, Deserialize)]
#[serde(rename_all = "kebab-case")]
pub struct OverlayConfig {
    #[serde(default = "default_overlay_command")]
    pub command: Vec<String>,
    #[serde(default = "default_photo_app_id")]
    pub photo_app_id: String,
    #[serde(default = "default_overlay_app_id")]
    pub overlay_app_id: String,
    #[serde(default)]
    pub sway_socket: Option<PathBuf>,
}

impl Config {
    pub fn load(path: &Path) -> Result<Self> {
        let data = fs::read(path)
            .with_context(|| format!("failed to read config at {}", path.display()))?;
        let cfg: Config = serde_yaml::from_slice(&data)
            .with_context(|| format!("failed to parse config at {}", path.display()))?;
        Ok(cfg)
    }
}

impl Default for HotspotConfig {
    fn default() -> Self {
        Self {
            connection_id: default_hotspot_connection_id(),
            ssid: default_hotspot_ssid(),
            ipv4_addr: default_hotspot_ip(),
        }
    }
}

impl Default for UiConfig {
    fn default() -> Self {
        Self {
            bind_address: None,
            port: default_ui_port(),
        }
    }
}

impl Default for PhotoAppConfig {
    fn default() -> Self {
        Self {
            launch_command: default_photo_app_launch_command(),
            app_id: default_photo_app_id(),
        }
    }
}

impl Default for OverlayConfig {
    fn default() -> Self {
        Self {
            command: default_overlay_command(),
            photo_app_id: default_photo_app_id(),
            overlay_app_id: default_overlay_app_id(),
            sway_socket: None,
        }
    }
}

fn default_interface() -> String {
    "wlan0".to_string()
}

fn default_check_interval() -> u64 {
    5
}

fn default_offline_grace() -> u64 {
    30
}

fn default_recovery_mode() -> RecoveryMode {
    RecoveryMode::AppHandoff
}

fn default_recovery_reconnect_probe() -> u64 {
    // 5 minutes between probes.  The probe tears down the AP (kicking any
    // connected phone off), so we want it infrequent.  The AP-client guard in
    // watch.rs provides the primary protection; this interval is the fallback.
    300
}

fn default_recovery_connect_timeout() -> u64 {
    20
}

fn default_wordlist_path() -> PathBuf {
    PathBuf::from("/opt/photoframe/share/wordlist.txt")
}

fn default_var_dir() -> PathBuf {
    PathBuf::from("/var/lib/photoframe")
}

fn default_hotspot_connection_id() -> String {
    "pf-hotspot".to_string()
}

fn default_hotspot_ssid() -> String {
    "PhotoFrame-Setup".to_string()
}

fn default_hotspot_ip() -> Ipv4Addr {
    Ipv4Addr::new(192, 168, 4, 1)
}

fn default_ui_port() -> u16 {
    8080
}

fn default_photo_app_launch_command() -> Vec<String> {
    vec![
        "/usr/local/bin/photoframe".to_string(),
        "/etc/photoframe/config.yaml".to_string(),
    ]
}

fn default_overlay_command() -> Vec<String> {
    // Launch overlay via sway so it inherits the session Wayland environment.
    // The watcher will construct a single exec command line with arguments.
    vec!["swaymsg".to_string()]
}

fn default_photo_app_id() -> String {
    "photoframe".to_string()
}

fn default_overlay_app_id() -> String {
    "wifi-overlay".to_string()
}

#[cfg(test)]
mod tests {
    use super::{Config, RecoveryMode};

    #[test]
    fn defaults_include_recovery_settings() {
        let cfg: Config = serde_yaml::from_str("{}").expect("parse config");
        assert_eq!(cfg.recovery_mode, RecoveryMode::AppHandoff);
        assert_eq!(cfg.recovery_reconnect_probe_sec, 300);
        assert_eq!(cfg.recovery_connect_timeout_sec, 20);
        assert_eq!(cfg.photo_app.app_id, "photoframe");
        assert_eq!(
            cfg.photo_app.launch_command,
            vec![
                "/usr/local/bin/photoframe".to_string(),
                "/etc/photoframe/config.yaml".to_string()
            ]
        );
    }

    #[test]
    fn parses_overlay_recovery_mode() {
        let cfg: Config = serde_yaml::from_str(
            r#"
recovery-mode: overlay
recovery-reconnect-probe-sec: 90
recovery-connect-timeout-sec: 25
photo-app:
  app-id: custom-photo
  launch-command:
    - /opt/custom/photo
    - /etc/custom.yaml
"#,
        )
        .expect("parse config");
        assert_eq!(cfg.recovery_mode, RecoveryMode::Overlay);
        assert_eq!(cfg.recovery_reconnect_probe_sec, 90);
        assert_eq!(cfg.recovery_connect_timeout_sec, 25);
        assert_eq!(cfg.photo_app.app_id, "custom-photo");
        assert_eq!(
            cfg.photo_app.launch_command,
            vec![
                "/opt/custom/photo".to_string(),
                "/etc/custom.yaml".to_string()
            ]
        );
    }
}
