vincentl/rust-photo-frame/crates/photoframe/src/tasks/loader.rs

use crate::events::{InvalidPhoto, LoadPhoto, PhotoLoaded, PreparedImageCpu};
use anyhow::Result;
use std::collections::BTreeMap;
use std::fs::File;
use std::io::{BufReader, Seek};
use std::path::{Path, PathBuf};
use tokio::select;
use tokio::sync::mpsc::{Receiver, Sender};
use tokio::task::JoinSet;
use tokio_util::sync::CancellationToken;
use tracing::debug;

/// Upper bound on peak allocation while decoding a single image. On a
/// memory-constrained Pi a pathological image (e.g. a multi-gigapixel scan or
/// panorama) could otherwise OOM-kill the whole process. ~512 MiB comfortably
/// covers >100 MP photos while rejecting absurd inputs; an over-limit image
/// surfaces as a normal decode error and is skipped (never deleted).
const MAX_DECODE_ALLOC_BYTES: u64 = 512 * 1024 * 1024;

// Decodes an image to RGBA8 and applies EXIF orientation if available.
// Note: Orientation handling is a best-effort; if metadata is missing, the original
// orientation is preserved. The file is opened only once: EXIF is read first, then
// the reader is seeked back to the start for image decoding.
fn decode_rgba8_apply_exif(path: &Path) -> anyhow::Result<image::RgbaImage> {
    let file = File::open(path)?;
    let mut buf = BufReader::new(file);

    // Read EXIF orientation from the already-open handle.
    let orientation: u16 = (|| -> Option<u16> {
        let exif = exif::Reader::new().read_from_container(&mut buf).ok()?;
        let field = exif.get_field(exif::Tag::Orientation, exif::In::PRIMARY)?;
        let val = field.value.get_uint(0)? as u16;
        debug!("exif orientation {} for {}", val, path.display());
        Some(val)
    })()
    .unwrap_or(1);

    // Seek back to the start so the image decoder reads from the beginning.
    buf.seek(std::io::SeekFrom::Start(0))?;

    let mut reader = image::ImageReader::new(buf).with_guessed_format()?;
    let mut limits = image::Limits::default();
    limits.max_alloc = Some(MAX_DECODE_ALLOC_BYTES);
    reader.limits(limits);
    let mut img = reader.decode()?.to_rgba8();

    // Map common EXIF orientations. Unsupported cases fall through as-is.
    match orientation {
        1 => {}
        2 => {
            // horizontal flip
            img = image::imageops::flip_horizontal(&img);
        }
        3 => {
            img = image::imageops::rotate180(&img);
        }
        4 => {
            // vertical flip
            img = image::imageops::flip_vertical(&img);
        }
        5 => {
            // transpose (flip diag): rotate90 + flip_horizontal
            img = image::imageops::rotate90(&img);
            img = image::imageops::flip_horizontal(&img);
        }
        6 => {
            // rotate 90 CW
            img = image::imageops::rotate90(&img);
        }
        7 => {
            // transverse: rotate270 + flip_horizontal
            img = image::imageops::rotate270(&img);
            img = image::imageops::flip_horizontal(&img);
        }
        8 => {
            // rotate 270 CW
            img = image::imageops::rotate270(&img);
        }
        _ => {}
    }

    Ok(img)
}

/// Very simple loader:
/// - Reads the bytes (to prove existence) and forwards a `PreparedPhoto`.
/// - On I/O error, emits `InvalidPhoto`.
pub async fn run(
    mut load_rx: Receiver<LoadPhoto>,
    invalid_tx: Sender<InvalidPhoto>,
    to_viewer: Sender<PhotoLoaded>,
    cancel: CancellationToken,
    max_in_flight: usize,
) -> Result<()> {
    let mut in_flight: std::collections::HashSet<std::path::PathBuf> =
        std::collections::HashSet::new();
    let mut priority_inflight: std::collections::HashSet<std::path::PathBuf> =
        std::collections::HashSet::new();
    // Each decode carries the sequence number it was requested in, so results can
    // be emitted in request order even though they finish out of order.
    let mut tasks: JoinSet<(u64, std::path::PathBuf, Option<image::RgbaImage>)> = JoinSet::new();
    let mut next_seq: u64 = 0;
    let mut reorder = ReorderBuffer::new();
    let mut pending_ready: Option<ReadyPhoto> = None;
    let mut last_sent_path: Option<PathBuf> = None;

    loop {
        // Bound outstanding work (in-flight + buffered) so a slow decode applies
        // backpressure instead of letting the reorder buffer grow without limit.
        let can_accept = next_seq.saturating_sub(reorder.next_emit()) < max_in_flight as u64;

        select! {
            _ = cancel.cancelled() => {
                flush_pending(&mut last_sent_path, &mut pending_ready, &to_viewer).await;
                break;
            },

            // Accept new load requests while the outstanding window has room.
            Some(LoadPhoto { path, priority }) = load_rx.recv(), if can_accept => {
                if priority {
                    priority_inflight.insert(path.clone());
                }
                if in_flight.insert(path.clone()) {
                    let seq = next_seq;
                    next_seq += 1;
                    tasks.spawn({
                        let p = path.clone();
                        async move {
                            let res = tokio::task::spawn_blocking(move || decode_rgba8_apply_exif(&p)).await;
                            (seq, path, res.ok().and_then(|r| r.ok()))
                        }
                    });
                }
                // A duplicate of an already in-flight path is dropped (no seq used);
                // any priority upgrade was recorded above.
            }

            // Handle completed decodes as they finish, then release in request order.
            Some(join_res) = tasks.join_next() => {
                if let Ok((seq, path, maybe_img)) = join_res {
                    in_flight.remove(&path);
                    let priority = priority_inflight.remove(&path);
                    match maybe_img {
                        Some(rgba8) => {
                            debug!("loaded (rgba8): {}", path.display());
                            let (width, height) = rgba8.dimensions();
                            let prepared = PreparedImageCpu { path: path.clone(), width, height, pixels: rgba8.into_raw() };
                            let event = PhotoLoaded { prepared, priority };
                            reorder.insert(seq, Some(ReadyPhoto { path, event }));
                        }
                        None => {
                            debug!("invalid photo {}", path.display());
                            let _ = invalid_tx.send(InvalidPhoto(path)).await;
                            // Mark the slot done so emission can advance past it.
                            reorder.insert(seq, None);
                        }
                    }
                    for ready in reorder.drain_ready() {
                        send_ready(ready, &mut last_sent_path, &mut pending_ready, &to_viewer).await;
                    }
                }
            }

            else => {
                // Channels closed and nothing in flight: drain, flush, exit.
                if in_flight.is_empty() {
                    for ready in reorder.drain_ready() {
                        send_ready(ready, &mut last_sent_path, &mut pending_ready, &to_viewer).await;
                    }
                    flush_pending(&mut last_sent_path, &mut pending_ready, &to_viewer).await;
                    break;
                }
            }
        }
    }
    Ok(())
}

struct ReadyPhoto {
    path: PathBuf,
    event: PhotoLoaded,
}

/// Buffers decoded photos that finished out of order and releases them in the
/// order they were requested. A `None` slot marks a decode that failed (the photo
/// was sent to `invalid_tx`), so emission can advance past it.
struct ReorderBuffer {
    next_emit: u64,
    slots: BTreeMap<u64, Option<ReadyPhoto>>,
}

impl ReorderBuffer {
    fn new() -> Self {
        Self {
            next_emit: 0,
            slots: BTreeMap::new(),
        }
    }

    fn next_emit(&self) -> u64 {
        self.next_emit
    }

    fn insert(&mut self, seq: u64, slot: Option<ReadyPhoto>) {
        self.slots.insert(seq, slot);
    }

    /// Remove and return the next contiguous run of ready photos, in request
    /// order, skipping failed slots.
    fn drain_ready(&mut self) -> Vec<ReadyPhoto> {
        let mut out = Vec::new();
        while let Some(slot) = self.slots.remove(&self.next_emit) {
            self.next_emit += 1;
            if let Some(ready) = slot {
                out.push(ready);
            }
        }
        out
    }
}

async fn send_ready(
    ready: ReadyPhoto,
    last_sent: &mut Option<PathBuf>,
    pending: &mut Option<ReadyPhoto>,
    to_viewer: &Sender<PhotoLoaded>,
) {
    let mut current = Some(ready);
    while let Some(ReadyPhoto { path, event }) = current {
        if last_sent.as_ref() == Some(&path) {
            if pending.is_none() {
                *pending = Some(ReadyPhoto { path, event });
            } else {
                let _ = to_viewer.send(event).await;
                *last_sent = Some(path);
            }
            return;
        } else {
            let _ = to_viewer.send(event).await;
            *last_sent = Some(path);
            current = pending.take();
        }
    }
}

async fn flush_pending(
    last_sent: &mut Option<PathBuf>,
    pending: &mut Option<ReadyPhoto>,
    to_viewer: &Sender<PhotoLoaded>,
) {
    if let Some(ReadyPhoto { path, event }) = pending.take() {
        let _ = to_viewer.send(event).await;
        *last_sent = Some(path);
    }
}

#[cfg(test)]
mod tests {
    use super::*;
    use base64::Engine;
    use tokio::sync::mpsc;

    fn ready_for(path: &str) -> ReadyPhoto {
        let path_buf = PathBuf::from(path);
        let prepared = PreparedImageCpu {
            path: path_buf.clone(),
            width: 1,
            height: 1,
            pixels: vec![0, 0, 0, 0],
        };
        ReadyPhoto {
            path: path_buf,
            event: PhotoLoaded {
                prepared,
                priority: false,
            },
        }
    }

    // JPEG 2x1 with EXIF orientation 6 (rotate 90 CW), base64 encoded
    const ORIENT6_JPEG: &str = concat!(
        "/9j/4AAQSkZJRgABAQAAAQABAAD/4QAiRXhpZgAATU0AKgAAAAgAAQESAAMAAAABAAYAAAAAAAD/2wBDAAgGBgcGBQgHBwcJCQgKDBQNDAsLDBkSEw8UHRofHh0aHBwgJC4nICIsIxwcKDcpLDAxNDQ0Hyc5PTgyPC4zNDL/",
        "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"
    );

    #[test]
    fn applies_orientation_six() {
        let bytes = base64::engine::general_purpose::STANDARD
            .decode(ORIENT6_JPEG)
            .unwrap();
        let dir = tempfile::tempdir().unwrap();
        let path = dir.path().join("orient6.jpg");
        std::fs::write(&path, &bytes).unwrap();
        let img = decode_rgba8_apply_exif(&path).unwrap();
        assert_eq!(img.dimensions(), (1, 2));
    }

    #[tokio::test]
    async fn reorders_single_repeat_when_possible() {
        let (tx, mut rx) = mpsc::channel(4);
        let mut last_sent = None;
        let mut pending = None;

        send_ready(ready_for("a"), &mut last_sent, &mut pending, &tx).await;
        let first = rx.recv().await.unwrap();
        assert_eq!(first.prepared.path, PathBuf::from("a"));
        assert!(!first.priority);
        assert!(pending.is_none());

        send_ready(ready_for("a"), &mut last_sent, &mut pending, &tx).await;
        assert!(pending.is_some());
        assert!(rx.try_recv().is_err());

        send_ready(ready_for("b"), &mut last_sent, &mut pending, &tx).await;
        let second = rx.recv().await.unwrap();
        assert_eq!(second.prepared.path, PathBuf::from("b"));
        assert!(!second.priority);
        let third = rx.recv().await.unwrap();
        assert_eq!(third.prepared.path, PathBuf::from("a"));
        assert!(!third.priority);
        assert!(pending.is_none());
        assert_eq!(last_sent, Some(PathBuf::from("a")));
    }

    #[tokio::test]
    async fn flushes_pending_when_nothing_else_arrives() {
        let (tx, mut rx) = mpsc::channel(4);
        let mut last_sent = None;
        let mut pending = None;

        send_ready(ready_for("a"), &mut last_sent, &mut pending, &tx).await;
        assert_eq!(rx.recv().await.unwrap().prepared.path, PathBuf::from("a"));

        send_ready(ready_for("a"), &mut last_sent, &mut pending, &tx).await;
        assert!(pending.is_some());
        assert!(rx.try_recv().is_err());

        flush_pending(&mut last_sent, &mut pending, &tx).await;
        let flushed = rx.recv().await.unwrap();
        assert_eq!(flushed.prepared.path, PathBuf::from("a"));
        assert!(!flushed.priority);
        assert!(pending.is_none());
        assert_eq!(last_sent, Some(PathBuf::from("a")));
    }

    fn ready_paths(items: &[ReadyPhoto]) -> Vec<String> {
        items
            .iter()
            .map(|r| r.path.to_string_lossy().into_owned())
            .collect()
    }

    #[test]
    fn reorder_buffer_emits_in_request_order_skipping_invalid() {
        let mut buf = ReorderBuffer::new();

        // seq 2 finishes first — nothing emits until seq 0 arrives.
        buf.insert(2, Some(ready_for("c")));
        assert!(ready_paths(&buf.drain_ready()).is_empty());

        // seq 0 arrives — emit only 0 (still waiting on 1).
        buf.insert(0, Some(ready_for("a")));
        assert_eq!(ready_paths(&buf.drain_ready()), ["a"]);

        // seq 1 failed (invalid) — skip it and release the buffered seq 2.
        buf.insert(1, None);
        assert_eq!(ready_paths(&buf.drain_ready()), ["c"]);

        // seq 3 arrives in order.
        buf.insert(3, Some(ready_for("d")));
        assert_eq!(ready_paths(&buf.drain_ready()), ["d"]);

        assert_eq!(buf.next_emit(), 4);
    }
}
