vincentl/rust-photo-frame/crates/wifi-manager/src/nm.rs

use crate::config::{Config, HotspotConfig};
use anyhow::{Context, Result, anyhow};
use clap::{Args, Subcommand};
use std::collections::HashSet;
use std::process::Stdio;
use std::time::Duration;
use tokio::process::Command;
use tracing::{debug, info, warn};

#[derive(Debug, Subcommand)]
pub enum NmCommand {
    /// Ensure the hotspot profile exists and is configured for AP mode.
    EnsureHotspot,
    /// Bring the pf-hotspot connection up.
    HotspotUp,
    /// Bring the pf-hotspot connection down.
    HotspotDown,
    /// Add or update a Wi-Fi connection with the provided SSID/PSK.
    Add(AddArgs),
}

#[derive(Debug, Args)]
pub struct AddArgs {
    #[arg(long)]
    pub ssid: String,
    #[arg(long)]
    pub psk: String,
}

pub async fn handle_cli(cmd: NmCommand, config: &Config) -> Result<()> {
    match cmd {
        NmCommand::EnsureHotspot => {
            ensure_hotspot_profile(&config.hotspot, &config.interface, None).await?
        }
        NmCommand::HotspotUp => bring_hotspot_up(&config.hotspot).await?,
        NmCommand::HotspotDown => bring_hotspot_down(&config.hotspot).await?,
        NmCommand::Add(args) => {
            add_or_update_wifi(&config.interface, &args.ssid, &args.psk).await?;
        }
    }
    Ok(())
}

pub async fn device_connected(interface: &str) -> Result<bool> {
    let output = nmcli(&["-t", "-f", "DEVICE,STATE", "device", "status"]).await?;
    for line in output.lines() {
        let mut parts = line.split(':');
        if let (Some(dev), Some(state)) = (parts.next(), parts.next())
            && dev == interface
        {
            return Ok(state == "connected" || state == "activated" || state == "full");
        }
    }
    Ok(false)
}

pub async fn active_connection_id(interface: &str) -> Result<Option<String>> {
    let output = nmcli(&[
        "-t",
        "-f",
        "GENERAL.CONNECTION",
        "device",
        "show",
        interface,
    ])
    .await?;
    for line in output.lines() {
        if let Some(value) = parse_nmcli_value(line) {
            if value == "--" {
                return Ok(None);
            }
            return Ok(Some(value));
        }
    }
    Ok(None)
}

pub async fn connected_to_infrastructure(
    interface: &str,
    hotspot_connection_id: &str,
) -> Result<bool> {
    if !device_connected(interface).await? {
        return Ok(false);
    }

    match active_connection_id(interface).await? {
        Some(active) if active == hotspot_connection_id => Ok(false),
        Some(_) => Ok(true),
        None => Ok(false),
    }
}

pub async fn gateway_reachable(interface: &str) -> Result<bool> {
    let gw = default_gateway(interface).await?;
    if let Some(gw) = gw {
        let status = Command::new("ping")
            .arg("-c")
            .arg("1")
            .arg("-W")
            .arg("2")
            .arg(&gw)
            .status()
            .await
            .with_context(|| format!("failed to spawn ping for gateway {gw}"))?;
        return Ok(status.success());
    }
    Ok(false)
}

async fn default_gateway(interface: &str) -> Result<Option<String>> {
    let output = nmcli(&["-t", "-f", "IP4.GATEWAY", "device", "show", interface]).await?;
    for line in output.lines() {
        if let Some(value) = parse_nmcli_value(line) {
            return Ok(Some(value));
        }
    }
    Ok(None)
}

fn parse_nmcli_value(line: &str) -> Option<String> {
    let trimmed = line.trim();
    if trimmed.is_empty() {
        return None;
    }

    let mut parts = trimmed.splitn(2, ':');
    let value = match (parts.next(), parts.next()) {
        (Some(_key), Some(val)) => val.trim(),
        (Some(val), None) => val.trim(),
        _ => return None,
    };

    if value.is_empty() {
        None
    } else {
        Some(value.to_string())
    }
}

pub async fn ensure_hotspot_profile(
    hotspot: &HotspotConfig,
    interface: &str,
    password: Option<&str>,
) -> Result<()> {
    let hotspot_ipv4_cidr = format!("{}/24", hotspot.ipv4_addr);
    let existing = list_connection_names().await?;
    if existing.contains(&hotspot.connection_id) {
        debug!(id = %hotspot.connection_id, "hotspot profile already exists; ensuring settings");
        nmcli(&[
            "connection",
            "modify",
            &hotspot.connection_id,
            "connection.autoconnect",
            "no",
        ])
        .await?;
        nmcli(&[
            "connection",
            "modify",
            &hotspot.connection_id,
            "802-11-wireless.mode",
            "ap",
        ])
        .await?;
        nmcli(&[
            "connection",
            "modify",
            &hotspot.connection_id,
            "802-11-wireless.band",
            "bg",
        ])
        .await?;
        nmcli(&[
            "connection",
            "modify",
            &hotspot.connection_id,
            "802-11-wireless.ssid",
            &hotspot.ssid,
        ])
        .await?;
        nmcli(&[
            "connection",
            "modify",
            &hotspot.connection_id,
            "ipv4.method",
            "shared",
        ])
        .await?;
        nmcli(&[
            "connection",
            "modify",
            &hotspot.connection_id,
            "ipv4.addresses",
            &hotspot_ipv4_cidr,
        ])
        .await?;
        nmcli(&[
            "connection",
            "modify",
            &hotspot.connection_id,
            "ipv6.method",
            "ignore",
        ])
        .await?;
        if let Some(pass) = password {
            nmcli(&[
                "connection",
                "modify",
                &hotspot.connection_id,
                "wifi-sec.key-mgmt",
                "wpa-psk",
            ])
            .await?;
            nmcli(&[
                "connection",
                "modify",
                &hotspot.connection_id,
                "wifi-sec.psk",
                pass,
            ])
            .await?;
        }
    } else {
        info!(id = %hotspot.connection_id, "creating hotspot profile");
        add_hotspot_profile(&hotspot.connection_id, &hotspot.ssid, interface).await?;
        nmcli(&[
            "connection",
            "modify",
            &hotspot.connection_id,
            "802-11-wireless.mode",
            "ap",
        ])
        .await?;
        nmcli(&[
            "connection",
            "modify",
            &hotspot.connection_id,
            "802-11-wireless.band",
            "bg",
        ])
        .await?;
        nmcli(&[
            "connection",
            "modify",
            &hotspot.connection_id,
            "ipv4.method",
            "shared",
        ])
        .await?;
        nmcli(&[
            "connection",
            "modify",
            &hotspot.connection_id,
            "ipv4.addresses",
            &hotspot_ipv4_cidr,
        ])
        .await?;
        nmcli(&[
            "connection",
            "modify",
            &hotspot.connection_id,
            "ipv6.method",
            "ignore",
        ])
        .await?;
        if let Some(pass) = password {
            nmcli(&[
                "connection",
                "modify",
                &hotspot.connection_id,
                "wifi-sec.key-mgmt",
                "wpa-psk",
            ])
            .await?;
            nmcli(&[
                "connection",
                "modify",
                &hotspot.connection_id,
                "wifi-sec.psk",
                pass,
            ])
            .await?;
        }
    }
    if let Some(pass) = password {
        nmcli(&[
            "connection",
            "modify",
            &hotspot.connection_id,
            "wifi-sec.key-mgmt",
            "wpa-psk",
        ])
        .await?;
        nmcli(&[
            "connection",
            "modify",
            &hotspot.connection_id,
            "wifi-sec.psk",
            pass,
        ])
        .await?;
    }
    Ok(())
}

async fn add_hotspot_profile(connection_id: &str, ssid: &str, interface: &str) -> Result<()> {
    let add_args = [
        "connection",
        "add",
        "type",
        "wifi",
        "ifname",
        interface,
        "con-name",
        connection_id,
        "autoconnect",
        "no",
        "ssid",
        ssid,
    ];

    match nmcli(&add_args).await {
        Ok(_) => Ok(()),
        Err(err) if should_retry_with_wildcard(&err) => {
            warn!(
                error = ?err,
                interface,
                "failed to bind hotspot to interface; retrying with wildcard"
            );
            let wildcard_args = [
                "connection",
                "add",
                "type",
                "wifi",
                "ifname",
                "*",
                "con-name",
                connection_id,
                "autoconnect",
                "no",
                "ssid",
                ssid,
            ];
            nmcli(&wildcard_args).await.map(|_| ())
        }
        Err(err) => Err(err),
    }
}

fn should_retry_with_wildcard(err: &anyhow::Error) -> bool {
    let msg = err.to_string().to_lowercase();
    let mentions_ifname = msg.contains("ifname") || msg.contains("interface");
    let indicates_missing_device = msg.contains("not available")
        || msg.contains("no device")
        || msg.contains("not found")
        || msg.contains("not valid")
        || msg.contains("is unavailable");
    mentions_ifname && indicates_missing_device
}

pub async fn bring_hotspot_up(hotspot: &HotspotConfig) -> Result<()> {
    nmcli(&["connection", "up", &hotspot.connection_id]).await?;
    Ok(())
}

pub async fn bring_hotspot_down(hotspot: &HotspotConfig) -> Result<()> {
    let res = nmcli(&["connection", "down", &hotspot.connection_id]).await;
    match res {
        Ok(_) => Ok(()),
        Err(err) => {
            debug!(error = ?err, "failed to bring hotspot down (continuing)");
            Ok(())
        }
    }
}

pub async fn add_or_update_wifi(interface: &str, ssid: &str, psk: &str) -> Result<String> {
    let connection_id = format!("pf-wifi-{}", sanitize_id(ssid));
    ensure_psk_rules(psk)?;
    let existing = list_connection_names().await?;
    if existing.contains(&connection_id) {
        info!(connection = %connection_id, "updating stored credentials");
        nmcli(&[
            "connection",
            "modify",
            &connection_id,
            "802-11-wireless.ssid",
            ssid,
        ])
        .await?;
        nmcli(&[
            "connection",
            "modify",
            &connection_id,
            "wifi-sec.key-mgmt",
            "wpa-psk",
        ])
        .await?;
        nmcli(&["connection", "modify", &connection_id, "wifi-sec.psk", psk]).await?;
        // Keep autoconnect disabled during the provisioning attempt so
        // NetworkManager does not race to activate this profile while the
        // recovery hotspot is still tearing down.  The caller enables it
        // after confirming a successful connection.
        nmcli(&[
            "connection",
            "modify",
            &connection_id,
            "connection.autoconnect",
            "no",
        ])
        .await?;
    } else {
        info!(connection = %connection_id, "adding new Wi-Fi connection profile");
        nmcli(&[
            "connection",
            "add",
            "type",
            "wifi",
            "ifname",
            interface,
            "con-name",
            &connection_id,
            "ssid",
            ssid,
            "wifi-sec.key-mgmt",
            "wpa-psk",
            "wifi-sec.psk",
            psk,
            // Autoconnect is intentionally off until the caller confirms the
            // connection is live; this prevents NM from competing with the
            // explicit activation request while the hotspot is still active.
            "connection.autoconnect",
            "no",
        ])
        .await?;
    }
    Ok(connection_id)
}

/// Enable autoconnect on a saved connection profile so NetworkManager
/// activates it automatically on future boots.
pub async fn enable_connection_autoconnect(connection_id: &str) -> Result<()> {
    nmcli(&[
        "connection",
        "modify",
        connection_id,
        "connection.autoconnect",
        "yes",
    ])
    .await?;
    Ok(())
}

pub async fn activate_connection(connection_id: &str) -> Result<()> {
    nmcli(&["connection", "up", connection_id]).await?;
    Ok(())
}

/// Delete a saved connection profile (best-effort). Used to remove a
/// `pf-wifi-*` profile whose provisioning attempt failed, so wrong-credential
/// profiles don't accumulate in NetworkManager across repeated attempts.
pub async fn delete_connection(connection_id: &str) -> Result<()> {
    nmcli(&["connection", "delete", connection_id]).await?;
    Ok(())
}

async fn list_connection_names() -> Result<HashSet<String>> {
    let output = nmcli(&["-t", "-f", "NAME", "connection", "show"]).await?;
    Ok(output
        .lines()
        .map(|line| line.trim().to_string())
        .filter(|s| !s.is_empty())
        .collect())
}

fn sanitize_id(ssid: &str) -> String {
    let mut id = ssid
        .chars()
        .map(|c| if c.is_ascii_alphanumeric() { c } else { '-' })
        .collect::<String>();
    if id.is_empty() {
        id.push('x');
    }
    if id.len() > 20 {
        id.truncate(20);
    }
    id.to_lowercase()
}

fn ensure_psk_rules(psk: &str) -> Result<()> {
    // WPA/WPA2 passphrases are 8-63 *bytes* (not characters). Validating the byte
    // length matches what nmcli/wpa_supplicant enforce, so a multibyte passphrase
    // gets a clear error here instead of an opaque downstream nmcli failure.
    let len = psk.len();
    if (8..=63).contains(&len) {
        Ok(())
    } else {
        Err(anyhow!("Password must be between 8 and 63 bytes"))
    }
}

/// Hard cap on any single nmcli invocation. nmcli talks to NetworkManager over
/// D-Bus, which can wedge (NM restarting, bus under load) and otherwise hang the
/// whole watcher loop indefinitely; a timeout turns that into a transient error.
const NMCLI_TIMEOUT: Duration = Duration::from_secs(20);

async fn nmcli(args: &[&str]) -> Result<String> {
    debug!(command = %display_args(args), "running nmcli");
    let mut cmd = Command::new("nmcli");
    cmd.args(args);
    cmd.stdout(Stdio::piped());
    cmd.stderr(Stdio::piped());
    let output = tokio::time::timeout(NMCLI_TIMEOUT, cmd.output())
        .await
        .map_err(|_| {
            anyhow!(
                "nmcli {} timed out after {}s",
                display_args(args),
                NMCLI_TIMEOUT.as_secs()
            )
        })?
        .context("failed to execute nmcli")?;
    if output.status.success() {
        Ok(String::from_utf8_lossy(&output.stdout).to_string())
    } else {
        let stderr = String::from_utf8_lossy(&output.stderr);
        Err(anyhow!(
            "nmcli {} failed: {}",
            display_args(args),
            stderr.trim()
        ))
    }
}

/// Returns `true` if at least one wireless client is currently associated with
/// the AP on `interface`.
///
/// Runs `iw dev <interface> station dump`.  Non-empty stdout means at least one
/// station entry is present.  On any error we return `false` so that probe
/// decisions fail-safe: we would rather probe unnecessarily than permanently
/// suppress probing because `iw` is unavailable.
pub async fn has_ap_clients(interface: &str) -> bool {
    match Command::new("iw")
        .args(["dev", interface, "station", "dump"])
        .output()
        .await
    {
        Ok(output) => !output.stdout.is_empty(),
        Err(err) => {
            debug!(error = ?err, "iw station dump failed; assuming no AP clients");
            false
        }
    }
}

fn display_args(args: &[&str]) -> String {
    let mut masked = Vec::with_capacity(args.len());
    let mut skip_next = false;
    for arg in args.iter() {
        if skip_next {
            masked.push("<redacted>");
            skip_next = false;
            continue;
        }
        if matches!(*arg, "wifi-sec.psk" | "psk") {
            masked.push(arg);
            skip_next = true;
        } else {
            masked.push(arg);
        }
    }
    masked.join(" ")
}
