vincentl/rust-photo-frame/crates/wifi-manager/src/watch.rs

use crate::config::{Config, RecoveryMode};
use crate::hotspot;
use crate::nm;
use crate::overlay::{OverlayController, overlay_request};
use crate::qr;
use crate::status::{
    AttemptRecord, ProvisionRequest, RuntimeStateRecord, now_rfc3339, read_request, redact_ssid,
    remove_request, write_last_attempt, write_last_ssid, write_runtime_state,
};
use anyhow::{Context, Result};
use rand::Rng;
use std::fs;
use std::path::PathBuf;
use std::process::Stdio;
use std::time::{Duration, Instant};
use tokio::process::{Child, Command};
use tokio::signal::unix::{SignalKind, signal};
use tokio::time::sleep;
use tracing::{debug, error, info, warn};

/// Seconds to wait after queuing credentials before tearing down the hotspot.
/// This gives the recovery portal time to deliver its final HTTP response to
/// the browser before the AP interface disappears.
const POST_SUBMIT_SETTLE_SECS: u64 = 3;

/// Seconds to wait after the hotspot is deactivated before asking
/// NetworkManager to activate the infrastructure connection.  This lets NM
/// finish releasing the radio from AP mode so the subsequent `connection up`
/// does not race with the interface state transition.
const NM_SETTLE_SECS: u64 = 2;

pub async fn run(config: Config, config_path: PathBuf) -> Result<()> {
    fs::create_dir_all(&config.var_dir)
        .with_context(|| format!("failed to create var dir at {}", config.var_dir.display()))?;

    let mut state = WatchState::Online;
    let mut offline_since: Option<Instant> = None;
    let mut backoff_until: Option<Instant> = None;
    let mut recovery: Option<ActiveRecovery> = None;
    let mut overlay = OverlayController::new(config.overlay.clone());

    if config.photo_app.app_id != config.overlay.photo_app_id {
        warn!(
            photo_app_id = %config.photo_app.app_id,
            overlay_photo_app_id = %config.overlay.photo_app_id,
            "photo-app.app-id and overlay.photo-app-id differ; prefer keeping them aligned"
        );
    }

    transition_state(&config, &mut state, WatchState::Online, "startup", None);

    let mut sigterm =
        signal(SignalKind::terminate()).context("failed to register SIGTERM handler")?;
    let mut sigint =
        signal(SignalKind::interrupt()).context("failed to register SIGINT handler")?;

    loop {
        tokio::select! {
            _ = sigterm.recv() => {
                info!("received SIGTERM; shutting down");
                shutdown_recovery(&config, &mut recovery, &mut overlay).await;
                return Ok(());
            }
            _ = sigint.recv() => {
                info!("received SIGINT; shutting down");
                shutdown_recovery(&config, &mut recovery, &mut overlay).await;
                return Ok(());
            }
            _ = async {
                let online = match check_online_link(&config).await {
                    Ok(result) => result,
                    Err(err) => {
                        warn!(error = ?err, "connectivity check failed; assuming offline");
                        false
                    }
                };

                match state {
                    WatchState::Online => {
                        if !online {
                            offline_since = Some(Instant::now());
                            transition_state(
                                &config,
                                &mut state,
                                WatchState::OfflineGrace,
                                "link-lost",
                                None,
                            );
                        }
                    }
                    WatchState::OfflineGrace => {
                        if online {
                            offline_since = None;
                            transition_state(
                                &config,
                                &mut state,
                                WatchState::Online,
                                "link-restored-before-grace",
                                None,
                            );
                        } else if let Some(since) = offline_since
                            && since.elapsed().as_secs() >= config.offline_grace_sec
                        {
                            match enter_recovery(&config, &config_path, &mut overlay).await {
                                Ok(active) => {
                                    recovery = Some(active);
                                    backoff_until = None;
                                    transition_state(
                                        &config,
                                        &mut state,
                                        WatchState::RecoveryHotspotActive,
                                        "offline-grace-expired",
                                        None,
                                    );
                                }
                                Err(err) => {
                                    error!(error = ?err, "failed to start recovery mode");
                                    backoff_until = Some(Instant::now() + Duration::from_secs(3));
                                    transition_state(
                                        &config,
                                        &mut state,
                                        WatchState::RecoveryBackoff,
                                        "recovery-start-failed",
                                        None,
                                    );
                                }
                            }
                        }
                    }
                    WatchState::RecoveryHotspotActive => {
                        if recovery.is_none() {
                            match enter_recovery(&config, &config_path, &mut overlay).await {
                                Ok(active) => {
                                    recovery = Some(active);
                                    transition_state(
                                        &config,
                                        &mut state,
                                        WatchState::RecoveryHotspotActive,
                                        "recovery-session-rebuilt",
                                        None,
                                    );
                                }
                                Err(err) => {
                                    error!(
                                        error = ?err,
                                        "failed to rebuild recovery session while in hotspot state"
                                    );
                                    backoff_until =
                                        Some(Instant::now() + Duration::from_secs(3));
                                    transition_state(
                                        &config,
                                        &mut state,
                                        WatchState::RecoveryBackoff,
                                        "recovery-rebuild-failed",
                                        None,
                                    );
                                }
                            }
                        } else if online {
                            finalize_recovery(
                                &config,
                                &mut recovery,
                                &mut overlay,
                                "link-restored",
                                None,
                            )
                            .await;
                            offline_since = None;
                            backoff_until = None;
                            transition_state(
                                &config,
                                &mut state,
                                WatchState::Online,
                                "link-restored",
                                None,
                            );
                        } else {
                            let request = match read_request(&config) {
                                Ok(value) => value,
                                Err(err) => {
                                    warn!(error = ?err, "failed to read provisioning request");
                                    None
                                }
                            };

                            if let Some(request) = request {
                                transition_state(
                                    &config,
                                    &mut state,
                                    WatchState::ProvisioningAttempt,
                                    "provision-request",
                                    Some(&request.attempt_id),
                                );
                                let outcome = apply_provision_request(
                                    &config,
                                    &request,
                                    &mut recovery,
                                    &mut overlay,
                                )
                                .await;
                                if let Err(err) = remove_request(&config) {
                                    warn!(error = ?err, "failed to clear provisioning request file");
                                }
                                match outcome {
                                    ProvisionOutcome::Connected => {
                                        finalize_recovery(
                                            &config,
                                            &mut recovery,
                                            &mut overlay,
                                            "provision-success",
                                            Some(&request.attempt_id),
                                        )
                                        .await;
                                        offline_since = None;
                                        backoff_until = None;
                                        transition_state(
                                            &config,
                                            &mut state,
                                            WatchState::Online,
                                            "provision-success",
                                            Some(&request.attempt_id),
                                        );
                                    }
                                    ProvisionOutcome::Failed => {
                                        backoff_until =
                                            Some(Instant::now() + Duration::from_secs(3));
                                        transition_state(
                                            &config,
                                            &mut state,
                                            WatchState::RecoveryBackoff,
                                            "provision-failed",
                                            Some(&request.attempt_id),
                                        );
                                    }
                                }
                            } else if should_run_reconnect_probe(&config, &recovery) {
                                if nm::has_ap_clients(&config.interface).await {
                                    // A phone or laptop is currently associated with the AP.
                                    // Tearing down the hotspot to probe would disconnect them
                                    // mid-session, so skip this probe tick.
                                    debug!("skipping reconnect probe: AP has active client(s)");
                                } else {
                                    let probe_success = run_reconnect_probe(
                                        &config,
                                        &mut recovery,
                                        &mut overlay,
                                    )
                                    .await;
                                    if probe_success {
                                        finalize_recovery(
                                            &config,
                                            &mut recovery,
                                            &mut overlay,
                                            "probe-success",
                                            None,
                                        )
                                        .await;
                                        offline_since = None;
                                        backoff_until = None;
                                        transition_state(
                                            &config,
                                            &mut state,
                                            WatchState::Online,
                                            "probe-success",
                                            None,
                                        );
                                    } else {
                                        backoff_until =
                                            Some(Instant::now() + Duration::from_secs(3));
                                        transition_state(
                                            &config,
                                            &mut state,
                                            WatchState::RecoveryBackoff,
                                            "probe-failed",
                                            None,
                                        );
                                    }
                                }
                            }
                        }
                    }
                    WatchState::ProvisioningAttempt => {
                        transition_state(
                            &config,
                            &mut state,
                            WatchState::RecoveryHotspotActive,
                            "provisioning-idle",
                            None,
                        );
                    }
                    WatchState::RecoveryBackoff => {
                        if online {
                            finalize_recovery(
                                &config,
                                &mut recovery,
                                &mut overlay,
                                "link-restored-during-backoff",
                                None,
                            )
                            .await;
                            offline_since = None;
                            backoff_until = None;
                            transition_state(
                                &config,
                                &mut state,
                                WatchState::Online,
                                "link-restored-during-backoff",
                                None,
                            );
                        } else if backoff_until
                            .map(|deadline| Instant::now() >= deadline)
                            .unwrap_or(true)
                        {
                            if recovery.is_some() {
                                transition_state(
                                    &config,
                                    &mut state,
                                    WatchState::RecoveryHotspotActive,
                                    "backoff-expired",
                                    None,
                                );
                            } else {
                                match enter_recovery(&config, &config_path, &mut overlay).await {
                                    Ok(active) => {
                                        recovery = Some(active);
                                        transition_state(
                                            &config,
                                            &mut state,
                                            WatchState::RecoveryHotspotActive,
                                            "backoff-recovery-retry-success",
                                            None,
                                        );
                                    }
                                    Err(err) => {
                                        error!(
                                            error = ?err,
                                            "failed to start recovery session after backoff"
                                        );
                                        backoff_until =
                                            Some(Instant::now() + Duration::from_secs(3));
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
